pillepalle127/ESP32S3_Mesh_Snapserver/main/app_main.c

/**
 * @file app_main.c
 * @brief Initializes NVS, networking, Mesh-Lite, audio, streaming and control services.
 */
#include "esp_err.h"
#include "esp_event.h"
#include "esp_log.h"
#include "esp_netif.h"
#include "nvs_flash.h"
#include "snapcontrol.h"

#include "audio_i2s.h"
#include "audio_opus.h"
#include "audio_sink.h"
#include "device_config.h"
#include "mesh_client.h"
#include "mesh_root.h"
#include "snapserver.h"
#include "status_led.h"
#include "pots.h"
#include "power_button.h"
#include "voice_announce.h"
#include "webconfig.h"

static const char *TAG = "APP";

static esp_err_t initialize_nvs(void)
{
    esp_err_t result = nvs_flash_init();

    if (result == ESP_ERR_NVS_NO_FREE_PAGES ||
        result == ESP_ERR_NVS_NEW_VERSION_FOUND) {
        ESP_LOGW(
            TAG,
            "NVS partition must be erased: %s",
            esp_err_to_name(result));

        result = nvs_flash_erase();
        if (result != ESP_OK) {
            ESP_LOGE(
                TAG,
                "NVS erase failed: %s",
                esp_err_to_name(result));
            return result;
        }

        result = nvs_flash_init();
    }

    if (result != ESP_OK) {
        ESP_LOGE(
            TAG,
            "NVS initialization failed: %s",
            esp_err_to_name(result));
        return result;
    }

    ESP_LOGI(TAG, "NVS initialized");
    return ESP_OK;
}

static esp_err_t initialize_network_stack(void)
{
    esp_err_t result = esp_netif_init();
    if (result != ESP_OK) {
        ESP_LOGE(
            TAG,
            "TCP/IP stack initialization failed: %s",
            esp_err_to_name(result));
        return result;
    }

    result = esp_event_loop_create_default();
    if (result != ESP_OK && result != ESP_ERR_INVALID_STATE) {
        ESP_LOGE(
            TAG,
            "Default event loop initialization failed: %s",
            esp_err_to_name(result));
        return result;
    }

    ESP_LOGI(TAG, "TCP/IP stack initialized");
    return ESP_OK;
}

void app_main(void)
{
    ESP_LOGI(TAG, "Starting ESP32-S3 Mini Snapserver");

    /* Before anything claims a pin the last switch-off may still hold, and
     * before NVS: a wake-up that goes back to sleep must not count as a
     * boot of a pin set on trial (device_config_load()). */
    power_button_boot();

    ESP_ERROR_CHECK(initialize_nvs());
    ESP_ERROR_CHECK(initialize_network_stack());
    ESP_ERROR_CHECK(device_config_load());

    device_config_t cfg;
    device_config_get(&cfg);
    /* Up before the radio, so the very first thing the LED shows is that
     * the board is alive and the GPIO is right. */
    (void)status_led_start();

    /* Early, so the device can be switched off even if the mesh hangs.
     * Not fatal: without the button it simply stays on. */
    {
        device_pins_t pins;
        device_config_get_pins(&pins);
        const esp_err_t button_result = power_button_start(&pins);
        if (button_result != ESP_OK && button_result != ESP_ERR_NOT_SUPPORTED) {
            ESP_LOGW(TAG, "Power button unavailable: %s", esp_err_to_name(button_result));
        }
    }

    const bool client_role = (cfg.role == DEVICE_ROLE_CLIENT);

    esp_err_t result = client_role ? mesh_client_start() : mesh_root_start();
    if (result != ESP_OK) {
        ESP_LOGE(
            TAG,
            "Mesh %s initialization failed: %s",
            client_role ? "client" : "root",
            esp_err_to_name(result));
        ESP_ERROR_CHECK(result);
    }

    /*
     * Bring the config page up before audio: if I2S/Opus init fails below,
     * ESP_ERROR_CHECK() still panics and reboots the device (that failure
     * stays fatal, unchanged), but the panic-and-reboot loop at least
     * leaves a window where the provisioning/mesh AP and config page were
     * already reachable, instead of never existing at all.
     */
    ESP_ERROR_CHECK(webconfig_start());

    /*
     * Both roles need the physical I2S bus (the client plays out over the
     * same DSP/output stage the server uses, and also captures its own
     * local-input substitute source from it). audio_i2s_start() is
     * idempotent, so the server's subsequent audio_opus_start() -- which
     * also calls it -- is a harmless no-op the second time.
     */
    ESP_ERROR_CHECK(audio_i2s_start());

    /* The volume set for this speaker on the page or in the app. */
    {
        device_local_volume_t local_volume;
        device_config_get_local_volume(&local_volume);
        audio_i2s_set_user_volume(local_volume.percent, local_volume.muted != 0U);
    }

    const audio_dsp_params_t dsp_params = {
        .bypass = cfg.dsp_bypass,
        .crossover_hz = (float)cfg.crossover_hz,
        .sub_gain_db = cfg.sub_gain_db,
        .wideband_gain_db = cfg.wideband_gain_db,
        .sub_hpf_hz = (float)cfg.sub_hpf_hz,
        .sub_invert = cfg.sub_invert != 0U,
        .comp_enable = cfg.comp_enable != 0U,
        .comp_threshold_db = (float)cfg.comp_threshold_db,
        .comp_ratio = (float)cfg.comp_ratio_x10 / 10.0f,
        .comp_makeup_db = (float)cfg.comp_makeup_db,
        .sub_channel = cfg.sub_channel,
        .wideband_channel = cfg.wideband_channel,
    };
    ESP_ERROR_CHECK(audio_i2s_set_dsp_params(&dsp_params));

    /*
     * Not fatal: without a volume knob the output stage stays at the full
     * volume it defaults to, and without a delay knob the trim from the
     * config applies -- exactly what a board with nothing fitted should do.
     */
    device_pots_t pots;
    device_config_get_pots(&pots);
    result = pots_start(&pots);
    if (result != ESP_OK && result != ESP_ERR_NOT_SUPPORTED) {
        ESP_LOGW(TAG,
                 "Knob inputs unavailable: %s -- full volume, delay trim from config",
                 esp_err_to_name(result));
    }

    if (client_role) {
        ESP_ERROR_CHECK(audio_sink_start());

        /* The server's last volume for this client, until it sends a new one. */
        {
            device_local_volume_t stream_volume;
            device_config_get_stream_volume(&stream_volume);
            audio_sink_set_volume(stream_volume.percent, stream_volume.muted != 0U);
        }
        audio_sink_set_source_mode(cfg.source_mode);
        audio_sink_set_local_input_threshold_db(cfg.local_input_threshold_db);
        audio_sink_set_delay_trim_ms(cfg.delay_trim_ms);
        /* After the configured trim, so the knob's first reading wins. */
        pots_enable_delay(cfg.role, cfg.buffer_ms);

        result = voice_receive_start();
        if (result != ESP_OK) {
            ESP_LOGW(
                TAG,
                "Voice announcement receiver failed to start: %s -- "
                "music playback is unaffected, announcements just won't "
                "be heard on this device",
                esp_err_to_name(result));
        }

        /* Everything that touches a configured pin is up. */
        device_config_confirm_pins();

        ESP_LOGI(
            TAG,
            "ESP32-S3 Snapclient started: mesh relay, local I2S input as "
            "alternate source, Snapcast mono Opus playback");
        return;
    }

    /*
     * Hold this device's own speaker back by the same amount every client
     * delays the stream, otherwise the server -- which hears a frame right
     * after capturing it -- runs a full bufferMs ahead of them in the same
     * room. The clients' scheduler uses chunk_ts + bufferMs - latency +
     * delay_trim_ms; latency is per-client and always 0 today, so the same
     * rule here is buffer_ms + delay_trim_ms. The buffer is sized for the
     * full delay_trim_ms range so the trim stays adjustable while playing.
     */
    const int32_t local_delay_ms = (int32_t)cfg.buffer_ms + cfg.delay_trim_ms;
    ESP_ERROR_CHECK(audio_i2s_set_output_delay(
        (uint32_t)(local_delay_ms > 0 ? local_delay_ms : 0),
        (uint32_t)cfg.buffer_ms + DEVICE_CONFIG_DELAY_TRIM_MAX_MS));
    /* After the delay line exists and holds the configured trim, so the
     * knob's first reading replaces it rather than racing it. */
    pots_enable_delay(cfg.role, cfg.buffer_ms);

    result = audio_opus_start();
    if (result != ESP_OK) {
        ESP_LOGE(
            TAG,
            "Opus audio initialization failed: %s",
            esp_err_to_name(result));
        ESP_ERROR_CHECK(result);
    }
    audio_opus_set_bitrate((int32_t)cfg.opus_bitrate);
    audio_opus_set_complexity((int32_t)cfg.opus_complexity);

    result = snapserver_start();
    if (result == ESP_OK) {
        /* The server always plays its own local output, so green from here
         * on and the brightness follows what leaves its crossover. */
        status_led_set_state(STATUS_LED_PLAYING);
    }

    if (result != ESP_OK) {
        ESP_LOGE(
            TAG,
            "Snapserver initialization failed: %s",
            esp_err_to_name(result));
        ESP_ERROR_CHECK(result);
    }
	ESP_ERROR_CHECK(snapcontrol_start());

    result = voice_announce_start();
    if (result != ESP_OK) {
        ESP_LOGW(
            TAG,
            "Voice announcement server failed to start: %s -- "
            "music streaming is unaffected, announcements just won't be "
            "available",
            esp_err_to_name(result));
    }

    device_config_confirm_pins();

    ESP_LOGI(
        TAG,
        "ESP32-S3 Snapserver started: TinySine stereo input, PCM5102A stereo output, Snapcast mono Opus");
}
