pillepalle127/ESP32S3_Mesh_Snapserver/main/snapclient.c

/**
 * @file snapclient.c
 * @brief Snapcast protocol client -- TCP connection, Hello, CodecHeader,
 *        WireChunk/Opus decode, feeding audio_sink.c.
 *
 * See snapclient.h for provenance.
 *
 * Periodic SNAP_MSG_TIME requests serve two purposes at once. They carry
 * the clock synchronisation (four-timestamp exchange, least-delayed
 * measurement of a sliding window wins -- see handle_time_reply()), whose
 * result feeds audio_sink.c's playback scheduler. They are also the
 * keepalive the server requires: its client_task() drops a connection
 * after CLIENT_RECV_TIMEOUT_US (30 s, see snapserver.c) of silence *from*
 * the client, which a real Snapcast client never hits precisely because
 * its own time requests count as inbound traffic. Without them our client
 * was disconnected every ~30 s despite a perfectly healthy stream
 * (confirmed on-device, 2026-09-17).
 */
#include "snapclient.h"

#include <errno.h>
#include <fcntl.h>
#include <stdio.h>
#include <stdlib.h>
#include <string.h>
#include <sys/socket.h>
#include <sys/time.h>
#include <sys/select.h>
#include <netdb.h>
#include <unistd.h>

#include "freertos/FreeRTOS.h"
#include "freertos/event_groups.h"
#include "freertos/task.h"

#include "audio_sink.h"
#include "device_config.h"
#include "cJSON.h"
#include "esp_heap_caps.h"
#include "esp_log.h"
#include "esp_mac.h"
#include "esp_timer.h"
#include "status_led.h"
#include "opus.h"
#include "sdkconfig.h"
#if CONFIG_SNAPSERVER_ENABLE_MESH_LITE
#include "esp_mesh_lite.h"
#endif

static const char *TAG = "SNAPCLIENT";

typedef enum {
    SNAP_MSG_BASE            = 0,
    SNAP_MSG_CODEC_HEADER    = 1,
    SNAP_MSG_WIRE_CHUNK      = 2,
    SNAP_MSG_SERVER_SETTINGS = 3,
    SNAP_MSG_TIME            = 4,
    SNAP_MSG_HELLO           = 5,
    /* Ours: a config request from our own server, answered with the same
     * type -- see snapserver_remote_request() on the server side. */
    SNAP_MSG_SNAPMESH_CONFIG = 100,
} snap_msg_type_t;

typedef struct __attribute__((packed)) {
    uint16_t type;
    uint16_t id;
    uint16_t refers_to;
    int32_t sent_sec;
    int32_t sent_usec;
    int32_t received_sec;
    int32_t received_usec;
    uint32_t size;
} snap_base_t;

#define EVT_NETWORK_AVAILABLE BIT0
#define EVT_STATE_CHANGED     BIT1

#define SNAP_SAMPLE_RATE_DEFAULT 48000
#define SNAP_CHANNELS_DEFAULT    1

/* Opus allows up to 120 ms per packet at 48 kHz. */
#define OPUS_MAX_FRAME_SAMPLES 5760
#define OPUS_PCM_MAX_CHANNELS  2
#define OPUS_PCM_BUFFER_SAMPLES (OPUS_MAX_FRAME_SAMPLES * OPUS_PCM_MAX_CHANNELS)
#define OPUS_PCM_BUFFER_BYTES (OPUS_PCM_BUFFER_SAMPLES * sizeof(opus_int16))

#define SNAP_MESSAGE_BUFFER_SIZE 8192
#define SNAP_DISCARD_BUFFER_SIZE 2048
/* Largest config answer our server accepts (its RX_MAX). */
#define SNAP_CONFIG_ANSWER_MAX 4096

#define SNAP_TASK_STACK_SIZE 12288
#define SNAP_TASK_PRIORITY   6
#define SNAP_TASK_CORE       0

#define SNAP_CONNECT_TIMEOUT_MS  1500
#define SNAP_CONNECT_RETRY_MS     500
#define SNAP_RECONNECT_DELAY_MS  1000

/*
 * Per-recv() timeout, and how long the stream may stay completely silent
 * before the connection counts as dead.
 *
 * Without these the socket is blocking with no timeout at all, so a link
 * that dies without a TCP FIN or RST -- the parent going away, the AP
 * dropping us, a half-open connection after a roam -- leaves read_full()
 * parked in recv() forever. The task never reaches its reconnect path, the
 * ring never refills and the speaker stays silent until someone reboots it.
 *
 * The server sends a WireChunk every 20 ms, so several seconds of nothing
 * cannot happen on a healthy connection.
 */
/*
 * Consecutive failed connects before the path itself is declared the
 * problem. Measured on device, an attempt takes about 2 s, so this is some
 * 20 s of getting nowhere.
 *
 * It can be this short because a server restart does not reach the counter
 * at all: the AP goes down with it, the client is disassociated, and
 * snap_task blocks on EVT_NETWORK_AVAILABLE instead of counting. Failures
 * only accumulate while the client is associated and holds a lease but
 * still cannot reach the server -- a duplicate address after the server's
 * DHCP table was lost, a dead path, a mesh island. None of those recover on
 * their own, so waiting longer only costs silence.
 */
#define SNAP_UNREACHABLE_ATTEMPTS    10

#define SNAP_RECV_TIMEOUT_US   2000000
#define SNAP_STALL_TIMEOUT_US  6000000

/* read_full(): distinguishes "nothing arrived yet" from a real failure. */
#define SNAP_READ_TIMEOUT 1

/*
 * Time-request cadence. Fast while the measurement window is still filling
 * so the offset converges within a couple of seconds after connecting,
 * then slow. Both are well under CLIENT_RECV_TIMEOUT_US (30 s,
 * snapserver.c), so these double as the keepalive that stops the server
 * from dropping an otherwise silent client.
 */
#define SNAP_TIME_FAST_INTERVAL_US  (200LL * 1000LL)
#define SNAP_TIME_SLOW_INTERVAL_US  (1000LL * 1000LL)

/*
 * Offset estimates are kept in a sliding window. Only the least-delayed
 * third of it is used: in a multi-hop mesh the RTT distribution has a long
 * tail (retries, parent scans), and a delayed packet biases its own offset
 * estimate by roughly half the excess delay. Through those a straight line
 * is fitted -- offset now plus the crystals' drift -- and its value at the
 * present moment is published.
 *
 * Was: the single fastest of the last 12 measurements. When it left the
 * window the clock jumped by that sample's own error, a few ms, and it was
 * up to 12 s old while the crystals drift ~60 us/s apart. Every client
 * wandered a few ms back and forth on its own, the stereo image with it
 * (2026-10-02).
 */
#define SNAP_TIME_WINDOW 64
#define SNAP_TIME_MIN_FIT 3

/* A measurement this far off the fitted line means the server's clock
 * moved (it adopted a PC client's wall clock); start over. */
#define SNAP_TIME_JUMP_US (100LL * 1000LL)

/* Discard obviously broken measurements instead of letting them into the
 * window at all. */
#define SNAP_TIME_MAX_RTT_US (2LL * 1000000LL)

/* Also read by snapclient_get_server() from the HTTP task. */
static volatile int s_sock = -1;
static volatile bool s_run = true;
static volatile bool s_network_available;
static bool s_task_started;
static EventGroupHandle_t s_evt;

static char s_host[64];
/* s_host is written from the event handler and read by the client task. */
static portMUX_TYPE s_host_lock = portMUX_INITIALIZER_UNLOCKED;
static void (*s_host_resolver)(char *out, size_t out_len);
static void (*s_unreachable_cb)(void);
static char *(*s_config_handler)(const char *json, size_t len);
static uint16_t s_port = 1704;

static char s_codec[16];
static uint32_t s_codec_sample_rate = SNAP_SAMPLE_RATE_DEFAULT;
static uint16_t s_codec_channels = SNAP_CHANNELS_DEFAULT;

static OpusDecoder *s_opus_decoder;
static opus_int16 *s_opus_pcm;
static int16_t *s_mono_pcm; /* opus_decode() output down-mixed to mono */

typedef struct {
    int64_t rtt_us;
    int64_t offset_us; /* server clock minus local esp_timer clock */
    int64_t local_us;  /* esp_timer midway through the exchange */
} time_measurement_t;

static time_measurement_t s_time_window[SNAP_TIME_WINDOW];
static size_t s_time_window_count;
static size_t s_time_window_next;
/* Last published offset, for the jump check and the log. */
static int64_t s_time_published_us;
static uint32_t s_time_publish_count;

static uint16_t s_time_request_id;
static int64_t s_time_request_sent_us;
static bool s_time_request_pending;

static int send_full(int socket_fd, const void *buffer, size_t length)
{
    const uint8_t *data = (const uint8_t *)buffer;
    size_t sent_total = 0;

    while (sent_total < length) {
        const int sent = send(socket_fd, data + sent_total, length - sent_total, 0);
        if (sent < 0) {
            if (errno == EINTR) {
                continue;
            }
            return -1;
        }
        if (sent == 0) {
            return -1;
        }
        sent_total += (size_t)sent;
    }
    return 0;
}

static int read_full(int socket_fd, void *buffer, size_t length)
{
    uint8_t *data = (uint8_t *)buffer;
    size_t received_total = 0;

    while (received_total < length) {
        const int received = recv(socket_fd, data + received_total, length - received_total, 0);
        if (received < 0) {
            if (errno == EINTR) {
                continue;
            }
            if (errno == EAGAIN || errno == EWOULDBLOCK) {
                /*
                 * Only reportable while nothing of this message has arrived;
                 * mid-message the caller has no way to resume, so keep
                 * waiting and let the stall watchdog end the connection.
                 */
                if (received_total == 0U) {
                    return SNAP_READ_TIMEOUT;
                }
                continue;
            }
            return -1;
        }
        if (received == 0) {
            return -1;
        }
        received_total += (size_t)received;
    }
    return 0;
}

/*
 * read_full() for the part of a message that follows its header. There is no
 * resync point once the header is gone, so a single quiet recv() must not end
 * the connection -- only the overall stall budget may.
 */
static int read_full_wait(int socket_fd, void *buffer, size_t length)
{
    const int64_t deadline_us = esp_timer_get_time() + SNAP_STALL_TIMEOUT_US;

    for (;;) {
        const int rc = read_full(socket_fd, buffer, length);
        if (rc != SNAP_READ_TIMEOUT) {
            return rc;
        }
        if (esp_timer_get_time() >= deadline_us) {
            ESP_LOGW(TAG, "Payload stalled mid-message, dropping connection");
            return -1;
        }
    }
}

static int tcp_connect(void)
{
    if (!s_network_available || !s_run) {
        errno = ENETDOWN;
        return -1;
    }

    struct addrinfo hints = {
        .ai_family = AF_INET,
        .ai_socktype = SOCK_STREAM,
    };
    struct addrinfo *result = NULL;
    char port_text[8];

    if (snprintf(port_text, sizeof(port_text), "%u", (unsigned)s_port) >= (int)sizeof(port_text)) {
        return -1;
    }

    /*
     * Re-resolved per attempt, not cached: after a parent change the root is
     * often reachable under a different address, and nothing else would tell
     * us. Cheap -- a config read and one mesh-lite call.
     */
    if (s_host_resolver != NULL) {
        char resolved[sizeof(s_host)];
        resolved[0] = '\0';
        s_host_resolver(resolved, sizeof(resolved));
        snapclient_set_server_host(resolved);
    }

    char host[sizeof(s_host)];
    portENTER_CRITICAL(&s_host_lock);
    strlcpy(host, s_host, sizeof(host));
    portEXIT_CRITICAL(&s_host_lock);

    if (getaddrinfo(host, port_text, &hints, &result) != 0 || result == NULL) {
        ESP_LOGW(TAG, "getaddrinfo failed for %s", host);
        return -1;
    }

    const int socket_fd = socket(result->ai_family, result->ai_socktype, result->ai_protocol);
    if (socket_fd < 0) {
        ESP_LOGW(TAG, "socket() failed, errno=%d", errno);
        freeaddrinfo(result);
        return -1;
    }

    const int original_flags = fcntl(socket_fd, F_GETFL, 0);
    if (original_flags < 0 || fcntl(socket_fd, F_SETFL, original_flags | O_NONBLOCK) < 0) {
        ESP_LOGW(TAG, "Setting socket nonblocking failed, errno=%d", errno);
        close(socket_fd);
        freeaddrinfo(result);
        return -1;
    }

    const int connect_result = connect(socket_fd, result->ai_addr, result->ai_addrlen);
    if (connect_result != 0 && errno != EINPROGRESS) {
        ESP_LOGW(TAG, "connect() to %s:%u failed immediately (errno=%d)",
                 s_host, (unsigned)s_port, errno);
        close(socket_fd);
        freeaddrinfo(result);
        return -1;
    }

    if (connect_result != 0) {
        fd_set write_set;
        fd_set error_set;
        FD_ZERO(&write_set);
        FD_ZERO(&error_set);
        FD_SET(socket_fd, &write_set);
        FD_SET(socket_fd, &error_set);

        struct timeval timeout = {
            .tv_sec = SNAP_CONNECT_TIMEOUT_MS / 1000,
            .tv_usec = (SNAP_CONNECT_TIMEOUT_MS % 1000) * 1000,
        };

        const int select_result = select(socket_fd + 1, NULL, &write_set, &error_set, &timeout);
        if (select_result <= 0) {
            ESP_LOGW(TAG, "TCP connect to %s:%u aborted (%s)",
                     s_host, (unsigned)s_port, select_result == 0 ? "timeout" : "select error");
            close(socket_fd);
            freeaddrinfo(result);
            return -1;
        }

        int socket_error = 0;
        socklen_t error_length = sizeof(socket_error);
        if (getsockopt(socket_fd, SOL_SOCKET, SO_ERROR, &socket_error, &error_length) != 0 ||
            socket_error != 0) {
            ESP_LOGW(TAG, "TCP connect to %s:%u failed (errno=%d)",
                     s_host, (unsigned)s_port, socket_error);
            close(socket_fd);
            freeaddrinfo(result);
            return -1;
        }
    }

    freeaddrinfo(result);

    if (!s_network_available || !s_run) {
        shutdown(socket_fd, SHUT_RDWR);
        close(socket_fd);
        errno = ENETDOWN;
        return -1;
    }

    if (fcntl(socket_fd, F_SETFL, original_flags) < 0) {
        ESP_LOGW(TAG, "Resetting socket to blocking failed, errno=%d", errno);
        close(socket_fd);
        return -1;
    }

    const struct timeval recv_timeout = {
        .tv_sec = (time_t)(SNAP_RECV_TIMEOUT_US / 1000000),
        .tv_usec = (suseconds_t)(SNAP_RECV_TIMEOUT_US % 1000000),
    };
    if (setsockopt(socket_fd, SOL_SOCKET, SO_RCVTIMEO,
                   &recv_timeout, sizeof(recv_timeout)) < 0) {
        ESP_LOGW(TAG, "Could not set receive timeout, errno=%d", errno);
    }

    ESP_LOGI(TAG, "Connected to Snapserver %s:%u", s_host, (unsigned)s_port);
    status_led_set_state(STATUS_LED_PLAYING);
    return socket_fd;
}

/* 0 when unknown: not attached yet, or a build without Mesh-Lite. */
static uint8_t own_mesh_level(void)
{
#if CONFIG_SNAPSERVER_ENABLE_MESH_LITE
    return esp_mesh_lite_get_level();
#else
    return 0U;
#endif
}

static int send_hello(int socket_fd)
{
    uint8_t mac[6] = {0};
    if (esp_read_mac(mac, ESP_MAC_WIFI_STA) != ESP_OK) {
        ESP_LOGE(TAG, "Could not read STA MAC");
        return -1;
    }

    char mac_text[18];
    snprintf(mac_text, sizeof(mac_text), "%02X:%02X:%02X:%02X:%02X:%02X",
             mac[0], mac[1], mac[2], mac[3], mac[4], mac[5]);

    char client_name[32];
    snprintf(client_name, sizeof(client_name), "ESP32S3-SnapMesh-%02X%02X", mac[4], mac[5]);

    char hello_json[384];
    const int hello_length = snprintf(hello_json, sizeof(hello_json),
        "{"
        "\"MAC\":\"%s\","
        "\"HostName\":\"%s\","
        "\"Version\":\"0.27.0\","
        "\"ClientName\":\"%s\","
        "\"OS\":\"esp-idf\","
        "\"Arch\":\"xtensa\","
        "\"Instance\":1,"
        "\"SnapStreamProtocolVersion\":2,"
        /* Tells our own server that this client understands the
         * "announcement" flag in ServerSettings and silences its music by
         * itself, so it must not be muted outright for an announcement it
         * may well receive. A stock Snapserver ignores the field. */
        "\"SnapMesh\":1,"
        /* Our mesh level (root = 1), for the server's device list.
         * Also ignored by a stock Snapserver. */
        "\"MeshLevel\":%u"
        "}",
        mac_text, client_name, client_name, (unsigned)own_mesh_level());

    if (hello_length <= 0 || hello_length >= (int)sizeof(hello_json)) {
        ESP_LOGE(TAG, "Hello JSON invalid or too long");
        return -1;
    }

    const uint32_t payload_length = (uint32_t)hello_length;
    snap_base_t header = {0};
    header.type = SNAP_MSG_HELLO;
    header.size = (uint32_t)sizeof(payload_length) + payload_length;

    if (send_full(socket_fd, &header, sizeof(header)) != 0 ||
        send_full(socket_fd, &payload_length, sizeof(payload_length)) != 0 ||
        send_full(socket_fd, hello_json, payload_length) != 0) {
        ESP_LOGE(TAG, "Sending Hello failed");
        return -1;
    }

    ESP_LOGI(TAG, "Sent Hello: Client=%s, ID=%s", client_name, mac_text);
    return 0;
}

static void time_sync_reset(void)
{
    s_time_window_count = 0;
    s_time_window_next = 0;
    s_time_request_pending = false;
    audio_sink_set_server_time_offset(0, false);
}

/*
 * Publishes the clock offset at this moment, see SNAP_TIME_WINDOW.
 */
static void publish_offset(void)
{
    const size_t n = s_time_window_count;
    if (n == 0U) {
        return;
    }

    /* The fastest third, at least SNAP_TIME_MIN_FIT, by selection. */
    size_t order[SNAP_TIME_WINDOW];
    for (size_t i = 0; i < n; ++i) {
        order[i] = i;
    }
    size_t used = n / 3U;
    if (used < SNAP_TIME_MIN_FIT) {
        used = (n < SNAP_TIME_MIN_FIT) ? n : SNAP_TIME_MIN_FIT;
    }
    for (size_t i = 0; i < used; ++i) {
        size_t best = i;
        for (size_t j = i + 1U; j < n; ++j) {
            if (s_time_window[order[j]].rtt_us < s_time_window[order[best]].rtt_us) {
                best = j;
            }
        }
        const size_t tmp = order[i];
        order[i] = order[best];
        order[best] = tmp;
    }

    /* Least squares, x in s before now, y in us relative to the fastest
     * sample; the intercept is the offset now. */
    const int64_t now_us = esp_timer_get_time();
    const int64_t base_us = s_time_window[order[0]].offset_us;
    double sx = 0.0, sy = 0.0, sxx = 0.0, sxy = 0.0;
    for (size_t i = 0; i < used; ++i) {
        const time_measurement_t *m = &s_time_window[order[i]];
        const double x = (double)(m->local_us - now_us) / 1e6;
        const double y = (double)(m->offset_us - base_us);
        sx += x;
        sy += y;
        sxx += x * x;
        sxy += x * y;
    }
    const double count = (double)used;
    const double denom = count * sxx - sx * sx;
    double drift_ppm = 0.0;
    double offset_now = sy / count;
    /* A slope needs samples spread over time; a wild one (several crystals'
     * worth) means too few or bad ones, and the mean is safer. */
    if (used >= SNAP_TIME_MIN_FIT && denom > 1e-9) {
        const double slope = (count * sxy - sx * sy) / denom;
        if (slope > -500.0 && slope < 500.0) {
            drift_ppm = slope;
            offset_now = (sy - slope * sx) / count;
        }
    }

    const int64_t offset_us = base_us + (int64_t)offset_now;
    const int64_t step_us = offset_us - s_time_published_us;
    s_time_published_us = offset_us;
    audio_sink_set_server_time_offset(offset_us, true);

    if ((++s_time_publish_count % 30U) == 0U) {
        ESP_LOGI(TAG, "Time sync: %u of %u samples, rtt %lld..%lld us, drift %+.1f ppm, last step %+lld us",
                 (unsigned)used, (unsigned)n,
                 (long long)s_time_window[order[0]].rtt_us,
                 (long long)s_time_window[order[used - 1U]].rtt_us,
                 drift_ppm, (long long)step_us);
    }
}

/*
 * sent_sec/sent_usec carry esp_timer uptime, not a real wall clock -- the
 * server's handle_time() only adopts a client timestamp past
 * SNAP_CLOCK_PLAUSIBLE_MIN_SEC, so ours can never move its wall-clock base.
 * Payload is the 8-byte {latency_sec, latency_usec} the protocol expects,
 * sent as zero because the server ignores it and only reflects timestamps.
 */
static int send_time_request(int socket_fd)
{
    const int64_t now_us = esp_timer_get_time();

    if (++s_time_request_id == 0U) {
        s_time_request_id = 1U; /* 0 is what unsolicited messages carry */
    }

    snap_base_t header = {0};
    header.type = SNAP_MSG_TIME;
    header.id = s_time_request_id;
    header.sent_sec = (int32_t)(now_us / 1000000LL);
    header.sent_usec = (int32_t)(now_us % 1000000LL);
    header.size = 8U;

    const int32_t latency[2] = {0, 0};

    if (send_full(socket_fd, &header, sizeof(header)) != 0 ||
        send_full(socket_fd, latency, sizeof(latency)) != 0) {
        return -1;
    }

    s_time_request_sent_us = now_us;
    s_time_request_pending = true;
    return 0;
}

/*
 * Standard four-timestamp exchange:
 *   t1 local send, t2 server receive, t3 server send, t4 local receive.
 * The server fills t2 into received_* and t3 into sent_* (see
 * snapserver.c's handle_time()/send_msg_unlocked()), so both directions
 * can be separated instead of assuming a symmetric path.
 */
static void handle_time_reply(const snap_base_t *header)
{
    if (!s_time_request_pending || header->refers_to != s_time_request_id) {
        return;
    }
    s_time_request_pending = false;

    const int64_t t1 = s_time_request_sent_us;
    const int64_t t4 = esp_timer_get_time();
    const int64_t t2 = (int64_t)header->received_sec * 1000000LL + header->received_usec;
    const int64_t t3 = (int64_t)header->sent_sec * 1000000LL + header->sent_usec;

    const int64_t rtt_us = (t4 - t1) - (t3 - t2);
    if (rtt_us < 0 || rtt_us > SNAP_TIME_MAX_RTT_US) {
        return;
    }

    const int64_t offset_us = ((t2 - t1) + (t3 - t4)) / 2;

    if (s_time_window_count >= SNAP_TIME_MIN_FIT) {
        const int64_t off_line_us = offset_us - s_time_published_us;
        if (off_line_us > SNAP_TIME_JUMP_US + rtt_us || off_line_us < -SNAP_TIME_JUMP_US - rtt_us) {
            ESP_LOGW(TAG, "Server clock moved by %lld ms, time sync starts over",
                     (long long)(off_line_us / 1000LL));
            s_time_window_count = 0;
            s_time_window_next = 0;
        }
    }

    s_time_window[s_time_window_next].rtt_us = rtt_us;
    s_time_window[s_time_window_next].offset_us = offset_us;
    s_time_window[s_time_window_next].local_us = t1 + (t4 - t1) / 2;
    s_time_window_next = (s_time_window_next + 1U) % SNAP_TIME_WINDOW;
    if (s_time_window_count < SNAP_TIME_WINDOW) {
        s_time_window_count++;
    }

    publish_offset();
}

static esp_err_t opus_decoder_prepare(void)
{
    if (s_opus_decoder != NULL && s_opus_pcm != NULL) {
        return ESP_OK;
    }

    if (s_opus_pcm == NULL) {
        s_opus_pcm = heap_caps_malloc(OPUS_PCM_BUFFER_BYTES, MALLOC_CAP_SPIRAM | MALLOC_CAP_8BIT);
        if (s_opus_pcm == NULL) {
            s_opus_pcm = heap_caps_malloc(OPUS_PCM_BUFFER_BYTES, MALLOC_CAP_8BIT);
        }
        if (s_opus_pcm == NULL) {
            ESP_LOGE(TAG, "No memory for %u B Opus PCM buffer", (unsigned)OPUS_PCM_BUFFER_BYTES);
            return ESP_ERR_NO_MEM;
        }
    }
    if (s_mono_pcm == NULL) {
        s_mono_pcm = heap_caps_malloc(OPUS_MAX_FRAME_SAMPLES * sizeof(int16_t),
                                      MALLOC_CAP_SPIRAM | MALLOC_CAP_8BIT);
        if (s_mono_pcm == NULL) {
            s_mono_pcm = heap_caps_malloc(OPUS_MAX_FRAME_SAMPLES * sizeof(int16_t), MALLOC_CAP_8BIT);
        }
        if (s_mono_pcm == NULL) {
            ESP_LOGE(TAG, "No memory for mono downmix buffer");
            return ESP_ERR_NO_MEM;
        }
    }

    int opus_error = OPUS_OK;
    s_opus_decoder = opus_decoder_create((opus_int32)s_codec_sample_rate,
                                         (int)s_codec_channels, &opus_error);
    if (s_opus_decoder == NULL || opus_error != OPUS_OK) {
        ESP_LOGE(TAG, "opus_decoder_create failed: %s (%d)",
                 opus_strerror(opus_error), opus_error);
        s_opus_decoder = NULL;
        return ESP_FAIL;
    }

    ESP_LOGI(TAG, "Opus decoder ready: %u Hz, %u channel(s)",
             (unsigned)s_codec_sample_rate, (unsigned)s_codec_channels);
    return ESP_OK;
}

static void opus_decoder_reset(void)
{
    if (s_opus_decoder != NULL) {
        opus_decoder_destroy(s_opus_decoder);
        s_opus_decoder = NULL;
    }
}

/*
 * Snapcast CodecHeader:
 *   uint32_t codec_name_length
 *   char     codec_name[codec_name_length]
 *   uint32_t codec_specific_length
 *   uint8_t  codec_specific[codec_specific_length]
 *
 * Our own server's codec_specific payload for "opus" (see snapserver.c's
 * send_codec_header()) is 12 bytes: uint32 opus_id, uint32 rate, uint16
 * bits, uint16 channels. Only "opus" is handled -- our server never sends
 * "pcm".
 */
static void handle_codec_header(const uint8_t *payload, uint32_t size)
{
    if (payload == NULL || size < sizeof(uint32_t)) {
        ESP_LOGW(TAG, "CodecHeader too small: %lu B", (unsigned long)size);
        return;
    }

    uint32_t name_length = 0;
    memcpy(&name_length, payload, sizeof(name_length));

    if (name_length == 0 || name_length >= sizeof(s_codec) ||
        sizeof(uint32_t) + name_length + sizeof(uint32_t) > size) {
        ESP_LOGE(TAG, "CodecHeader invalid: size=%lu name_len=%lu",
                 (unsigned long)size, (unsigned long)name_length);
        return;
    }

    memset(s_codec, 0, sizeof(s_codec));
    memcpy(s_codec, payload + sizeof(uint32_t), name_length);

    const uint8_t *specific = payload + sizeof(uint32_t) + name_length;
    uint32_t specific_length = 0;
    memcpy(&specific_length, specific, sizeof(specific_length));
    specific += sizeof(specific_length);

    const uint32_t specific_available =
        size - (uint32_t)(sizeof(uint32_t) + name_length + sizeof(uint32_t));
    if (specific_length > specific_available) {
        ESP_LOGE(TAG, "CodecHeader specific data truncated");
        return;
    }

    opus_decoder_reset();

    if (strcmp(s_codec, "opus") != 0) {
        ESP_LOGW(TAG, "Unsupported codec: %s", s_codec);
        return;
    }

    if (specific_length != 12U) {
        ESP_LOGW(TAG,
                 "Unexpected opus codec-specific length %lu, falling back to "
                 "%u Hz / %u channel(s)",
                 (unsigned long)specific_length, SNAP_SAMPLE_RATE_DEFAULT, SNAP_CHANNELS_DEFAULT);
        s_codec_sample_rate = SNAP_SAMPLE_RATE_DEFAULT;
        s_codec_channels = SNAP_CHANNELS_DEFAULT;
    } else {
        uint32_t rate = SNAP_SAMPLE_RATE_DEFAULT;
        uint16_t bits = 16;
        uint16_t channels = SNAP_CHANNELS_DEFAULT;
        memcpy(&rate, specific + 4, sizeof(rate));
        memcpy(&bits, specific + 8, sizeof(bits));
        memcpy(&channels, specific + 10, sizeof(channels));
        (void)bits; /* S16LE is the only format micro-opus decodes to here */

        s_codec_sample_rate = rate;
        s_codec_channels = (channels == 0U || channels > OPUS_PCM_MAX_CHANNELS) ? 1U : channels;
    }

    ESP_LOGI(TAG, "CodecHeader: codec=%s, rate=%u, channels=%u",
             s_codec, (unsigned)s_codec_sample_rate, (unsigned)s_codec_channels);

    if (opus_decoder_prepare() != ESP_OK) {
        ESP_LOGE(TAG, "Opus decoder init failed after CodecHeader");
    }
}

/*
 * ServerSettings payload: uint32 json_length followed by the JSON itself,
 * e.g. {"bufferMs":3000,"latency":0,"muted":false,"volume":100}. bufferMs
 * and latency define where a chunk belongs on the playback timeline, so
 * both go straight to audio_sink.c's scheduler.
 */
static void handle_server_settings(const uint8_t *payload, uint32_t size)
{
    if (payload == NULL || size < sizeof(uint32_t)) {
        return;
    }

    uint32_t json_length = 0;
    memcpy(&json_length, payload, sizeof(json_length));
    if (json_length == 0U || json_length > size - sizeof(uint32_t)) {
        return;
    }

    char *json = malloc((size_t)json_length + 1U);
    if (json == NULL) {
        return;
    }
    memcpy(json, payload + sizeof(uint32_t), json_length);
    json[json_length] = '\0';

    cJSON *root = cJSON_Parse(json);
    free(json);
    if (root == NULL) {
        ESP_LOGW(TAG, "ServerSettings JSON unparsable");
        return;
    }

    const cJSON *buffer_ms = cJSON_GetObjectItemCaseSensitive(root, "bufferMs");
    const cJSON *latency = cJSON_GetObjectItemCaseSensitive(root, "latency");
    const cJSON *volume = cJSON_GetObjectItemCaseSensitive(root, "volume");
    const cJSON *muted = cJSON_GetObjectItemCaseSensitive(root, "muted");

    if (cJSON_IsNumber(buffer_ms)) {
        const int32_t latency_ms = cJSON_IsNumber(latency) ? (int32_t)latency->valuedouble : 0;
        ESP_LOGI(TAG, "ServerSettings: bufferMs=%d latency=%d",
                 (int)buffer_ms->valuedouble, (int)latency_ms);
        audio_sink_set_stream_timing((uint32_t)buffer_ms->valuedouble, latency_ms);
    }

    /*
     * Per-client volume. The server re-sends ServerSettings whenever it is
     * changed (see snapserver_set_client_volume()/_mute()), so this arrives
     * mid-session too, not just during the handshake -- which is what makes
     * a Snapcast control app able to set each speaker separately.
     */
    if (cJSON_IsNumber(volume) || cJSON_IsBool(muted)) {
        const int32_t percent = cJSON_IsNumber(volume) ? (int32_t)volume->valuedouble : 100;
        audio_sink_set_volume(percent, cJSON_IsTrue(muted));

        /*
         * Remembered, so the next start plays at this level right away
         * instead of at 100 % until the server's settings arrive. Only a
         * change is written; this task's stack is in internal RAM.
         */
        device_local_volume_t stored;
        device_config_get_stream_volume(&stored);
        const uint8_t clamped = (uint8_t)((percent < 0) ? 0 : (percent > 100) ? 100 : percent);
        const uint8_t now_muted = cJSON_IsTrue(muted) ? 1U : 0U;
        if (stored.percent != clamped || stored.muted != now_muted) {
            const device_local_volume_t next = { .percent = clamped, .muted = now_muted };
            (void)device_config_save_stream_volume(&next);
        }
    }

    /*
     * Our own extension: an announcement is running somewhere in the mesh.
     * Music stays silent for its duration wherever this client sits in the
     * tree; the announcement itself plays if it reaches this node (it is
     * relayed one hop past the root, see voice_announce.c). Missing field,
     * e.g. from a stock Snapserver, means no announcement.
     */
    const cJSON *announcement = cJSON_GetObjectItemCaseSensitive(root, "announcement");
    audio_sink_set_announcement(cJSON_IsTrue(announcement));

    cJSON_Delete(root);
}

/*
 * Snapcast WireChunk: int32 sec, int32 usec, uint32 audio_length, uint8_t
 * audio[audio_length]. sec/usec are the server-clock timestamp of the
 * chunk's first sample and drive the playback scheduler in audio_sink.c.
 */
static void handle_wire_chunk(const uint8_t *payload, uint32_t size)
{
    if (payload == NULL || size < 12U) {
        return;
    }

    int32_t chunk_sec = 0;
    int32_t chunk_usec = 0;
    memcpy(&chunk_sec, payload + 0, sizeof(chunk_sec));
    memcpy(&chunk_usec, payload + 4, sizeof(chunk_usec));
    const int64_t chunk_ts_us = (int64_t)chunk_sec * 1000000LL + chunk_usec;

    uint32_t audio_length = 0;
    memcpy(&audio_length, payload + 8, sizeof(audio_length));
    if (audio_length == 0U || audio_length > size - 12U) {
        return;
    }

    if (s_codec[0] == '\0' || s_opus_decoder == NULL || s_opus_pcm == NULL) {
        return;
    }

    const uint8_t *audio = payload + 12;
    const int samples_per_channel = opus_decode(s_opus_decoder, audio, (opus_int32)audio_length,
                                                s_opus_pcm, OPUS_MAX_FRAME_SAMPLES, 0);
    if (samples_per_channel < 0) {
        ESP_LOGW(TAG, "opus_decode failed: %s (%d)",
                 opus_strerror(samples_per_channel), samples_per_channel);
        return;
    }

    if (s_codec_channels == 1U) {
        audio_sink_feed_network(s_opus_pcm, (size_t)samples_per_channel, chunk_ts_us);
        return;
    }

    /* Down-mix stereo to mono to match the DSP/output stage, which always
     * runs on a single channel (see audio_i2s.c). */
    for (int i = 0; i < samples_per_channel; ++i) {
        const int32_t left = s_opus_pcm[2 * i];
        const int32_t right = s_opus_pcm[2 * i + 1];
        s_mono_pcm[i] = (int16_t)((left + right) / 2);
    }
    audio_sink_feed_network(s_mono_pcm, (size_t)samples_per_channel, chunk_ts_us);
}

/*
 * Runs the request through the config handler and sends its answer back,
 * refersTo = the request's id. On this task, which also sends the Time
 * requests, so nothing else writes to the socket meanwhile. A save stalls
 * the receive side for its flash write, which bufferMs easily covers.
 * Only a failed send is an error; a request that cannot be answered is
 * left for the server to time out.
 */
static int handle_config_request(int socket_fd, const snap_base_t *header,
                                 const uint8_t *payload)
{
    uint32_t json_len = 0;
    if (s_config_handler == NULL || header->size < sizeof(json_len)) {
        return 0;
    }
    memcpy(&json_len, payload, sizeof(json_len));
    if (json_len > header->size - sizeof(json_len)) {
        return 0;
    }

    char *answer = s_config_handler((const char *)payload + sizeof(json_len), json_len);
    if (answer == NULL) {
        return 0;
    }
    /* The server drops the whole connection over a message larger than its
     * RX_MAX (4096), so an oversized answer is replaced by an error. */
    if (strlen(answer) + sizeof(json_len) > SNAP_CONFIG_ANSWER_MAX) {
        free(answer);
        answer = strdup("{\"error\":\"answer too large\"}");
        if (answer == NULL) {
            return 0;
        }
    }
    const uint32_t answer_len = (uint32_t)strlen(answer);

    const int64_t now_us = esp_timer_get_time();
    snap_base_t reply = {0};
    reply.type = SNAP_MSG_SNAPMESH_CONFIG;
    reply.refers_to = header->id;
    reply.sent_sec = (int32_t)(now_us / 1000000LL);
    reply.sent_usec = (int32_t)(now_us % 1000000LL);
    reply.size = (uint32_t)sizeof(answer_len) + answer_len;

    const int rc = (send_full(socket_fd, &reply, sizeof(reply)) != 0 ||
                    send_full(socket_fd, &answer_len, sizeof(answer_len)) != 0 ||
                    send_full(socket_fd, answer, answer_len) != 0) ? -1 : 0;
    free(answer);
    return rc;
}

static int process_message(int socket_fd, const snap_base_t *header, const uint8_t *payload)
{
    switch (header->type) {
        case SNAP_MSG_CODEC_HEADER:
            handle_codec_header(payload, header->size);
            break;
        case SNAP_MSG_WIRE_CHUNK:
            handle_wire_chunk(payload, header->size);
            break;
        case SNAP_MSG_SERVER_SETTINGS:
            handle_server_settings(payload, header->size);
            break;
        case SNAP_MSG_TIME:
            handle_time_reply(header);
            break;
        case SNAP_MSG_SNAPMESH_CONFIG:
            return handle_config_request(socket_fd, header, payload);
        case SNAP_MSG_BASE:
        case SNAP_MSG_HELLO:
        default:
            break;
    }
    return 0;
}

static void connection_loop(int socket_fd)
{
    static uint8_t discard_buffer[SNAP_DISCARD_BUFFER_SIZE];
    static uint8_t message_buffer[SNAP_MESSAGE_BUFFER_SIZE];

    audio_sink_set_network_active(true);
    time_sync_reset();
    int64_t last_time_request_us = 0;
    int64_t last_data_us = esp_timer_get_time();

    while (s_run) {
        /*
         * Checked once per loop iteration rather than on its own timer:
         * WireChunks arrive roughly every 20 ms under normal operation, so
         * read_full() below returns often enough that this fires close to
         * on schedule without needing select()/non-blocking I/O. A truly
         * stalled connection (no data at all) never gets to send a
         * request either, but that case is already fatal on its own.
         */
        const int64_t now_us = esp_timer_get_time();
        const int64_t interval_us = (s_time_window_count < SNAP_TIME_WINDOW)
                                        ? SNAP_TIME_FAST_INTERVAL_US
                                        : SNAP_TIME_SLOW_INTERVAL_US;
        if (now_us - last_time_request_us >= interval_us) {
            if (send_time_request(socket_fd) != 0) {
                break;
            }
            last_time_request_us = now_us;
        }

        snap_base_t header;
        const int header_rc = read_full(socket_fd, &header, sizeof(header));
        if (header_rc < 0) {
            break;
        }
        if (header_rc == SNAP_READ_TIMEOUT) {
            if (esp_timer_get_time() - last_data_us >= SNAP_STALL_TIMEOUT_US) {
                ESP_LOGW(TAG, "No data for %lld s, treating connection as dead",
                         (long long)(SNAP_STALL_TIMEOUT_US / 1000000));
                break;
            }
            continue;
        }
        last_data_us = esp_timer_get_time();

        if (header.size == 0U) {
            vTaskDelay(1);
            continue;
        }

        if (header.size > sizeof(message_buffer)) {
            ESP_LOGW(TAG, "Payload too large: %lu B, discarding", (unsigned long)header.size);
            uint32_t remaining = header.size;
            while (remaining > 0U && s_run) {
                const uint32_t part =
                    (remaining > sizeof(discard_buffer)) ? (uint32_t)sizeof(discard_buffer) : remaining;
                if (read_full_wait(socket_fd, discard_buffer, part) != 0) {
                    audio_sink_set_network_active(false);
                    return;
                }
                remaining -= part;
                vTaskDelay(1);
            }
            continue;
        }

        if (read_full_wait(socket_fd, message_buffer, header.size) != 0) {
            break;
        }

        if (process_message(socket_fd, &header, message_buffer) != 0) {
            break;
        }

        /* One tick of slack per message so a burst of 20 ms Opus packets
         * (~50/s) can't starve the idle task under TCP backpressure. */
        vTaskDelay(1);
    }

    audio_sink_set_network_active(false);
}

static void wait_for_reconnect_condition(TickType_t timeout_ticks)
{
    xEventGroupWaitBits(s_evt, EVT_NETWORK_AVAILABLE | EVT_STATE_CHANGED,
                        pdTRUE, pdFALSE, timeout_ticks);
}

static void snap_task(void *arg)
{
    (void)arg;
    int failed_connects = 0;

    while (s_run) {
        if (!s_network_available) {
            xEventGroupWaitBits(s_evt, EVT_NETWORK_AVAILABLE, pdFALSE, pdTRUE, portMAX_DELAY);
            continue;
        }

        const int socket_fd = tcp_connect();
        if (socket_fd < 0) {
            if (++failed_connects >= SNAP_UNREACHABLE_ATTEMPTS) {
                failed_connects = 0;
                ESP_LOGW(TAG,
                         "No Snapserver after %d attempts; asking for a fresh "
                         "network join", SNAP_UNREACHABLE_ATTEMPTS);
                if (s_unreachable_cb != NULL) {
                    s_unreachable_cb();
                }
            }
            status_led_set_state(STATUS_LED_NO_SERVER);
            if (s_run && s_network_available) {
                wait_for_reconnect_condition(pdMS_TO_TICKS(SNAP_CONNECT_RETRY_MS));
            }
            continue;
        }

        failed_connects = 0;

        if (!s_network_available) {
            shutdown(socket_fd, SHUT_RDWR);
            close(socket_fd);
            continue;
        }

        s_sock = socket_fd;
        memset(s_codec, 0, sizeof(s_codec));
        opus_decoder_reset();

        if (send_hello(socket_fd) == 0) {
            connection_loop(socket_fd);
        }

        shutdown(socket_fd, SHUT_RDWR);
        close(socket_fd);
        if (s_sock == socket_fd) {
            s_sock = -1;
        }
        opus_decoder_reset();

        if (s_run && s_network_available) {
            status_led_set_state(STATUS_LED_NO_SERVER);
            ESP_LOGI(TAG, "Connection lost, reconnecting in %d ms", SNAP_RECONNECT_DELAY_MS);
            wait_for_reconnect_condition(pdMS_TO_TICKS(SNAP_RECONNECT_DELAY_MS));
        }
    }

    audio_sink_set_network_active(false);
    opus_decoder_reset();
    s_sock = -1;
    s_task_started = false;
    vTaskDelete(NULL);
}

void snapclient_set_host_resolver(void (*resolver)(char *out, size_t out_len))
{
    s_host_resolver = resolver;
}

void snapclient_set_unreachable_cb(void (*cb)(void))
{
    s_unreachable_cb = cb;
}

void snapclient_set_config_handler(char *(*handler)(const char *json, size_t len))
{
    s_config_handler = handler;
}

void snapclient_set_server_host(const char *host)
{
    if (host == NULL || host[0] == '\0') {
        return;
    }

    bool changed = false;
    portENTER_CRITICAL(&s_host_lock);
    if (strcmp(s_host, host) != 0) {
        strlcpy(s_host, host, sizeof(s_host));
        changed = true;
    }
    portEXIT_CRITICAL(&s_host_lock);

    if (changed) {
        ESP_LOGI(TAG, "Snapserver address is now %s", host);
    }
}

bool snapclient_get_server(char *host, size_t host_len)
{
    portENTER_CRITICAL(&s_host_lock);
    strlcpy(host, s_host, host_len);
    portEXIT_CRITICAL(&s_host_lock);
    return s_sock >= 0;
}

void snapclient_set_network_available(bool available)
{
    if (s_network_available == available) {
        return;
    }

    s_network_available = available;

    if (available) {
        ESP_LOGI(TAG, "Network up: reconnect released");
        if (s_evt != NULL) {
            xEventGroupSetBits(s_evt, EVT_NETWORK_AVAILABLE | EVT_STATE_CHANGED);
        }
        return;
    }

    ESP_LOGW(TAG, "Network down: aborting any open connection");
    status_led_set_state(STATUS_LED_NO_NETWORK);
    if (s_evt != NULL) {
        xEventGroupClearBits(s_evt, EVT_NETWORK_AVAILABLE);
        xEventGroupSetBits(s_evt, EVT_STATE_CHANGED);
    }

    const int socket_fd = s_sock;
    if (socket_fd >= 0) {
        shutdown(socket_fd, SHUT_RDWR);
    }
}

esp_err_t snapclient_start(const char *host, uint16_t port)
{
    if (s_task_started) {
        return ESP_OK;
    }
    if (host == NULL || host[0] == '\0' || port == 0U) {
        return ESP_ERR_INVALID_ARG;
    }

    portENTER_CRITICAL(&s_host_lock);
    strlcpy(s_host, host, sizeof(s_host));
    portEXIT_CRITICAL(&s_host_lock);
    s_port = port;

    if (s_evt == NULL) {
        s_evt = xEventGroupCreate();
        if (s_evt == NULL) {
            return ESP_ERR_NO_MEM;
        }
    }

    s_run = true;
    s_task_started = true;
    s_sock = -1;
    memset(s_codec, 0, sizeof(s_codec));

    if (s_network_available) {
        xEventGroupSetBits(s_evt, EVT_NETWORK_AVAILABLE);
    } else {
        xEventGroupClearBits(s_evt, EVT_NETWORK_AVAILABLE);
    }

    if (xTaskCreatePinnedToCore(snap_task, "snapclient", SNAP_TASK_STACK_SIZE, NULL,
                                SNAP_TASK_PRIORITY, NULL, SNAP_TASK_CORE) != pdPASS) {
        s_task_started = false;
        return ESP_ERR_NO_MEM;
    }

    ESP_LOGI(TAG, "Snapclient started (server %s:%u)", s_host, (unsigned)s_port);
    return ESP_OK;
}
