pillepalle127/ESP32S3_Mesh_Snapserver/main/status_led.c

/**
 * @file status_led.c
 * @brief WS2812 status/level indicator driven straight from the RMT driver.
 */
#include "status_led.h"

#include <math.h>
#include <string.h>

#include "audio_i2s.h"
#include "device_config.h"
#include "driver/rmt_encoder.h"
#include "driver/rmt_tx.h"
#include "esp_log.h"
#include "freertos/FreeRTOS.h"
#include "freertos/task.h"
#include "sdkconfig.h"

static const char *TAG = "STATUS_LED";

#if CONFIG_SNAPSERVER_STATUS_LED_ENABLE

/*
 * 10 MHz gives 100 ns per tick, which divides the WS2812 bit timings evenly
 * and keeps every duration below the 15-bit field the RMT symbol allows.
 */
#define LED_RESOLUTION_HZ   10000000
#define LED_T0H_TICKS               3   /* 0.3 us */
#define LED_T0L_TICKS               9   /* 0.9 us */
#define LED_T1H_TICKS               9   /* 0.9 us */
#define LED_T1L_TICKS               3   /* 0.3 us */
#define LED_RESET_TICKS           500   /* 50 us, comfortably over the
                                         *
                                         * datasheet's minimum */

/*
 * 30 Hz. Fast enough that the level reads as movement rather than as steps,
 * slow enough to be irrelevant next to everything else on the device -- the
 * task spends its life asleep and sends 24 bits when it wakes.
 */
#define LED_UPDATE_MS              33
#define LED_TASK_STACK           3072
#define LED_TASK_PRIORITY           1

/*
 * Level window, in dBFS of the frame RMS (20 ms), measured before the
 * volume. The peak was tried first and sat at the top: loudly mastered
 * music reaches -1 to 0 dBFS in almost every update. The RMS of the same
 * music moves between about -30 and -8 dBFS, which this window spreads
 * across the colour scale. Before that, a linear peak window after the
 * volume went dark at half volume, where the cubic curve takes 18 dB off.
 */
#define LED_LEVEL_FLOOR_DB      -35.0f
#define LED_LEVEL_CEIL_DB        -6.0f

/*
 * Floor for the meter. Not as dark as it could be, because hue is what
 * carries the level now and an almost-black LED has no readable hue.
 */
#define LED_METER_FLOOR          0.30f

/*
 * Blink periods for the states that have no audio, in updates of
 * LED_UPDATE_MS. Severity reads as rate: the worse it is, the faster it
 * blinks. Anything steady means nothing is wrong.
 */
#define LED_BLINK_FAST_PERIOD       8   /* ~260 ms, no network      */
#define LED_BLINK_SLOW_PERIOD      30   /* ~1 s, no Snapserver      */
#define LED_BLINK_CALM_PERIOD      60   /* ~2 s, provisioning AP    */

/*
 * The local input keeps the meter even without a server, since it plays
 * fine on its own. The missing server connection only shows as a short
 * blank every few seconds -- visible if watched, invisible if not. With
 * the server connected there is no blank.
 */
#define LED_LOCAL_MARK_PERIOD      91   /* ~3 s  */
#define LED_LOCAL_MARK_BLANK        3   /* ~100 ms */

/*
 * A voice announcement also keeps the meter, but pulses much faster than the
 * local-input mark -- it is meant to catch the eye as "something unusual is
 * happening right now", not just to be distinguishable on close inspection.
 */
#define LED_VOICE_MARK_PERIOD      15   /* ~500 ms */
#define LED_VOICE_MARK_BLANK        3   /* ~100 ms */

/*
 * Decay per update when the level falls: full scale to dark in three
 * updates, about 100 ms. Instant attack with a release is still what keeps
 * the meter legible, but 0.12 (over 250 ms) left it sitting near the top
 * through anything continuous.
 */
#define LED_DECAY_PER_UPDATE     0.35f

typedef struct {
    uint8_t r;
    uint8_t g;
    uint8_t b;
} led_rgb_t;

static rmt_channel_handle_t s_channel;
static rmt_encoder_handle_t s_encoder;
static volatile status_led_state_t s_state = STATUS_LED_BOOTING;
static volatile status_led_activity_t s_activity = STATUS_LED_ACTIVITY_NONE;
static volatile float s_level_db = -120.0f;
static volatile bool s_off;

/*
 * Level as hue, the way a meter with more than one LED would use position:
 * green through yellow to red. Interpolated rather than stepped, because
 * three discrete colours on a single LED read as three states, not as a
 * scale.
 */
static led_rgb_t level_colour(float level)
{
    if (level < 0.5f) {
        const float t = level * 2.0f;            /* green -> yellow */
        return (led_rgb_t){ (uint8_t)(255.0f * t), 255, 0 };
    }
    const float t = (level - 0.5f) * 2.0f;       /* yellow -> red   */
    return (led_rgb_t){ 255, (uint8_t)(255.0f * (1.0f - t)), 0 };
}

/* Blink period for a state, in updates. 0 means steady. */
static uint32_t state_blink_period(status_led_state_t state)
{
    switch (state) {
    case STATUS_LED_NO_NETWORK:   return LED_BLINK_FAST_PERIOD;
    case STATUS_LED_NO_SERVER:    return LED_BLINK_SLOW_PERIOD;
    case STATUS_LED_PROVISIONING: return LED_BLINK_CALM_PERIOD;
    default:                      return 0;
    }
}

static led_rgb_t state_colour(status_led_state_t state)
{
    switch (state) {
    case STATUS_LED_PROVISIONING: return (led_rgb_t){   0,   0, 255 };
    case STATUS_LED_NO_NETWORK:   return (led_rgb_t){ 255,   0,   0 };
    case STATUS_LED_NO_SERVER:    return (led_rgb_t){ 255,  90,   0 };
    case STATUS_LED_PLAYING:      return (led_rgb_t){   0, 255,   0 };
    case STATUS_LED_LOCAL_INPUT:  return (led_rgb_t){   0, 200, 200 };
    case STATUS_LED_BOOTING:
    default:                      return (led_rgb_t){  60,  60,  60 };
    }
}

static esp_err_t led_write(led_rgb_t colour, float brightness)
{
    if (s_channel == NULL || s_encoder == NULL) {
        return ESP_ERR_INVALID_STATE;
    }

    if (brightness < 0.0f) {
        brightness = 0.0f;
    } else if (brightness > 1.0f) {
        brightness = 1.0f;
    }

    /*
     * Squared, because perceived brightness is far from linear in duty
     * cycle: without it everything above a third of scale looks the same.
     */
    const float scale = brightness * brightness;

    /* WS2812 takes green first. */
    const uint8_t grb[3] = {
        (uint8_t)((float)colour.g * scale),
        (uint8_t)((float)colour.r * scale),
        (uint8_t)((float)colour.b * scale),
    };

    const rmt_transmit_config_t tx_config = { .loop_count = 0 };
    const esp_err_t err = rmt_transmit(s_channel, s_encoder, grb, sizeof(grb), &tx_config);
    if (err != ESP_OK) {
        return err;
    }
    return rmt_tx_wait_all_done(s_channel, pdMS_TO_TICKS(50));
}

/*
 * Both roles measure the frame RMS before their volume: the server in its
 * DSP stage, the client in its player before applying the stream volume.
 * The larger of the two is shown -- on a client the DSP stage sees the same
 * signal after the volume, so never more; on the server nothing is pushed.
 */
static float current_level(void)
{
    const float rms = audio_i2s_take_led_rms();

    float db = s_level_db;
    if (rms > 0.0f) {
        const float rms_db = 20.0f * log10f(rms);
        if (rms_db > db) {
            db = rms_db;
        }
    }

    const float level = (db - LED_LEVEL_FLOOR_DB) / (LED_LEVEL_CEIL_DB - LED_LEVEL_FLOOR_DB);
    if (level <= 0.0f) {
        return 0.0f;
    }
    return (level > 1.0f) ? 1.0f : level;
}

static void led_task(void *arg)
{
    (void)arg;
    float shown = 0.0f;
    uint32_t tick = 0;

    for (;;) {
        if (s_off) {
            /* Switching off: dark from here on, see status_led_off(). */
            (void)led_write((led_rgb_t){ 0, 0, 0 }, 0.0f);
            vTaskSuspend(NULL);
        }

        /* Priority as documented in status_led.h. */
        const status_led_state_t connection = s_state;
        status_led_state_t state = connection;
        const status_led_activity_t activity = s_activity;
        if (state != STATUS_LED_PROVISIONING) {
            if (activity == STATUS_LED_ACTIVITY_VOICE) {
                state = STATUS_LED_VOICE_ANNOUNCEMENT;
            } else if (activity == STATUS_LED_ACTIVITY_LOCAL_INPUT) {
                state = STATUS_LED_LOCAL_INPUT;
            }
        }
        const float level = current_level();

        /* Instant attack, gradual release -- see LED_DECAY_PER_UPDATE. */
        if (level > shown) {
            shown = level;
        } else {
            shown -= LED_DECAY_PER_UPDATE;
            if (shown < level) {
                shown = level;
            }
            if (shown < 0.0f) {
                shown = 0.0f;
            }
        }

        led_rgb_t colour;
        float brightness;

        const bool metering = (state == STATUS_LED_PLAYING ||
                               state == STATUS_LED_LOCAL_INPUT ||
                               state == STATUS_LED_VOICE_ANNOUNCEMENT);
        if (metering) {
            colour = level_colour(shown);
            brightness = LED_METER_FLOOR + shown * (1.0f - LED_METER_FLOOR);

            if (state == STATUS_LED_LOCAL_INPUT &&
                connection != STATUS_LED_PLAYING &&
                (tick % LED_LOCAL_MARK_PERIOD) < LED_LOCAL_MARK_BLANK) {
                brightness = 0.0f;
            } else if (state == STATUS_LED_VOICE_ANNOUNCEMENT &&
                       (tick % LED_VOICE_MARK_PERIOD) < LED_VOICE_MARK_BLANK) {
                brightness = 0.0f;
            }
        } else {
            /* No audio path, so no level to show: the colour is free to
             * carry the state and the rate carries its severity. */
            colour = state_colour(state);
            const uint32_t period = state_blink_period(state);
            brightness = (period == 0U || (tick % period) < (period / 2U))
                             ? 1.0f : 0.0f;
        }

        (void)led_write(colour, brightness);

        ++tick;
        vTaskDelay(pdMS_TO_TICKS(LED_UPDATE_MS));
    }
}

esp_err_t status_led_start(void)
{
    device_pins_t pins;
    device_config_get_pins(&pins);
    if (pins.status_led == 0U) {
        ESP_LOGI(TAG, "No status LED pin assigned");
        return ESP_OK;
    }

    const rmt_tx_channel_config_t channel_config = {
        .gpio_num = pins.status_led,
        .clk_src = RMT_CLK_SRC_DEFAULT,
        .resolution_hz = LED_RESOLUTION_HZ,
        .mem_block_symbols = 64,
        .trans_queue_depth = 4,
    };

    esp_err_t err = rmt_new_tx_channel(&channel_config, &s_channel);
    if (err != ESP_OK) {
        ESP_LOGE(TAG, "RMT channel on GPIO %u failed: %s",
                 (unsigned)pins.status_led, esp_err_to_name(err));
        return err;
    }

    const rmt_bytes_encoder_config_t encoder_config = {
        .bit0 = { .level0 = 1, .duration0 = LED_T0H_TICKS,
                  .level1 = 0, .duration1 = LED_T0L_TICKS },
        .bit1 = { .level0 = 1, .duration0 = LED_T1H_TICKS,
                  .level1 = 0, .duration1 = LED_T1L_TICKS },
        .flags.msb_first = 1,
    };

    err = rmt_new_bytes_encoder(&encoder_config, &s_encoder);
    if (err != ESP_OK) {
        ESP_LOGE(TAG, "RMT encoder failed: %s", esp_err_to_name(err));
        return err;
    }

    err = rmt_enable(s_channel);
    if (err != ESP_OK) {
        ESP_LOGE(TAG, "Enabling the RMT channel failed: %s", esp_err_to_name(err));
        return err;
    }

    /*
     * Self-test. This is the only way to tell from the outside whether the
     * configured GPIO is the one this board wired its LED to -- three
     * flashes, or the pin is wrong.
     */
    static const led_rgb_t probe[] = {
        { 255, 0, 0 }, { 0, 255, 0 }, { 0, 0, 255 },
    };
    for (size_t i = 0; i < sizeof(probe) / sizeof(probe[0]); ++i) {
        (void)led_write(probe[i], 1.0f);
        vTaskDelay(pdMS_TO_TICKS(120));
    }
    (void)led_write(state_colour(STATUS_LED_BOOTING), LED_METER_FLOOR);

    if (xTaskCreate(led_task, "status_led", LED_TASK_STACK, NULL,
                    LED_TASK_PRIORITY, NULL) != pdPASS) {
        ESP_LOGE(TAG, "Could not create the LED task");
        return ESP_ERR_NO_MEM;
    }

    ESP_LOGI(TAG, "Status LED ready on GPIO %u (colour = state, brightness = level)",
             (unsigned)pins.status_led);
    return ESP_OK;
}

void status_led_set_state(status_led_state_t state)
{
    s_state = state;
}

void status_led_set_activity(status_led_activity_t activity)
{
    s_activity = activity;
}

void status_led_set_level_db(float dbfs)
{
    s_level_db = dbfs;
}

void status_led_off(void)
{
    s_off = true;
    /* The task notices within one update and writes black. */
    vTaskDelay(pdMS_TO_TICKS(3 * LED_UPDATE_MS));
}

#else /* !CONFIG_SNAPSERVER_STATUS_LED_ENABLE */

esp_err_t status_led_start(void) { return ESP_OK; }
void status_led_set_state(status_led_state_t state) { (void)state; }
void status_led_set_activity(status_led_activity_t activity) { (void)activity; }
void status_led_set_level_db(float dbfs) { (void)dbfs; }
void status_led_off(void) {}

#endif
