pillepalle127/ESP32S3_Mesh_Snapserver/main/audio_sink.c

/**
 * @file audio_sink.c
 * @brief Client-role source arbitration, ring buffer, playback scheduler
 *        and player task.
 */
#include "audio_sink.h"

#include <math.h>
#include <string.h>

#include "audio_i2s.h"
#include "status_led.h"
#include "audio_resample.h"
#include "cpu_stats.h"
#include "device_config.h"
#include "esp_heap_caps.h"
#include "esp_log.h"
#include "esp_timer.h"
#include "esp_wifi.h"
#include "freertos/FreeRTOS.h"
#include "freertos/semphr.h"
#include "freertos/task.h"

static const char *TAG = "AUDIO_SINK";

#define PLAYER_TASK_STACK   8192
#define PLAYER_TASK_PRIORITY   5
#define PLAYER_TASK_CORE       1
#define SINK_STATS_TASK_STACK  4096
#define SINK_STATS_TASK_PRIORITY 2

/*
 * How long the local input must stay below the threshold before AUTO mode
 * releases it back to the network -- avoids flapping on a brief dropout or
 * on program material with quiet passages. Attack (a signal counts as
 * "present") is intentionally fast: two consecutive frames, ~40 ms.
 */
#define LOCAL_SIGNAL_RELEASE_HOLD_US (800LL * 1000LL)
#define LOCAL_SIGNAL_ATTACK_FRAMES 2

#define STATS_INTERVAL_US (5LL * 1000000LL)

/*
 * Percentage of the target fill (== buffer_ms worth of audio) that must be
 * buffered before playback switches onto the network source. Without this
 * gate the ring only ever holds a few tens of ms in practice -- playback
 * starts the instant any data arrives and drains it about as fast as it
 * fills, so the cushion meant to absorb mesh rearrangements/jitter never
 * accumulates and every minor timing hiccup is an audible underrun. Once
 * already playing from the network, transient dips below this level do not
 * re-trigger prebuffering -- only a real drop out of the network source
 * (disconnect, or local input pre-empting it) does.
 */
#define NETWORK_PREBUFFER_PERCENT 80U

/*
 * How long since the last received voice-announcement packet before the
 * arbiter releases VOICE back to whatever SOURCE_MODE would otherwise pick.
 * Comfortably above ordinary packet loss/jitter (announcement packets arrive
 * every ~10 ms) while still short enough that a dead phone/network
 * mid-announcement recovers to music about a second later -- this timeout
 * doubles as the client's entire "announcement over" signal, no explicit
 * message from the server needed. 400 ms was too short two mesh levels
 * down: gaps of that length split one announcement into pieces of 1-3 s
 * with music in between (2026-09-29). The server ends an announcement
 * after the same second of silence (VOICE_SILENCE_LIMIT_US).
 */
#define VOICE_INACTIVITY_TIMEOUT_US (1000LL * 1000LL)

/* 100 ms of room, so a burst of packets has somewhere to land; what is
 * actually kept is bounded by VOICE_MAX_FILL_SAMPLES below, which must stay
 * smaller than this or it would never take effect. */
#define VOICE_MAILBOX_CAPACITY_SAMPLES (AUDIO_SINK_FRAME_SAMPLES * 5U)
/*
 * 20 ms, one announcement packet, see render_voice_frame(). The prefill is
 * pure added latency on a path built for speed, so it stays at the minimum
 * that covers packet-to-packet jitter; the voice_underrun counter in the
 * stats line says when that is no longer enough.
 */
#define VOICE_PREFILL_SAMPLES (AUDIO_SINK_FRAME_SAMPLES)
/* Target the queue is trimmed back to once it stays above it, see
 * audio_sink_feed_voice() and audio_i2s.c for the reasoning. */
#define VOICE_TARGET_FILL_SAMPLES (AUDIO_SINK_FRAME_SAMPLES)
#define VOICE_TRIM_AFTER_FEEDS  25U

/*
 * The ring is sized well above bufferMs rather than at it: bufferMs is
 * the *steady-state* occupancy (the server timestamps a chunk at capture
 * time and the client plays it bufferMs later, so that much audio is
 * in flight permanently), not a maximum. A ring of exactly bufferMs would
 * sit at its limit continuously and drop whatever arrives while the
 * scheduler is holding playback back. Sized for the largest bufferMs a
 * server may announce, so the server's setting alone decides: 20 s of
 * mono audio, about 1.9 MB of PSRAM.
 */
#define RING_CAPACITY_FACTOR 2U
#define RING_BYTES_PER_MS    ((AUDIO_I2S_SAMPLE_RATE / 1000U) * sizeof(int16_t))

/*
 * Every chunk is checked against where the previous one ended. The usual
 * cause of a difference is the *server* correcting its own capture
 * timeline (audio_i2s.c): a slew of a few us per frame, or a re-anchor
 * (TIMESTAMP_RESYNC_THRESHOLD_US) that relabels its timestamps without
 * interrupting the audio itself. The buffered audio is kept and only its
 * labelling moves -- dropping it meant re-prebuffering 2.4 s every few
 * seconds, i.e. near-permanent silence.
 *
 * Small differences are summed up and followed in one step once the sum
 * passes this, with the rest taken out at once (SHIFT_SNAP_THRESHOLD_US).
 * Against the previous chunk's end the sum is exact, so every client steps
 * at the same chunk. Two ways that failed (2026-10-02):
 * - Measured against the ring's fill, which looks up to ~20 ms short while
 *   the player has a frame staged, only 50 ms could be told apart: each
 *   client jumped 50 ms at its own moment, up to minutes apart -- an echo.
 * - Following every slew right away left the ramp to the PI control, which
 *   lags it by an amount that depends on each client's history: 14E4 sat
 *   25 ms early next to 7788 for minutes -- an echo too.
 */
#define STREAM_DISCONTINUITY_US (5LL * 1000LL)

/*
 * Beyond this the stream is treated as a genuinely new one and the buffer
 * is dropped: no plausible capture re-anchor is this large, whereas the
 * server adopting a PC/Android client's wall clock mid-session moves its
 * timestamps by months (see handle_time() in snapserver.c). Reconnects
 * don't rely on this -- they already flush when the source leaves
 * AUDIO_SINK_SOURCE_NETWORK.
 */
#define STREAM_RESTART_US (1000LL * 1000LL)

/*
 * Above this scheduling error, correcting by resampling would take far too
 * long (200 ppm moves 200 us per second), so the timeline is realigned in
 * one step instead: skip ahead when late, hold silence when early.
 */
#define HARD_RESYNC_THRESHOLD_US (100LL * 1000LL)

/*
 * Right after the timeline followed a shift (STREAM_DISCONTINUITY_US),
 * whatever scheduling error is left beyond this is removed in one step
 * too, not by resampling. A shift used to be seen only above 100 ms, and
 * what was left of it could land just under HARD_RESYNC_THRESHOLD_US: 96 ms
 * measured on 2026-10-01, which the 200 ppm control took minutes to work off -- an
 * echo against the other speakers all that time. One short hold or skip
 * is the lesser evil.
 */
#define SHIFT_SNAP_THRESHOLD_US (1LL * 1000LL)

/*
 * An error beyond this that lasts SOFT_RESYNC_FRAMES in a row is stepped
 * out the same way, whatever caused it. Below HARD_RESYNC_THRESHOLD_US it
 * used to be left to the PI control, which pulls in ~1.5 ms per 30 s: after
 * a reconnect 7788 sat 18 ms behind the others for many minutes, an echo
 * (2026-10-02). Single frames scatter by a few ms (the TX DMA works in 5 ms
 * blocks); half a second in a row is no outlier.
 */
#define SOFT_RESYNC_THRESHOLD_US (5LL * 1000LL)
#define SOFT_RESYNC_FRAMES       25

/*
 * PI gains for the fine correction, in ppm per us of error and ppm per
 * (us * s) of accumulated error. Deliberately slow: a 10 ms error asks for
 * ~15 ppm, which is inaudible and still closes that gap in well under a
 * minute. The integral term only exists to cancel the constant crystal
 * offset between the two boards (+-20 ppm each).
 */
#define CONTROL_KP 0.0015f
#define CONTROL_KI 0.00002f
/*
 * The integral term carries whatever standing rate difference exists, so
 * it must not be the narrower of the two limits -- held at 100 ppm it
 * would cap the correction no matter how wide AUDIO_RESAMPLE_MAX_PPM was.
 * Same value as that limit.
 */
#define CONTROL_INTEGRAL_CLAMP_PPM 500.0f
/* Maximum ppm change per 20 ms frame, so corrections ramp instead of step. */
#define CONTROL_SLEW_PPM_PER_FRAME 5.0f

/* Worst-case input samples for one output frame at +AUDIO_RESAMPLE_MAX_PPM,
 * plus the interpolation lookahead and a little slack. */
#define STAGE_CAPACITY (AUDIO_SINK_FRAME_SAMPLES + 16U)

typedef struct {
    uint8_t *data;
    size_t capacity;
    size_t write_pos;
    size_t read_pos;
    size_t fill;
    SemaphoreHandle_t lock;
} byte_ring_t;

static byte_ring_t s_ring;
static bool s_started;


static volatile bool s_network_active;
static volatile uint8_t s_source_mode = SOURCE_MODE_AUTO;
static volatile int8_t s_local_threshold_db = -40;
static volatile int16_t s_delay_trim_ms;

static volatile audio_sink_source_t s_active_source = AUDIO_SINK_SOURCE_NONE;
/*
 * True once the ring has reached NETWORK_PREBUFFER_PERCENT during the
 * current network-active session, i.e. playback is allowed to (keep)
 * running from the network source without re-buffering first. Reset
 * whenever the network is no longer active, so a fresh connection
 * re-buffers from scratch instead of starting on whatever few bytes have
 * trickled in so far.
 */
static bool s_network_ready;

static bool s_local_signal_present;
static uint32_t s_local_attack_count;
static int64_t s_local_last_active_us;

/*
 * Voice-announcement mailbox: pushed by voice_announce.c's UDP receive task
 * (a separate task from this one), drained here. Deliberately not the main
 * s_ring -- this holds at most ~40 ms and is never waited on, only ever
 * drained of whatever has actually arrived, per the announcement path's
 * "drop stale audio, don't smooth it" design. s_voice_last_packet_us is also
 * what decide_source() checks, so a feed doubles as the arm signal.
 */
static portMUX_TYPE s_voice_lock = portMUX_INITIALIZER_UNLOCKED;
static int16_t s_voice_mailbox[VOICE_MAILBOX_CAPACITY_SAMPLES];
static size_t s_voice_mailbox_fill;
static volatile int64_t s_voice_last_packet_us;
/* An announcement currently overlays the output (player task's view). */
static volatile bool s_voice_on;
/* Playback from the mailbox has its prefill, see render_voice_frame(). */
static bool s_voice_primed;
/* Diagnostics for the stats line: samples zero-filled because the mailbox
 * ran dry, and samples thrown away because it overflowed. */
static uint64_t s_voice_underrun_samples;
static uint64_t s_voice_dropped_samples;
/* Consecutive feeds that found the mailbox above its target, see there. */
static uint32_t s_voice_above_target;

/* Queueing delay of the announcement in this mailbox, see feed_voice(). */
static uint32_t s_voice_wait_total_ms;
static uint32_t s_voice_wait_count;
static uint32_t s_voice_wait_max_ms;

static uint64_t s_network_bytes_fed;
static uint64_t s_network_bytes_dropped;
static uint64_t s_network_underrun_samples;
static int64_t s_last_stats_us;

/*
 * Playback timeline. s_head_ts_us is the server-clock timestamp of the
 * sample currently at the ring's read position; it is anchored from a
 * WireChunk timestamp and then advanced by exactly the number of samples
 * consumed (s_head_ts_remainder carries the sub-microsecond rest of the
 * 1e6/48000 division so this cannot drift). Guarded by the ring lock.
 */
static int64_t s_head_ts_us;
static int64_t s_head_ts_remainder;
static bool s_head_ts_valid;
/* Server timestamp where the last chunk written to the ring ended, and the
 * small differences not yet followed, see STREAM_DISCONTINUITY_US. Guarded
 * by the ring lock. */
static int64_t s_next_chunk_ts_us;
static int64_t s_pending_gap_us;

/* server_clock - local esp_timer clock, from snapclient.c's time sync. */
static volatile int64_t s_server_offset_us;
static volatile bool s_server_offset_valid;

/* From ServerSettings; defaults match the server's own seed values until
 * the real message arrives. */
static volatile int64_t s_stream_buffer_us = 3000000;
static volatile int64_t s_stream_latency_us;

/*
 * Output gain from the server's per-client volume, as a ready multiplier so
 * the hot path does no arithmetic beyond the multiply. Deliberately a
 * single value rather than a gain plus a "bypass" flag: it is written from
 * the snapclient task and read from the player task, and one variable
 * cannot be read half-updated.
 */
static volatile float s_volume_gain = 1.0f;
/* Set from ServerSettings, see audio_sink_set_announcement(). */
static volatile bool s_announcement_active;

static audio_resample_t s_resample;
static float s_control_integral;
static float s_control_ppm;
static int16_t s_stage[STAGE_CAPACITY];
static size_t s_stage_count;

/*
 * Set by the feeding task when it re-anchors the timeline; the player task
 * owns s_stage/s_resample/the PI state and clears them when it sees this,
 * so neither buffer is ever touched from two tasks at once.
 */
static volatile bool s_timeline_reset_pending;

/* Diagnostics for the periodic stats line. */
static int64_t s_last_error_us;
static uint32_t s_resync_count;
static uint64_t s_discontinuity_count;
static uint64_t s_timeline_shift_count;
/* Set by the network feed when the timeline followed a shift; the next
 * scheduled frame takes the rest at SHIFT_SNAP_THRESHOLD_US. */
static volatile bool s_shift_snap_pending;

/*
 * Loudest captured local-input frame within the current stats window,
 * recorded on every frame regardless of which source is playing. Without
 * this the local input's level is only visible once it has already won the
 * arbitration, which makes "the source delivers nothing" and "the detector
 * never triggers" impossible to tell apart.
 */
static float s_local_peak_db = -120.0f;

/*
 * Level trace for the stats line: the loudest frame of the local input and
 * of the output in each 100 ms of the current stats window, in whole dB.
 * The 5 s peak alone could not tell whether noise heard right after the
 * local input stops is still in the data or already comes out of silence.
 */
#define TRACE_BUCKET_FRAMES 5U  /* 5 x 20 ms */
#define TRACE_BUCKETS (STATS_INTERVAL_US / (TRACE_BUCKET_FRAMES * 20000LL))
static int8_t s_trace_in[TRACE_BUCKETS];
static int8_t s_trace_out[TRACE_BUCKETS];
static uint32_t s_trace_frame;

/*
 * Signs of damaged samples, per stats window: steps of more than half the
 * range from one sample to the next (music at 48 kHz practically never
 * does that; bit errors and a misaligned serial stream do all the time),
 * and samples at full scale. Counted for the local input and the output,
 * so noise that is in the data can be told from noise made after the ESP.
 */
#define JUMP_THRESHOLD 16384
static uint32_t s_jumps_in;
static uint32_t s_jumps_out;
static uint32_t s_clips_in;
static uint32_t s_clips_out;
static int16_t s_last_in;
static int16_t s_last_out;

static void count_damage(const int16_t *samples, size_t count, int16_t *last,
                         uint32_t *jumps, uint32_t *clips)
{
    int32_t prev = *last;
    for (size_t i = 0; i < count; ++i) {
        const int32_t v = samples[i];
        const int32_t step = v - prev;
        if (step > JUMP_THRESHOLD || step < -JUMP_THRESHOLD) {
            (*jumps)++;
        }
        if (v >= 32767 || v <= -32767) {
            (*clips)++;
        }
        prev = v;
    }
    *last = (int16_t)prev;
}

static int8_t trace_db(float db)
{
    return (int8_t)((db < -120.0f) ? -120 : (db > 0.0f) ? 0 : (int)lrintf(db));
}

static void trace_reset(void)
{
    memset(s_trace_in, -120, sizeof(s_trace_in));
    memset(s_trace_out, -120, sizeof(s_trace_out));
    s_trace_frame = 0;
}

/* Player task, once per frame. */
static void trace_frame(float in_db, float out_db)
{
    const uint32_t bucket = s_trace_frame / TRACE_BUCKET_FRAMES;
    if (bucket < TRACE_BUCKETS) {
        const int8_t in = trace_db(in_db);
        const int8_t out = trace_db(out_db);
        if (in > s_trace_in[bucket]) s_trace_in[bucket] = in;
        if (out > s_trace_out[bucket]) s_trace_out[bucket] = out;
    }
    s_trace_frame++;
}

static esp_err_t ring_init(byte_ring_t *ring, size_t capacity)
{
    ring->data = heap_caps_malloc(capacity, MALLOC_CAP_SPIRAM | MALLOC_CAP_8BIT);
    if (ring->data == NULL) {
        ring->data = heap_caps_malloc(capacity, MALLOC_CAP_8BIT);
    }
    if (ring->data == NULL) {
        ESP_LOGE(TAG, "No memory for %u B playback ring buffer", (unsigned)capacity);
        return ESP_ERR_NO_MEM;
    }

    ring->capacity = capacity;
    ring->write_pos = 0;
    ring->read_pos = 0;
    ring->fill = 0;
    ring->lock = xSemaphoreCreateMutex();
    if (ring->lock == NULL) {
        heap_caps_free(ring->data);
        ring->data = NULL;
        return ESP_ERR_NO_MEM;
    }

    return ESP_OK;
}

/* Returns bytes actually written; short on overflow rather than wrapping
 * over unread data. */
static size_t ring_write(byte_ring_t *ring, const uint8_t *data, size_t len)
{
    xSemaphoreTake(ring->lock, portMAX_DELAY);

    const size_t space = ring->capacity - ring->fill;
    const size_t to_write = (len < space) ? len : space;

    for (size_t i = 0; i < to_write; ++i) {
        ring->data[ring->write_pos] = data[i];
        ring->write_pos = (ring->write_pos + 1U) % ring->capacity;
    }
    ring->fill += to_write;

    xSemaphoreGive(ring->lock);
    return to_write;
}

/* Returns bytes actually read; short if the ring holds less than len. */
static size_t ring_read(byte_ring_t *ring, uint8_t *out, size_t len)
{
    xSemaphoreTake(ring->lock, portMAX_DELAY);

    const size_t to_read = (len < ring->fill) ? len : ring->fill;
    for (size_t i = 0; i < to_read; ++i) {
        out[i] = ring->data[ring->read_pos];
        ring->read_pos = (ring->read_pos + 1U) % ring->capacity;
    }
    ring->fill -= to_read;

    xSemaphoreGive(ring->lock);
    return to_read;
}

static void ring_flush(byte_ring_t *ring)
{
    xSemaphoreTake(ring->lock, portMAX_DELAY);
    ring->write_pos = 0;
    ring->read_pos = 0;
    ring->fill = 0;
    s_head_ts_valid = false;
    xSemaphoreGive(ring->lock);
}

static int64_t samples_to_us(int64_t samples)
{
    return (samples * 1000000LL) / AUDIO_I2S_SAMPLE_RATE;
}

static int64_t us_to_samples(int64_t microseconds)
{
    return (microseconds * AUDIO_I2S_SAMPLE_RATE) / 1000000LL;
}

/* Caller must hold the ring lock. */
static void timeline_advance_locked(size_t samples)
{
    const int64_t numerator =
        (int64_t)samples * 1000000LL + s_head_ts_remainder;
    s_head_ts_us += numerator / AUDIO_I2S_SAMPLE_RATE;
    s_head_ts_remainder = numerator % AUDIO_I2S_SAMPLE_RATE;
}

/* Caller must hold the ring lock. */
static void timeline_anchor_locked(int64_t chunk_ts_us)
{
    s_head_ts_us = chunk_ts_us;
    s_head_ts_remainder = 0;
    s_head_ts_valid = true;
    s_pending_gap_us = 0;
}

static float rms_dbfs(const int16_t *samples, size_t count)
{
    if (count == 0U) {
        return -120.0f;
    }

    double sum_sq = 0.0;
    for (size_t i = 0; i < count; ++i) {
        const double s = samples[i] / 32768.0;
        sum_sq += s * s;
    }

    const double rms = sqrt(sum_sq / (double)count);
    if (rms < 1e-6) {
        return -120.0f;
    }
    return (float)(20.0 * log10(rms));
}

static void update_local_signal_state(float rms_db)
{
    const int64_t now = esp_timer_get_time();

    if (rms_db >= (float)s_local_threshold_db) {
        s_local_last_active_us = now;
        if (!s_local_signal_present) {
            if (++s_local_attack_count >= LOCAL_SIGNAL_ATTACK_FRAMES) {
                s_local_signal_present = true;
                s_local_attack_count = 0;
            }
        }
        return;
    }

    s_local_attack_count = 0;
    if (s_local_signal_present &&
        (now - s_local_last_active_us) > LOCAL_SIGNAL_RELEASE_HOLD_US) {
        s_local_signal_present = false;
    }
}

/*
 * Network source, gated by NETWORK_PREBUFFER_PERCENT: once s_active_source
 * is already NETWORK this just keeps it there (no re-buffering on a
 * transient dip), otherwise it only switches in once the ring has actually
 * accumulated a real cushion. Falls back to NONE (silence) while waiting or
 * while the network isn't active at all.
 */
static audio_sink_source_t network_source_or_none(void)
{
    if (!s_network_active) {
        s_network_ready = false;
        return AUDIO_SINK_SOURCE_NONE;
    }
    if (s_active_source == AUDIO_SINK_SOURCE_NETWORK) {
        return AUDIO_SINK_SOURCE_NETWORK;
    }
    if (!s_network_ready) {
        xSemaphoreTake(s_ring.lock, portMAX_DELAY);
        const size_t fill = s_ring.fill;
        xSemaphoreGive(s_ring.lock);
        /* bufferMs worth of bytes, from the server: roughly where the
         * scheduler keeps the fill in steady state. */
        const size_t target_fill = (size_t)(s_stream_buffer_us / 1000LL) * RING_BYTES_PER_MS;
        if (fill * 100U < target_fill * NETWORK_PREBUFFER_PERCENT) {
            return AUDIO_SINK_SOURCE_NONE;
        }
        s_network_ready = true;
    }
    return AUDIO_SINK_SOURCE_NETWORK;
}

/*
 * An announcement is playing. Not a source in decide_source(): it overlays
 * whatever source is active, which keeps running underneath -- see
 * player_task. Recency of the last packet is both the arm and the disarm
 * signal, see VOICE_INACTIVITY_TIMEOUT_US.
 */
static bool voice_recent(void)
{
    return (esp_timer_get_time() - s_voice_last_packet_us) < VOICE_INACTIVITY_TIMEOUT_US;
}

static audio_sink_source_t decide_source(void)
{
    const uint8_t mode = s_source_mode;

    if (mode == SOURCE_MODE_NETWORK_ONLY) {
        return network_source_or_none();
    }
    if (mode == SOURCE_MODE_LOCAL_ONLY) {
        return AUDIO_SINK_SOURCE_LOCAL_INPUT;
    }

    /* SOURCE_MODE_AUTO: local input pre-empts the network stream whenever a
     * signal is present, same rule the ESP32_Mesh_Snapclient reference used
     * for A2DP vs. Snapcast. */
    if (s_local_signal_present) {
        return AUDIO_SINK_SOURCE_LOCAL_INPUT;
    }
    return network_source_or_none();
}

/*
 * Temporary diagnostic (2026-09-17): reports the RMS level of the samples
 * actually handed to audio_i2s_write_mono() every frame, so we can tell from
 * the log alone whether real signal is reaching the DSP/output stage on the
 * client -- as opposed to fed/dropped/underrun, which only ever prove bytes
 * moved through the ring, not that they carried audio.
 */
/*
 * What the stats line reports, snapshotted by the player task and printed by
 * sink_stats_task. The player task must not print: every line blocks it for
 * several ms on the console, and the heap, station-list and CPU queries add
 * more. Together that stalled it past the 40 ms of I2S RX buffering every
 * 5 s -- captured frames were lost, the TX side ran dry (a click) and the
 * schedule fell ~1.5 ms/s behind until a hard resync, on every client
 * (measured 2026-09-24 at -1500 ppm "I2S clock", which counts samples
 * written, not the crystal).
 */
typedef struct {
    int source;
    bool voice;
    size_t fill;
    size_t capacity;
    uint64_t fed;
    uint64_t dropped;
    uint64_t underrun;
    float output_rms_db;
    float local_peak_db;
    int threshold_db;
    bool synced;
    int64_t error_us;
    int ppm;
    uint32_t resyncs;
    uint64_t discontinuities;
    uint64_t shifts;
    uint64_t voice_underrun;
    uint64_t voice_dropped;
    uint32_t voice_wait_avg_ms;
    uint32_t voice_wait_max_ms;
    int8_t trace_in[TRACE_BUCKETS];
    int8_t trace_out[TRACE_BUCKETS];
    uint32_t jumps_in;
    uint32_t jumps_out;
    uint32_t clips_in;
    uint32_t clips_out;
} sink_stats_t;

static sink_stats_t s_stats_snapshot;
static portMUX_TYPE s_stats_lock = portMUX_INITIALIZER_UNLOCKED;
static TaskHandle_t s_stats_task;

/* Player task: cheap snapshot every STATS_INTERVAL_US, printing is elsewhere. */
static void maybe_log_stats(float output_rms_db)
{
    const int64_t now = esp_timer_get_time();
    if (s_last_stats_us == 0) {
        s_last_stats_us = now;
        return;
    }
    if ((now - s_last_stats_us) < STATS_INTERVAL_US) {
        return;
    }

    xSemaphoreTake(s_ring.lock, portMAX_DELAY);
    const size_t fill = s_ring.fill;
    const size_t capacity = s_ring.capacity;
    xSemaphoreGive(s_ring.lock);

    sink_stats_t snapshot = {
        .source = (int)s_active_source,
        .voice = s_voice_on,
        .fill = fill,
        .capacity = capacity,
        .fed = s_network_bytes_fed,
        .dropped = s_network_bytes_dropped,
        .underrun = s_network_underrun_samples,
        .output_rms_db = output_rms_db,
        .local_peak_db = s_local_peak_db,
        .threshold_db = (int)s_local_threshold_db,
        .synced = s_server_offset_valid,
        .error_us = s_last_error_us,
        .ppm = (int)audio_resample_get_ppm(&s_resample),
        .resyncs = s_resync_count,
        .discontinuities = s_discontinuity_count,
        .shifts = s_timeline_shift_count,
        .voice_underrun = s_voice_underrun_samples,
        .voice_dropped = s_voice_dropped_samples,
        .voice_wait_avg_ms = (s_voice_wait_count != 0U)
                                 ? (s_voice_wait_total_ms / s_voice_wait_count) : 0U,
        .voice_wait_max_ms = s_voice_wait_max_ms,
    };
    snapshot.jumps_in = s_jumps_in;
    snapshot.jumps_out = s_jumps_out;
    snapshot.clips_in = s_clips_in;
    snapshot.clips_out = s_clips_out;
    s_jumps_in = 0;
    s_jumps_out = 0;
    s_clips_in = 0;
    s_clips_out = 0;
    memcpy(snapshot.trace_in, s_trace_in, sizeof(s_trace_in));
    memcpy(snapshot.trace_out, s_trace_out, sizeof(s_trace_out));
    trace_reset();
    portENTER_CRITICAL(&s_stats_lock);
    s_stats_snapshot = snapshot;
    portEXIT_CRITICAL(&s_stats_lock);
    if (s_stats_task != NULL) {
        xTaskNotifyGive(s_stats_task);
    }

    s_voice_underrun_samples = 0;
    s_voice_dropped_samples = 0;
    s_voice_wait_total_ms = 0;
    s_voice_wait_count = 0;
    s_voice_wait_max_ms = 0;
    s_network_bytes_fed = 0;
    s_network_bytes_dropped = 0;
    s_network_underrun_samples = 0;
    s_local_peak_db = -120.0f;
    s_last_stats_us = now;
}

/* Low priority, core 0: prints what the player task snapshotted. */
static void sink_stats_task(void *arg)
{
    (void)arg;
    for (;;) {
        ulTaskNotifyTake(pdTRUE, portMAX_DELAY);

        sink_stats_t st;
        portENTER_CRITICAL(&s_stats_lock);
        st = s_stats_snapshot;
        portEXIT_CRITICAL(&s_stats_lock);

        ESP_LOGI(TAG,
                 "src=%d%s ring=%u/%u B fed=%llu B dropped=%llu B underrun=%llu samples "
                 "output_rms=%.1f dBFS local_peak=%.1f dBFS(thr %d) sync=%s err=%lld us "
                 "ppm=%d resync=%lu disc=%llu shift=%llu voice_underrun=%llu voice_dropped=%llu "
                 "voice_wait=%lu/%lu ms",
                 st.source, st.voice ? "+voice" : "",
                 (unsigned)st.fill, (unsigned)st.capacity,
                 (unsigned long long)st.fed, (unsigned long long)st.dropped,
                 (unsigned long long)st.underrun,
                 (double)st.output_rms_db, (double)st.local_peak_db, st.threshold_db,
                 st.synced ? "yes" : "no", (long long)st.error_us, st.ppm,
                 (unsigned long)st.resyncs, (unsigned long long)st.discontinuities,
                 (unsigned long long)st.shifts, (unsigned long long)st.voice_underrun,
                 (unsigned long long)st.voice_dropped,
                 (unsigned long)st.voice_wait_avg_ms, (unsigned long)st.voice_wait_max_ms);

        /* Only when something was not digital silence, to keep quiet logs quiet. */
        bool any = false;
        for (size_t i = 0; i < TRACE_BUCKETS; ++i) {
            any = any || st.trace_in[i] > -120 || st.trace_out[i] > -120;
        }
        if (any) {
            char in_line[TRACE_BUCKETS * 5 + 1];
            char out_line[TRACE_BUCKETS * 5 + 1];
            size_t in_len = 0;
            size_t out_len = 0;
            for (size_t i = 0; i < TRACE_BUCKETS; ++i) {
                in_len += snprintf(in_line + in_len, sizeof(in_line) - in_len, " %d", st.trace_in[i]);
                out_len += snprintf(out_line + out_len, sizeof(out_line) - out_len, " %d", st.trace_out[i]);
            }
            ESP_LOGI(TAG, "damage: jumps in=%lu out=%lu, full scale in=%lu out=%lu",
                     (unsigned long)st.jumps_in, (unsigned long)st.jumps_out,
                     (unsigned long)st.clips_in, (unsigned long)st.clips_out);
            ESP_LOGI(TAG, "trace in  (max frame RMS dBFS per 100 ms):%s", in_line);
            ESP_LOGI(TAG, "trace out (max frame RMS dBFS per 100 ms):%s", out_line);
        }

        /*
         * Peak after the crossover, i.e. what actually reaches the two DAC
         * channels. output_rms above is measured before it, so a signal
         * that disappears in the DSP stage -- a channel gain turned down, a
         * misconfigured split -- looks identical there. Same measurement
         * the server prints.
         */
        int16_t dsp_left = 0;
        int16_t dsp_right = 0;
        audio_i2s_take_output_peak(&dsp_left, &dsp_right);
        ESP_LOGI(TAG, "DSP output peak: left=%d right=%d (of 32767), I2S clock %+ld ppm",
                 (int)dsp_left, (int)dsp_right, (long)audio_i2s_clock_ppm());
        uint32_t tx_dry = 0;
        uint32_t rx_lost = 0;
        audio_i2s_take_dma_stats(&tx_dry, &rx_lost);
        if (tx_dry != 0U || rx_lost != 0U) {
            ESP_LOGW(TAG, "I2S DMA: TX ran dry %lu x, RX overflowed %lu x (%u ms each)",
                     (unsigned long)tx_dry, (unsigned long)rx_lost,
                     (unsigned)(AUDIO_I2S_DMA_FRAME_NUM * 1000U / AUDIO_I2S_SAMPLE_RATE));
        }
        uint32_t limited = 0;
        float limit_db = 0.0f;
        audio_i2s_take_limiter_stats(&limited, &limit_db);
        if (limited != 0U) {
            ESP_LOGW(TAG, "Output limiter: %lu samples, max -%.1f dB", (unsigned long)limited, (double)limit_db);
        }
        const float comp_db = audio_i2s_take_comp_stats();
        if (comp_db >= 0.1f) {
            ESP_LOGI(TAG, "Compressor: max -%.1f dB", (double)comp_db);
        }

        /*
         * Same format as the server's heap line. A client is also a mesh
         * relay, and a relay carrying several children has twice hung
         * completely (2026-09-19, WLAN stack unresponsive, no log) --
         * internal RAM is the suspect, so every client reports it together
         * with how many stations it currently carries.
         */
        wifi_sta_list_t stations = {0};
        const int children = (esp_wifi_ap_get_sta_list(&stations) == ESP_OK) ? stations.num : -1;
        ESP_LOGI(TAG, "heap: internal free=%u B largest=%u B min_ever=%u B children=%d",
                 (unsigned)heap_caps_get_free_size(MALLOC_CAP_INTERNAL),
                 (unsigned)heap_caps_get_largest_free_block(MALLOC_CAP_INTERNAL),
                 (unsigned)heap_caps_get_minimum_free_size(MALLOC_CAP_INTERNAL),
                 children);
        cpu_stats_log(TAG, 2);
    }
}

/*
 * Scheduling error of the sample at the head of the playback timeline:
 * positive means it is due later than it would actually be heard (too
 * early, hold), negative means it is overdue (too late, catch up).
 * Returns false while there is nothing to schedule against -- no clock
 * sync yet, or no anchored stream -- in which case the caller just plays
 * the ring buffer out at nominal rate without scheduling.
 */
static bool scheduling_error_us(int64_t *error_us)
{
    if (!s_server_offset_valid) {
        return false;
    }

    xSemaphoreTake(s_ring.lock, portMAX_DELAY);
    const bool anchored = s_head_ts_valid;
    const int64_t due_local_us = (s_head_ts_us - s_server_offset_us) +
                                 s_stream_buffer_us - s_stream_latency_us +
                                 (int64_t)s_delay_trim_ms * 1000LL;
    xSemaphoreGive(s_ring.lock);

    if (!anchored) {
        return false;
    }

    *error_us = due_local_us - (esp_timer_get_time() + AUDIO_I2S_TX_LATENCY_US);
    return true;
}

/*
 * Full restart of the playback pipeline: drops the staged samples and the
 * resampler phase along with the controller. Only for real discontinuities
 * (new stream, hard resync, source change) -- doing this per frame would
 * throw away the staging remainder every time and swallow a sample.
 */
static void control_reset(void)
{
    audio_resample_init(&s_resample);
    s_control_integral = 0.0f;
    s_control_ppm = 0.0f;
    s_stage_count = 0;
}

/*
 * Stops correcting without disturbing the stream: used while there is
 * nothing to schedule against, where playback should simply pass through
 * at nominal rate.
 */
static void control_neutral(void)
{
    s_control_integral = 0.0f;
    s_control_ppm = 0.0f;
    audio_resample_set_ppm(&s_resample, 0);
}

/*
 * Late by -error_us: discard that much audio in one step instead of
 * waiting for a 200 ppm correction to eat it. The samples already staged
 * in front of the ring go with it, so they have to move the timeline too.
 */
static void timeline_resync_late(int64_t error_us)
{
    const size_t staged = s_stage_count;
    const size_t wanted = (size_t)us_to_samples(-error_us);

    xSemaphoreTake(s_ring.lock, portMAX_DELAY);
    const size_t available = s_ring.fill / sizeof(int16_t);
    const size_t skipped = (wanted < available) ? wanted : available;
    s_ring.read_pos = (s_ring.read_pos + skipped * sizeof(int16_t)) % s_ring.capacity;
    s_ring.fill -= skipped * sizeof(int16_t);
    timeline_advance_locked(staged + skipped);
    xSemaphoreGive(s_ring.lock);

    /*
     * The staging and resampler phase go, the controller's state stays: its
     * integral is this crystal's rate against the server's, which a skip
     * does not change. Clearing it let the client drift at that rate until
     * the integral was rebuilt minutes later -- 30-40 ms off after every
     * small skip (2026-10-02).
     */
    const float integral = s_control_integral;
    const float ppm = s_control_ppm;
    control_reset();
    s_control_integral = integral;
    s_control_ppm = ppm;
    audio_resample_set_ppm(&s_resample, (int32_t)ppm);
}

/*
 * PI correction inside the fine-control band. The output drives the
 * resampler ratio: playing slightly fast (positive ppm) eats the backlog
 * when late, slightly slow stretches it when early.
 */
static void control_update(int64_t error_us)
{
    const float error = (float)error_us;
    const float frame_seconds =
        (float)AUDIO_SINK_FRAME_SAMPLES / (float)AUDIO_I2S_SAMPLE_RATE;

    s_control_integral += error * frame_seconds;

    const float integral_limit = CONTROL_INTEGRAL_CLAMP_PPM / CONTROL_KI;
    if (s_control_integral > integral_limit) {
        s_control_integral = integral_limit;
    } else if (s_control_integral < -integral_limit) {
        s_control_integral = -integral_limit;
    }

    float target_ppm = -(CONTROL_KP * error + CONTROL_KI * s_control_integral);
    if (target_ppm > (float)AUDIO_RESAMPLE_MAX_PPM) {
        target_ppm = (float)AUDIO_RESAMPLE_MAX_PPM;
    } else if (target_ppm < -(float)AUDIO_RESAMPLE_MAX_PPM) {
        target_ppm = -(float)AUDIO_RESAMPLE_MAX_PPM;
    }

    const float delta = target_ppm - s_control_ppm;
    if (delta > CONTROL_SLEW_PPM_PER_FRAME) {
        s_control_ppm += CONTROL_SLEW_PPM_PER_FRAME;
    } else if (delta < -CONTROL_SLEW_PPM_PER_FRAME) {
        s_control_ppm -= CONTROL_SLEW_PPM_PER_FRAME;
    } else {
        s_control_ppm = target_ppm;
    }

    audio_resample_set_ppm(&s_resample, (int32_t)s_control_ppm);
}

/*
 * Produces one output frame from the network stream: applies the
 * scheduler, then pulls the (resampling-dependent) number of input samples
 * through the staging buffer. Returns false when the frame should be
 * silence instead -- either because the head sample is not due yet or
 * because nothing is buffered.
 */
static bool render_network_frame(int16_t *playout_mono)
{
    if (s_timeline_reset_pending) {
        s_timeline_reset_pending = false;
        control_reset();
    }

    int64_t error_us = 0;
    static bool holding;
    size_t silent = 0; /* samples of silence in front of the stream */

    if (scheduling_error_us(&error_us)) {
        s_last_error_us = error_us;

        /*
         * Too early: emit silence and keep everything buffered. Each held
         * frame costs 20 ms of real time, so the schedule catches up on its
         * own without discarding audio.
         *
         * Entering and leaving this state use different thresholds on
         * purpose. Releasing at HARD_RESYNC_THRESHOLD_US would hand the
         * fine controller a residual error of a full threshold width, and
         * at 200 ppm it needs ~400 s to work off 80 ms -- measured on
         * device: err sat at 72-100 ms while ppm pinned at its -200 limit.
         * Holding until the error is actually gone starts playback on time
         * and leaves the controller nothing but real crystal drift to do.
         */
        /* Just after a shift, or after SOFT_RESYNC_FRAMES off by more than
         * SOFT_RESYNC_THRESHOLD_US, the step threshold is
         * SHIFT_SNAP_THRESHOLD_US. */
        static int off_frames;
        bool snap = s_shift_snap_pending;
        s_shift_snap_pending = false;
        if (error_us > SOFT_RESYNC_THRESHOLD_US || error_us < -SOFT_RESYNC_THRESHOLD_US) {
            if (++off_frames >= SOFT_RESYNC_FRAMES) {
                snap = true;
            }
        } else {
            off_frames = 0;
        }
        if (snap) {
            off_frames = 0;
        }
        const int64_t step_us = snap ? SHIFT_SNAP_THRESHOLD_US : HARD_RESYNC_THRESHOLD_US;

        if (error_us > step_us || (holding && error_us > 0)) {
            if (!holding) {
                s_resync_count++;
            }
            /*
             * Whole frames of silence while more than one is left, then
             * exactly the rest in front of the stream. Holding in whole
             * frames overshot by up to 20 ms, a different amount on every
             * client, which the PI control then took minutes to work off:
             * the speakers 10-15 ms apart after every shift (2026-10-02).
             */
            const int64_t frame_us = samples_to_us(AUDIO_SINK_FRAME_SAMPLES);
            if (error_us >= frame_us) {
                holding = true;
                return false;
            }
            silent = (size_t)us_to_samples(error_us);
        } else if (error_us < -step_us) {
            timeline_resync_late(error_us);
            s_resync_count++;
        } else {
            control_update(error_us);
        }
        holding = false;
    } else {
        holding = false;
        control_neutral();
    }

    const size_t out_samples = AUDIO_SINK_FRAME_SAMPLES - silent;
    memset(playout_mono, 0, silent * sizeof(int16_t));

    const size_t needed =
        audio_resample_input_needed(&s_resample, out_samples);
    if (needed > STAGE_CAPACITY) {
        return false;
    }

    if (s_stage_count < needed) {
        const size_t want = needed - s_stage_count;
        const size_t got_bytes = ring_read(&s_ring,
                                           (uint8_t *)(s_stage + s_stage_count),
                                           want * sizeof(int16_t));
        const size_t got = got_bytes / sizeof(int16_t);
        s_stage_count += got;

        if (s_stage_count < needed) {
            const size_t missing = needed - s_stage_count;
            memset(s_stage + s_stage_count, 0, missing * sizeof(int16_t));
            s_network_underrun_samples += missing;
            s_stage_count = needed;
        }
    }

    const size_t consumed =
        audio_resample_process(&s_resample, s_stage, playout_mono + silent, out_samples);

    /*
     * The timeline follows what actually leaves the resampler, not what is
     * pulled out of the ring: the staging buffer sits in front of the ring,
     * so anchoring on ring reads would make the head jump a whole frame
     * ahead every time staging is refilled.
     */
    xSemaphoreTake(s_ring.lock, portMAX_DELAY);
    timeline_advance_locked(consumed);
    xSemaphoreGive(s_ring.lock);

    if (consumed < s_stage_count) {
        memmove(s_stage, s_stage + consumed, (s_stage_count - consumed) * sizeof(int16_t));
        s_stage_count -= consumed;
    } else {
        s_stage_count = 0;
    }

    return true;
}

/*
 * Drains up to AUDIO_SINK_FRAME_SAMPLES from the voice mailbox into out,
 * zero-filling anything not yet received. Mirrors
 * audio_i2s.c's assemble_voice_frame() for the server's own local speaker --
 * kept as a separate, small implementation here rather than shared, since
 * the two run in different roles and the whole function is a few lines.
 */
static void render_voice_frame(int16_t *out)
{
    size_t take = 0;

    portENTER_CRITICAL(&s_voice_lock);
    /*
     * Prefill: announcement packets are 20 ms, the same as this task's
     * tick, so without any cushion every bit of Wi-Fi jitter lands a packet
     * just after the tick and leaves a hole. Playback therefore only starts
     * (and restarts after running dry) once VOICE_PREFILL_SAMPLES are in --
     * a fixed, small delay instead of a stream of small dropouts.
     */
    if (!s_voice_primed && s_voice_mailbox_fill >= VOICE_PREFILL_SAMPLES) {
        s_voice_primed = true;
    }
    if (s_voice_primed) {
        take = (s_voice_mailbox_fill < AUDIO_SINK_FRAME_SAMPLES)
                   ? s_voice_mailbox_fill : AUDIO_SINK_FRAME_SAMPLES;
        memcpy(out, s_voice_mailbox, take * sizeof(int16_t));
        if (take < s_voice_mailbox_fill) {
            memmove(s_voice_mailbox, s_voice_mailbox + take,
                   (s_voice_mailbox_fill - take) * sizeof(int16_t));
        }
        s_voice_mailbox_fill -= take;
        if (take < AUDIO_SINK_FRAME_SAMPLES) {
            s_voice_primed = false;
            s_voice_underrun_samples += AUDIO_SINK_FRAME_SAMPLES - take;
        }
    }
    portEXIT_CRITICAL(&s_voice_lock);

    if (take < AUDIO_SINK_FRAME_SAMPLES) {
        memset(out + take, 0, (AUDIO_SINK_FRAME_SAMPLES - take) * sizeof(int16_t));
    }
}

static void player_task(void *arg)
{
    (void)arg;

    int16_t local_mono[AUDIO_SINK_FRAME_SAMPLES];
    int16_t playout_mono[AUDIO_SINK_FRAME_SAMPLES];

    for (;;) {
        const esp_err_t capture_result =
            audio_i2s_capture_mono(local_mono, AUDIO_SINK_FRAME_SAMPLES);
        const bool have_local = (capture_result == ESP_OK);

        const float local_db = have_local
                                   ? rms_dbfs(local_mono, AUDIO_SINK_FRAME_SAMPLES)
                                   : -120.0f;
        if (local_db > s_local_peak_db) {
            s_local_peak_db = local_db;
        }
        update_local_signal_state(local_db);
        if (have_local) {
            count_damage(local_mono, AUDIO_SINK_FRAME_SAMPLES, &s_last_in,
                         &s_jumps_in, &s_clips_in);
        }

        const bool voice = voice_recent();

        const audio_sink_source_t desired = decide_source();
        if (desired != s_active_source) {
            ESP_LOGI(TAG, "Switching source %d -> %d", (int)s_active_source, (int)desired);
            /*
             * Flush only when the network source is lost (NETWORK -> NONE):
             * the connection is gone and what is queued is stale. Handing
             * over to the local input does not flush -- the stream keeps
             * playing silently underneath (see below), so switching back
             * finds exactly the audio that is due and carries on without a
             * gap. Flushing there, as this first did, cost a full bufferMs
             * of silence (~3 s, measured) plus a hard resync on every return
             * from the local input. Never flush when *entering* the network
             * source either: that ring content is the prebuffer
             * network_source_or_none() just required.
             */
            if (s_active_source == AUDIO_SINK_SOURCE_NETWORK &&
                desired == AUDIO_SINK_SOURCE_NONE) {
                ring_flush(&s_ring);
                control_reset();
            }
            s_active_source = desired;
        }

        if (voice != s_voice_on) {
            ESP_LOGI(TAG, "Announcement %s", voice ? "started" : "ended");
            s_voice_on = voice;
            audio_i2s_set_announcement_output(voice);
            /* Every announcement starts with an empty mailbox and a fresh
             * prefill, never with a leftover tail of the previous one. */
            portENTER_CRITICAL(&s_voice_lock);
            s_voice_mailbox_fill = 0;
            s_voice_primed = false;
            portEXIT_CRITICAL(&s_voice_lock);
        }
        /* The connection state is snapclient.c's; this only says what
         * plays on top of it, and wins over it (see status_led.h). */
        status_led_set_activity(voice ? STATUS_LED_ACTIVITY_VOICE
                                : (s_active_source == AUDIO_SINK_SOURCE_LOCAL_INPUT)
                                      ? STATUS_LED_ACTIVITY_LOCAL_INPUT
                                      : STATUS_LED_ACTIVITY_NONE);

        const int16_t *chosen;
        if (s_active_source == AUDIO_SINK_SOURCE_LOCAL_INPUT && have_local) {
            chosen = local_mono;
            /*
             * The network stream keeps running underneath, exactly as for
             * an announcement: rendered on schedule and thrown away, so the
             * ring drains at its normal rate and the timeline and drift
             * control stay locked. playout_mono is free here; the volume
             * step below overwrites it from local_mono.
             */
            if (network_source_or_none() == AUDIO_SINK_SOURCE_NETWORK) {
                (void)render_network_frame(playout_mono);
            }
        } else if (s_active_source == AUDIO_SINK_SOURCE_NETWORK) {
            if (!render_network_frame(playout_mono)) {
                memset(playout_mono, 0, sizeof(playout_mono));
            }
            chosen = playout_mono;
        } else {
            memset(playout_mono, 0, sizeof(playout_mono));
            chosen = playout_mono;
        }

        /*
         * An announcement replaces the output but not the source: the music
         * frame above was rendered as usual and is simply not played -- the
         * same thing a muted client does. The ring keeps draining at its
         * normal rate, the timeline and the drift control keep running, and
         * when the announcement ends playback carries on exactly where a
         * muted level-2 client is, with nothing to rebuffer. Stopping the
         * music instead, as this first did, let the ring overflow after
         * ~buffer_ms and forced a flush and a fresh prebuffer.
         *
         * local_mono is free to hold the announcement: the local-input level
         * was measured above, and the local input isn't played while an
         * announcement covers it.
         */
        if (voice) {
            render_voice_frame(local_mono);
            chosen = local_mono;
        } else if (s_announcement_active) {
            /*
             * An announcement runs somewhere in the mesh but not here --
             * either it is not relayed this far, or its packets have not
             * arrived yet. Music in the same room would clash with it, so
             * this speaker stays silent. The frame above was still
             * rendered, exactly as for a muted client: the ring keeps
             * draining, the timeline and the drift control keep running,
             * and playback resumes seamlessly afterwards.
             */
            memset(local_mono, 0, AUDIO_SINK_FRAME_SAMPLES * sizeof(local_mono[0]));
            chosen = local_mono;
        }

        /*
         * Volume last, after the source has been chosen: applying it
         * earlier would bake the level into the ring buffer, and a change
         * would only become audible buffer_ms later. Writing into
         * playout_mono is safe for either source -- it is this task's own
         * buffer, and in the local-input case it is otherwise unused.
         */
        /* The LED shows the signal, not the speaker: measured before the
         * volume, so it keeps moving at any volume setting. */
        status_led_set_level_db(rms_dbfs(chosen, AUDIO_SINK_FRAME_SAMPLES));

        const float gain = s_volume_gain;
        if (gain < 1.0f) {
            /* Attenuation only -- the mapping below never exceeds 1.0, so
             * the result cannot leave int16 range and needs no clipping. */
            for (size_t i = 0; i < AUDIO_SINK_FRAME_SAMPLES; ++i) {
                playout_mono[i] = (int16_t)lrintf((float)chosen[i] * gain);
            }
            chosen = playout_mono;
        }

        audio_i2s_write_mono(chosen, AUDIO_SINK_FRAME_SAMPLES);
        const float frame_rms_db = rms_dbfs(chosen, AUDIO_SINK_FRAME_SAMPLES);
        trace_frame(local_db, frame_rms_db);
        count_damage(chosen, AUDIO_SINK_FRAME_SAMPLES, &s_last_out,
                     &s_jumps_out, &s_clips_out);
        maybe_log_stats(frame_rms_db);
    }
}

esp_err_t audio_sink_start(void)
{
    if (s_started) {
        return ESP_OK;
    }

    const size_t capacity = (size_t)DEVICE_CONFIG_BUFFER_MAX_MS * RING_BYTES_PER_MS * RING_CAPACITY_FACTOR;

    esp_err_t result = ring_init(&s_ring, capacity);
    if (result != ESP_OK) {
        return result;
    }

    s_active_source = AUDIO_SINK_SOURCE_NONE;
    s_local_signal_present = false;
    s_local_attack_count = 0;
    s_local_last_active_us = 0;
    control_reset();

    trace_reset();

    /* Not fatal: without it there are just no stats lines. */
    if (xTaskCreatePinnedToCore(sink_stats_task, "sink_stats", SINK_STATS_TASK_STACK, NULL,
                                SINK_STATS_TASK_PRIORITY, &s_stats_task, 0) != pdPASS) {
        s_stats_task = NULL;
        ESP_LOGW(TAG, "No stats task, running without stats lines");
    }

    if (xTaskCreatePinnedToCore(player_task,
                                "audio_sink",
                                PLAYER_TASK_STACK,
                                NULL,
                                PLAYER_TASK_PRIORITY,
                                NULL,
                                PLAYER_TASK_CORE) != pdPASS) {
        ESP_LOGE(TAG, "Creating player task failed");
        heap_caps_free(s_ring.data);
        s_ring.data = NULL;
        return ESP_ERR_NO_MEM;
    }

    s_started = true;
    ESP_LOGI(TAG, "Playback ring buffer ready: %u B, bufferMs from the server",
             (unsigned)capacity);
    return ESP_OK;
}

void audio_sink_set_network_active(bool active)
{
    s_network_active = active;
}

void audio_sink_feed_voice(const int16_t *mono, size_t mono_samples)
{
    if (!s_started || mono == NULL || mono_samples == 0U) {
        return;
    }

    if (mono_samples > VOICE_MAILBOX_CAPACITY_SAMPLES) {
        mono += mono_samples - VOICE_MAILBOX_CAPACITY_SAMPLES;
        mono_samples = VOICE_MAILBOX_CAPACITY_SAMPLES;
    }

    portENTER_CRITICAL(&s_voice_lock);
    /* Queueing delay of this audio: what is already in the mailbox plays
     * first. See audio_i2s_feed_voice(), same measurement on the server. */
    const uint32_t wait_ms =
        (uint32_t)(s_voice_mailbox_fill * 1000U / AUDIO_I2S_SAMPLE_RATE);
    s_voice_wait_total_ms += wait_ms;
    ++s_voice_wait_count;
    if (wait_ms > s_voice_wait_max_ms) {
        s_voice_wait_max_ms = wait_ms;
    }

    /* Full: drop the oldest samples, see audio_i2s_feed_voice(). */
    if (s_voice_mailbox_fill + mono_samples > VOICE_MAILBOX_CAPACITY_SAMPLES) {
        const size_t drop =
            s_voice_mailbox_fill + mono_samples - VOICE_MAILBOX_CAPACITY_SAMPLES;
        memmove(s_voice_mailbox, s_voice_mailbox + drop,
                (s_voice_mailbox_fill - drop) * sizeof(int16_t));
        s_voice_mailbox_fill -= drop;
        s_voice_dropped_samples += drop;
    }
    memcpy(s_voice_mailbox + s_voice_mailbox_fill, mono, mono_samples * sizeof(int16_t));
    s_voice_mailbox_fill += mono_samples;

    /* Cut back a backlog that survives, not a single burst -- same rule and
     * the same reasoning as audio_i2s_feed_voice(). */
    if (s_voice_mailbox_fill > VOICE_TARGET_FILL_SAMPLES) {
        ++s_voice_above_target;
    } else {
        s_voice_above_target = 0;
    }
    if (s_voice_above_target >= VOICE_TRIM_AFTER_FEEDS) {
        const size_t drop = s_voice_mailbox_fill - VOICE_TARGET_FILL_SAMPLES;
        memmove(s_voice_mailbox, s_voice_mailbox + drop,
                (s_voice_mailbox_fill - drop) * sizeof(int16_t));
        s_voice_mailbox_fill -= drop;
        s_voice_dropped_samples += drop;
        s_voice_above_target = 0;
    }
    portEXIT_CRITICAL(&s_voice_lock);

    /* Outside the critical section: only decide_source() reads this, and a
     * stale read by a few microseconds is harmless against a 400 ms window. */
    s_voice_last_packet_us = esp_timer_get_time();
}

size_t audio_sink_feed_network(const int16_t *mono_pcm,
                               size_t sample_count,
                               int64_t chunk_ts_us)
{
    /*
     * Accepted whatever source is playing: while prebuffering (the ring must
     * fill), while playing, and while the local input covers it -- the
     * stream then runs silently underneath (see player_task), so switching
     * back to it is seamless instead of starting over from an empty ring.
     */
    if (!s_started) {
        s_network_bytes_dropped += sample_count * sizeof(int16_t);
        return 0;
    }

    /*
     * Anchor or re-anchor the playback timeline before the data lands.
     * Only this task ever writes to the ring, so releasing the lock between
     * the check and the ring_write() below cannot let another writer slip
     * in and invalidate the decision.
     */
    xSemaphoreTake(s_ring.lock, portMAX_DELAY);
    if (!s_head_ts_valid || s_ring.fill == 0U) {
        timeline_anchor_locked(chunk_ts_us);
    } else {
        const int64_t gap_us = chunk_ts_us - s_next_chunk_ts_us;
        if (gap_us > STREAM_RESTART_US || gap_us < -STREAM_RESTART_US) {
            s_ring.write_pos = 0;
            s_ring.read_pos = 0;
            s_ring.fill = 0;
            timeline_anchor_locked(chunk_ts_us);
            s_network_ready = false; /* rebuild the prebuffer from scratch */
            s_timeline_reset_pending = true;
            s_shift_snap_pending = false;
            s_discontinuity_count++;
        } else {
            s_pending_gap_us += gap_us;
            if (s_pending_gap_us > STREAM_DISCONTINUITY_US ||
                s_pending_gap_us < -STREAM_DISCONTINUITY_US) {
                /*
                 * Follow the shift and keep everything buffered: the audio
                 * is still continuous, only its labelling moved.
                 */
                s_head_ts_us += s_pending_gap_us;
                s_pending_gap_us = 0;
                s_timeline_shift_count++;
                s_shift_snap_pending = true;
            }
        }
    }
    xSemaphoreGive(s_ring.lock);

    const size_t written =
        ring_write(&s_ring, (const uint8_t *)mono_pcm, sample_count * sizeof(int16_t));

    /* Whatever did not fit shows up as a gap in front of the next chunk. */
    xSemaphoreTake(s_ring.lock, portMAX_DELAY);
    s_next_chunk_ts_us = chunk_ts_us + samples_to_us((int64_t)(written / sizeof(int16_t)));
    xSemaphoreGive(s_ring.lock);

    s_network_bytes_fed += written;
    if (written < sample_count * sizeof(int16_t)) {
        s_network_bytes_dropped += (sample_count * sizeof(int16_t)) - written;
    }
    return written / sizeof(int16_t);
}

void audio_sink_set_server_time_offset(int64_t offset_us, bool valid)
{
    s_server_offset_us = offset_us;
    s_server_offset_valid = valid;
}

void audio_sink_set_stream_timing(uint32_t buffer_ms, int32_t latency_ms)
{
    const int64_t buffer_us = (int64_t)buffer_ms * 1000LL;
    const int64_t latency_us = (int64_t)latency_ms * 1000LL;
    /*
     * A new latency or buffer moves the schedule; take it in one step like
     * a shift (SHIFT_SNAP_THRESHOLD_US). Below HARD_RESYNC_THRESHOLD_US it
     * was left to the PI control, which needed minutes for 55 ms -- no way
     * to set a speaker's delay by ear (2026-10-02). ServerSettings also
     * arrive for every volume change, so only an actual change counts.
     */
    if (buffer_us != s_stream_buffer_us || latency_us != s_stream_latency_us) {
        s_stream_buffer_us = buffer_us;
        s_stream_latency_us = latency_us;
        s_shift_snap_pending = true;
    }
}

void audio_sink_set_volume(int32_t percent, bool muted)
{
    if (percent < 0) {
        percent = 0;
    } else if (percent > 100) {
        percent = 100;
    }

    /*
     * Cubic mapping rather than a straight percentage: a linear amplitude
     * scale crowds almost the whole audible range into the top of the
     * control, so half volume would barely sound quieter. The exponent is
     * the usual cheap approximation of perceived loudness and is easy to
     * swap if it turns out too steep in practice.
     */
    const float fraction = (float)percent / 100.0f;
    const float gain = muted ? 0.0f : (fraction * fraction * fraction);

    s_volume_gain = gain;

    ESP_LOGI(TAG, "Volume now %ld%%%s (gain %.3f)",
             (long)percent, muted ? " (muted)" : "", (double)gain);
}

void audio_sink_set_announcement(bool active)
{
    if (s_announcement_active == active) {
        return;
    }
    s_announcement_active = active;
    ESP_LOGI(TAG, "Announcement %s: music stays silent%s",
             active ? "started" : "ended",
             active ? " until it ends" : ", playback resumes");
}

void audio_sink_set_source_mode(uint8_t mode)
{
    s_source_mode = mode;
}

void audio_sink_set_local_input_threshold_db(int8_t threshold_db)
{
    s_local_threshold_db = threshold_db;
}

void audio_sink_set_delay_trim_ms(int16_t delay_trim_ms)
{
    if (delay_trim_ms != s_delay_trim_ms) {
        s_delay_trim_ms = delay_trim_ms;
        s_shift_snap_pending = true; /* see audio_sink_set_stream_timing() */
    }
}

void audio_sink_apply_delay_trim(uint8_t role, uint16_t buffer_ms, int16_t trim_ms)
{
    if (role != DEVICE_ROLE_SERVER) {
        audio_sink_set_delay_trim_ms(trim_ms);
        return;
    }

    /*
     * Server: its own speaker sits behind a delay line of buffer_ms, the
     * same bufferMs every client schedules against, and the trim nudges
     * that. The line was allocated at start for the full trim range, so
     * this only moves the read position.
     */
    const int32_t local_delay_ms = (int32_t)buffer_ms + trim_ms;
    audio_i2s_set_output_delay(
        (uint32_t)(local_delay_ms > 0 ? local_delay_ms : 0),
        (uint32_t)buffer_ms + DEVICE_CONFIG_DELAY_TRIM_MAX_MS);
}

audio_sink_source_t audio_sink_current_source(void)
{
    return s_voice_on ? AUDIO_SINK_SOURCE_VOICE : s_active_source;
}
