pillepalle127/ESP32S3_Mesh_Snapserver/main/snapserver.c

/*
 * ESP32-S3 Mini Snapserver
 *
 * Snapcast binary protocol implementation for one mono Opus stream.
 * Socket writes and client teardown are synchronized to prevent message
 * interleaving and descriptor reuse races.
 *
 * The Hello message of every client is parsed and kept, so the JSON-RPC
 * control server on port 1705 can report the connected clients in
 * Server.GetStatus. Without this the controller UI shows an empty group.
 */
#include "snapserver.h"

#include <errno.h>
#include <stdbool.h>
#include <stdint.h>
#include <stdlib.h>
#include <string.h>
#include <unistd.h>
#include <sys/select.h>
#include <sys/socket.h>
#include <sys/time.h>
#include <time.h>
#include <netinet/in.h>
#include <netinet/tcp.h>
#include <arpa/inet.h>

#include "cJSON.h"
#include "client_store.h"
#include "cpu_stats.h"
#include "device_config.h"
#include "esp_heap_caps.h"
#include "esp_log.h"
#include "esp_timer.h"
#include "esp_wifi.h"
#include "freertos/FreeRTOS.h"
#include "freertos/queue.h"
#include "freertos/semphr.h"
#include "freertos/task.h"
#include "freertos/idf_additions.h"
#include "audio_i2s.h"
#include "audio_opus.h"

static const char *TAG = "SNAPSERVER";

#define MAX_CLIENTS             SNAPSERVER_MAX_CLIENTS
#define RX_MAX                  4096
#define SNAP_PROTOCOL_VER       2
/*
 * Task stacks live in PSRAM, which is 8 MB here and barely used, while the
 * Wi-Fi driver competes for internal DRAM. Only the TCB stays internal, at
 * about a hundred bytes, so a client slot costs internal memory only for its
 * lwIP socket. The TCBs of tasks created this way must be released with
 * vTaskDeleteWithCaps(), and the API warns against self-deletion -- which is
 * why the connection tasks below are permanent and park between sessions
 * instead of being created per connection.
 */
#define TASK_STACK_CAPS (MALLOC_CAP_SPIRAM | MALLOC_CAP_8BIT)

/*
 * Generous on purpose. These were once trimmed to just above their measured
 * high-water marks, and snapsend3 then overflowed the moment a send actually
 * failed: a high-water mark only covers paths that have run, and the error
 * path with its two formatted ESP_LOGW calls had never run during the
 * measurement. vsnprintf alone wants several hundred bytes.
 *
 * The reason for trimming is gone anyway. Both stacks are allocated from
 * PSRAM now, so what they cost is 8 MB of otherwise idle memory rather than
 * the internal DRAM the Wi-Fi driver needs.
 */
#define CLIENT_TASK_STACK       6144
#define SERVER_TASK_STACK       8192
#define AUDIO_TASK_STACK        8192

/*
 * Chunk fan-out.
 *
 * The encode/capture loop used to send to every client itself, so its 20 ms
 * budget grew with the client count. Measured with four clients: average
 * frame interval 20449 us instead of 20000, single iterations up to 61 ms,
 * because a socket reported writable still blocks inside send() until the
 * whole chunk is out (~10 ms per client on a busy channel). The resulting
 * drift made the server re-anchor its capture timeline every few seconds,
 * which every client then saw as a timestamp jump.
 *
 * Now audio_task only drops each chunk into a pool slot and posts a
 * reference to each client's queue; one sender task per client does the
 * blocking send. Sends of different clients overlap instead of adding up,
 * which is the whole point -- in a shared task ten clients would serialise
 * into ~100 ms per round against a 20 ms chunk interval.
 *
 * Slots are recycled after CHUNK_POOL_SIZE chunks. A sender that has fallen
 * further behind than that finds its slot's sequence changed and drops the
 * chunk, which is the right outcome: the audio is long overdue anyway.
 *
 * Backlog: each client may fall up to ~2.4 s behind before anything is
 * dropped. It used to be ~0.4 s (8 queued chunks plus the TCP send buffer),
 * and anything beyond that was thrown away -- so a stall of a second or two,
 * which the client's own bufferMs (3 s) could have ridden out, turned into a
 * permanent hole in the stream instead. Measured on device: switching one
 * client off cut the throughput of *all* others to roughly a third for ~3 s,
 * the server discarded 54-113 chunks per remaining client, and every one of
 * them glitched. With the backlog the same stall only delays those chunks;
 * TCP then drains the queue much faster than real time (96 kbit/s against a
 * link of several Mbit/s) and the client files them in by timestamp.
 *
 * What gets dropped now is decided by age (see max_chunk_age_us()), not by
 * queue depth: a chunk the client could no longer play in time is useless,
 * everything younger is worth waiting for. The pool has to span more than
 * the longest backlog, or a queued slot would be overwritten before its
 * sender gets to it. Pool and queue storage both live in PSRAM -- ~190 kB
 * and ~1 kB per client of otherwise idle memory, nothing from internal DRAM.
 */
#define CHUNK_POOL_SIZE        128   /* 2.56 s at 20 ms per chunk          */
#define CLIENT_TX_QUEUE_DEPTH  120   /* 2.4 s                              */
#define CHUNK_BACKLOG_MAX_US   2400000LL
/* Kept free below bufferMs so a late chunk still lands before it is due. */
#define CHUNK_AGE_MARGIN_US     600000LL
/*
 * Pause between retries of a chunk the socket refused. Each refused attempt
 * has already blocked for up to CLIENT_SEND_TIMEOUT_US inside send(); the
 * pause is taken without the send mutex so client_task's Time replies get a
 * turn in between.
 */
#define SEND_RETRY_DELAY_MS       20
#define SENDER_TASK_STACK     3584
/* Below audio_task (6) so encoding never waits behind a blocked send. */
#define SENDER_TASK_PRIORITY     5

/*
 * Statistics are printed from their own low-priority task, never from
 * audio_task. Four log lines per second at 115200 baud are ~42 ms of
 * blocking UART time; against a budget of 1000 ms per second for 50 frames
 * that is far more than the ~0.5 % by which the capture loop was running
 * late, and the DMA ring (40 ms) cannot absorb it indefinitely -- the
 * result was audible dropouts.
 */
#define STATS_TASK_STACK      3072
#define STATS_TASK_PRIORITY      2

/* Single socket write timeout. */
#define CLIENT_SEND_TIMEOUT_US   300000

/*
 * How long a half-written message may keep retrying before the connection is
 * declared dead. Only reached once send() has already accepted part of it.
 */
#define PARTIAL_SEND_LIMIT_US   1000000

/*
 * How long anything may wait for a client's send mutex. The mutex is held
 * across a whole message, so without a bound a stuck wire chunk also blocks
 * that client's Time replies -- which is exactly what the logs showed: the
 * client's chunks/s went to 0 AND its time_msgs froze, both directions dead
 * for seconds while every other client kept streaming.
 */
#define SEND_MUTEX_WAIT_MS          1000

/*
 * Wake-up interval for the blocking recv() in client_task(), not a
 * disconnect criterion: hitting it merely lets the loop re-check whether
 * the client is still active before waiting again. A client that never
 * sends anything is perfectly legal -- our own ported ESP32 client does
 * exactly that, since it ignores SNAP_MSG_TIME -- and used to be dropped
 * every ~31 s here, reconnecting endlessly. Detecting a peer that vanished
 * without a FIN/RST is the TCP keepalive's job below (~25 s), which
 * surfaces as a real recv() error rather than a timeout.
 */
#define CLIENT_RECV_TIMEOUT_US  30000000

/*
 * How long a client may send nothing at all before it counts as gone.
 *
 * The keepalive referred to above cannot do this job: it only probes an idle
 * connection, and a stalled client never is idle -- audio_task keeps queueing
 * chunks, so TCP always has unacked data outstanding and falls back on
 * retransmission with exponential backoff, which takes minutes. Seen on
 * device: a client at -43 dBm went to 0 chunks/s with time_msgs frozen at 43
 * and skipped climbing past 640, still held by the server.
 *
 * Nothing used to notice because a stalled send eventually failed hard and
 * closed the client. Since a wire chunk became droppable, sends no longer
 * fail at all (send_errors=0 throughout), so the peer has to be judged by
 * what it sends instead.
 *
 * Safe at this length because every Snapcast client sends a Time request at
 * least once a second; twenty seconds of complete silence is not a quiet
 * peer, it is an absent one.
 */
#define CLIENT_SILENCE_LIMIT_US 20000000

/*
 * Seconds in a row in which more chunks for a client were dropped than
 * delivered before it is closed, so that it reconnects. The silence limit
 * above misses this case: on 2026-10-01 a freshly connected client kept
 * sending Time requests (time_msgs rising) while the way to it carried
 * 0-17 of 50 chunks/s, and it stuttered for ~100 s until a send finally
 * stalled hard. A new connection was fine at once.
 */
#define CLIENT_STALL_SECONDS 3

/* TCP keepalive: idle 10s, then 3 probes 5s apart -> dead peer detected
 * after ~25s even while client_task is blocked waiting for the next
 * message. */
#define CLIENT_KEEPALIVE_IDLE_SEC   10
#define CLIENT_KEEPALIVE_INTVL_SEC  5
#define CLIENT_KEEPALIVE_COUNT      3

/* The Opus stream on the wire is mono, independent of the local I2S link. */
#define SNAPSTREAM_CHANNELS     1

/*
 * Snapcast writes this constant as a little-endian uint32_t into the
 * codec header.
 */
#define SNAP_OPUS_ID            0x4F505553U

enum {
    SNAP_TYPE_BASE = 0,
    SNAP_TYPE_CODEC_HEADER = 1,
    SNAP_TYPE_WIRE_CHUNK = 2,
    SNAP_TYPE_SERVER = 3,
    SNAP_TYPE_TIME = 4,
    SNAP_TYPE_HELLO = 5,
    SNAP_TYPE_CLIENT_INFO = 7,
    SNAP_TYPE_ERROR = 8,
    /* Ours, not Snapcast's: config requests to our own clients and their
     * answers, see snapserver_remote_request(). Only ever sent to a client
     * that said "SnapMesh" in its Hello. */
    SNAP_TYPE_SNAPMESH_CONFIG = 100
};

typedef struct __attribute__((packed)) {
    uint16_t type;
    uint16_t id;
    uint16_t refers_to;
    int32_t sent_sec;
    int32_t sent_usec;
    int32_t received_sec;
    int32_t received_usec;
    uint32_t size;
} snap_base_t;

typedef struct {
    uint32_t sequence; /* 0 marks a slot that was never filled */
    uint32_t size;
    int64_t timestamp_us;
    uint8_t data[AUDIO_MAX_OPUS_PACKET];
} chunk_slot_t;

/* What a client's queue carries: which slot, and which generation of it. */
typedef struct {
    uint16_t slot;
    uint32_t sequence;
} tx_item_t;

typedef struct {
    int fd;
    bool active;
    bool ready;
    uint16_t next_id;
    TaskHandle_t task;
    SemaphoreHandle_t send_mutex;
    char peer[16];

    /* Identity from the Hello message, guarded by s_clients_lock. */
    char id[64];
    char name[64];
    char hostname[64];
    char mac[24];
    char arch[24];
    char os[32];
    char version[24];
    int32_t instance;
    int32_t protocol_ver;

    /* Mutable state controlled via the JSON-RPC interface. */
    int32_t volume_percent;
    bool muted;
    int32_t latency_ms;

    /* Announcement mute last pushed in ServerSettings, see
     * snapserver_refresh_announcement(). Kept apart from `muted`, which is
     * the control app's setting and must survive an announcement. */
    bool voice_muted_sent;

    /* Announcement flag last pushed, so snapserver_refresh_announcement()
     * knows which clients still need to hear about a change. */
    bool announcement_sent;

    /*
     * One of our own clients, i.e. it said so in its Hello ("SnapMesh").
     * Those get the announcement as a flag of its own and silence their
     * music themselves, so the server does not have to know who is deep
     * enough in the tree to miss it. A foreign Snapcast client knows no
     * such flag and is muted outright instead.
     */
    bool is_snapmesh;

    /* Mesh-Lite level our own clients report in their Hello (root = 1),
     * 0 when unknown -- a foreign client, or a build without Mesh-Lite. */
    uint8_t mesh_level;

    int32_t last_seen_sec;
    int32_t last_seen_usec;

    /* Accounting, only touched under s_clients_lock. */
    uint32_t chunks_sent;
    uint32_t chunk_bytes;
    uint32_t chunk_errors;
    uint32_t chunks_skipped;
    uint32_t time_msgs;

    /* Fan-out, see the CHUNK_POOL_SIZE comment above. */
    QueueHandle_t tx_queue;
    StaticQueue_t *tx_queue_ctrl;   /* internal: holds the queue's spinlock */
    uint8_t *tx_queue_storage;      /* PSRAM: the queued items themselves   */
    TaskHandle_t tx_task;

    /*
     * Unused stack words, each task measuring its own. Read from outside via
     * the handle instead and a task that has just deleted itself takes the
     * caller down with it. This is here to answer one question with numbers:
     * whether 8 kB per connection and 3 kB per sender can come down far
     * enough for SNAPSERVER_MAX_CLIENTS speakers to fit in internal DRAM.
     */
    uint16_t conn_stack_free;
    uint16_t tx_stack_free;
    uint8_t *tx_payload; /* 12 B header + chunk, PSRAM */
} client_t;

static client_t s_clients[MAX_CLIENTS];

static struct {
    int64_t avg_us;
    int64_t min_us;
    int64_t max_us;
    uint32_t samples;
    bool fresh;
} s_frame_stats;

static chunk_slot_t *s_chunk_pool;
static uint32_t s_chunk_write;     /* next slot to fill, wraps at CHUNK_POOL_SIZE */
static uint32_t s_chunk_sequence;  /* never 0 once running, see chunk_slot_t */

/*
 * How old a queued chunk may get before its sender gives up on it; see
 * max_chunk_age_us(). 32 bits on purpose: read by every sender without a
 * lock, and at most 2.4e6 it cannot be read half-written.
 */
static volatile int32_t s_max_chunk_age_us = (int32_t)CHUNK_BACKLOG_MAX_US;

/*
 * The age limit follows the bufferMs the clients are told: the client plays
 * a chunk bufferMs after its capture, so one that is older than that minus
 * a margin would arrive too late to matter. Capped by what the pool holds.
 */
static int32_t max_chunk_age_us(uint16_t buffer_ms)
{
    const int64_t buffer_us = (int64_t)buffer_ms * 1000LL;
    int64_t age = buffer_us - CHUNK_AGE_MARGIN_US;
    if (age < buffer_us / 2) {
        age = buffer_us / 2;
    }
    if (age > CHUNK_BACKLOG_MAX_US) {
        age = CHUNK_BACKLOG_MAX_US;
    }
    return (int32_t)age;
}
/*
 * True while a voice announcement runs (voice_announce.c). Every client that
 * is not a direct child of this AP is then sent muted=true in its
 * ServerSettings, on top of whatever the control app set -- see
 * send_server_settings() and snapserver_refresh_announcement().
 */
static volatile bool s_announcement_active;

static int level1_match_rssi(const char *mac, const wifi_sta_list_t *sta_list);
static void mark_client_failed(client_t *client);

static portMUX_TYPE s_clients_lock = portMUX_INITIALIZER_UNLOCKED;

/*
 * The one config request in flight, see snapserver_remote_request(). The
 * fields are guarded by s_clients_lock; s_remote_mutex keeps a second
 * request out until the first has its answer or gave up.
 */
static struct {
    int slot;          /* client slot asked, -1 when nothing is pending */
    uint16_t id;       /* the request's message id, echoed in refers_to */
    uint8_t *payload;  /* the answer, handed over by client_session()   */
    uint32_t size;
    bool failed;       /* the connection closed before an answer came   */
} s_remote = { .slot = -1 };
static uint16_t s_remote_next_id;
static SemaphoreHandle_t s_remote_mutex;
static SemaphoreHandle_t s_remote_done;
static TaskHandle_t s_server_task;
static TaskHandle_t s_audio_task;
static bool s_started;

/*
 * The ESP has no RTC or SNTP, so its wall clock starts at an arbitrary
 * anchor. Snapcast clients report their real wall clock in every Time
 * message and compute "diff to server" in 32-bit milliseconds. An offset of
 * months overflows that arithmetic, the chunk age becomes nonsense and the
 * client discards all audio ("No chunks available"). Adopt the clock of the
 * first client that talks to us; afterwards the offset is near zero.
 */
static bool s_clock_synced;

/*
 * Lower bound for a timestamp to be considered a real wall clock
 * (2024-01-01). Uptime based clients report far smaller values and are
 * ignored for clock adoption.
 */
#define SNAP_CLOCK_PLAUSIBLE_MIN_SEC 1704067200L

/*
 * Snapcast clients interpret all timestamps as wall clock time. Using the
 * raw esp_timer uptime makes every wire chunk appear decades old to a client
 * whose clock runs on epoch time, so the client drops all of them and reports
 * "No chunks available". Without an RTC or SNTP we cannot know the real time,
 * but placing the clock in a plausible epoch range is sufficient: the client
 * only needs a consistent, monotonic base to compute its own offset from.
 */
#define SNAP_EPOCH_BASE_SEC 1767225600LL /* 2026-01-01T00:00:00Z */

/*
 * Offset from the monotonic esp_timer to wall clock, in microseconds.
 *
 * Do NOT use gettimeofday()/settimeofday() as the Snapcast timebase on this
 * target: the POSIX clock is driven by the RTC slow clock (150 kHz RC
 * oscillator) which can be off by several percent, while esp_timer runs off
 * the crystal. Mixing both makes the server clock drift against the client
 * by tens of milliseconds per second, so the client's time offset is stale
 * the moment it is computed and every chunk falls outside the buffer window.
 * Keep one monotonic source and shift it by a settable offset instead.
 */
static int64_t s_wall_offset_us = SNAP_EPOCH_BASE_SEC * 1000000LL;

static int64_t now_us(void)
{
    /*
     * s_wall_offset_us is a 64-bit value re-anchored from handle_time() on
     * another task; on this 32-bit target that write/read is not atomic, so
     * both sides must go through the same critical section to avoid a torn
     * value.
     */
    portENTER_CRITICAL(&s_clients_lock);
    const int64_t offset = s_wall_offset_us;
    portEXIT_CRITICAL(&s_clients_lock);

    return esp_timer_get_time() + offset;
}

static void now_ts(int32_t *sec, int32_t *usec)
{
    const int64_t t = now_us();
    *sec = (int32_t)(t / 1000000LL);
    *usec = (int32_t)(t % 1000000LL);
}

/*
 * 0 = sent, -1 = the connection is gone, 1 = the send buffer stayed full and
 * nothing at all was written (only ever returned when droppable is set).
 *
 * A full socket buffer means the peer is behind, not that it died: SO_SNDTIMEO
 * makes send() report that as EWOULDBLOCK. Treating it as fatal used to tear
 * the client down, and since a reconnect costs a fresh handshake plus a refill
 * of the whole bufferMs, a stall that the client could have ridden out turned
 * into a guaranteed audible gap.
 *
 * Once part of a message has gone out we are committed -- abandoning it would
 * leave the peer's framing desynchronised -- so from that point on we keep
 * retrying until PARTIAL_SEND_LIMIT_US, and only then give up for real.
 */
static int send_all(int fd, const void *data, size_t len, bool droppable)
{
    const uint8_t *p = (const uint8_t *)data;
    bool wrote_any = false;
    int64_t deadline_us = 0;

    while (len > 0U) {
        const int n = send(fd, p, len, 0);
        if (n < 0 && errno == EINTR) {
            continue;
        }
        if (n < 0 && (errno == EAGAIN || errno == EWOULDBLOCK)) {
            if (!wrote_any && droppable) {
                return 1;
            }
            const int64_t now = esp_timer_get_time();
            if (deadline_us == 0) {
                deadline_us = now + PARTIAL_SEND_LIMIT_US;
                continue;
            }
            if (now < deadline_us) {
                continue;
            }
            ESP_LOGW(TAG,
                     "send stalled: fd=%d, giving up with %u B left",
                     fd,
                     (unsigned)len);
            return -1;
        }
        if (n <= 0) {
            ESP_LOGW(TAG,
                     "send failed: fd=%d rc=%d errno=%d (%s), remaining=%u",
                     fd,
                     n,
                     errno,
                     strerror(errno),
                     (unsigned)len);
            return -1;
        }
        p += n;
        len -= (size_t)n;
        wrote_any = true;
    }
    return 0;
}

/*
 * 0 = complete, -1 = error/EOF, RECV_IDLE = the receive timeout expired
 * before the first byte arrived. Only the latter is harmless: once part of
 * a message has been read there is no way to resync, so a timeout mid-way
 * is treated as an error like any other.
 */
#define RECV_IDLE 1

static int recv_all(int fd, void *data, size_t len)
{
    uint8_t *p = (uint8_t *)data;
    bool got_any = false;

    while (len > 0U) {
        const int n = recv(fd, p, len, 0);
        if (n < 0 && errno == EINTR) {
            continue;
        }
        if (n < 0 && !got_any && (errno == EAGAIN || errno == EWOULDBLOCK)) {
            return RECV_IDLE;
        }
        if (n <= 0) {
            return -1;
        }
        got_any = true;
        p += n;
        len -= (size_t)n;
    }
    return 0;
}

static int send_msg_unlocked(int fd,
                             uint16_t type,
                             uint16_t id,
                             uint16_t refers_to,
                             const void *payload,
                             uint32_t payload_size,
                             int32_t received_sec,
                             int32_t received_usec)
{
    snap_base_t base;
    memset(&base, 0, sizeof(base));
    now_ts(&base.sent_sec, &base.sent_usec);
    base.type = type;
    base.id = id;
    base.refers_to = refers_to;
    base.received_sec = received_sec;
    base.received_usec = received_usec;
    base.size = payload_size;

    /*
     * A dropped wire chunk is a click at worst; a dropped ServerSettings,
     * CodecHeader or Time reply breaks the session outright, so those wait.
     */
    const bool droppable = (type == SNAP_TYPE_WIRE_CHUNK);

    const int header_rc = send_all(fd, &base, sizeof(base), droppable);
    if (header_rc != 0) {
        return header_rc;
    }
    if (payload_size > 0U && send_all(fd, payload, payload_size, false) < 0) {
        return -1;
    }
    return 0;
}

static int client_send_msg(client_t *client,
                           uint16_t type,
                           uint16_t id,
                           uint16_t refers_to,
                           const void *payload,
                           uint32_t payload_size,
                           int32_t received_sec,
                           int32_t received_usec,
                           bool require_ready)
{
    if (client == NULL || client->send_mutex == NULL) {
        return -1;
    }

    if (xSemaphoreTake(client->send_mutex,
                       pdMS_TO_TICKS(SEND_MUTEX_WAIT_MS)) != pdTRUE) {
        /* Someone else is mid-message. Dropping this one beats queueing up
         * behind it; a Time reply the client misses it simply asks for
         * again. */
        return 1;
    }

    int fd = -1;
    bool allowed = false;
    portENTER_CRITICAL(&s_clients_lock);
    allowed = client->active && client->fd >= 0 &&
              (!require_ready || client->ready);
    if (allowed) {
        fd = client->fd;
    }
    portEXIT_CRITICAL(&s_clients_lock);

    int result = -1;
    if (allowed) {
        result = send_msg_unlocked(fd,
                                   type,
                                   id,
                                   refers_to,
                                   payload,
                                   payload_size,
                                   received_sec,
                                   received_usec);
    }

    xSemaphoreGive(client->send_mutex);
    return result;
}

static int send_server_settings(client_t *client, uint16_t refers_to)
{
    char json[128];
    int32_t volume = 100;
    bool muted = false;
    int32_t latency = 0;
    char mac[24];

    portENTER_CRITICAL(&s_clients_lock);
    volume = client->volume_percent;
    muted = client->muted;
    latency = client->latency_ms;
    strlcpy(mac, client->mac, sizeof(mac));
    portEXIT_CRITICAL(&s_clients_lock);

    /*
     * Music must not clash with an announcement in the same room, but who
     * actually hears the announcement depends on the mesh tree, which the
     * server cannot see past the first level (everything deeper hides
     * behind its parent's NAPT).
     *
     * So our own clients get the plain fact that an announcement is running
     * and silence their music themselves; they play the announcement if it
     * reaches them, at the user's volume. `muted` keeps its original
     * meaning for them: the control app's setting, which must survive an
     * announcement.
     *
     * A foreign Snapcast client (Android, iOS, desktop) knows no such flag
     * and cannot receive an announcement either -- that runs over our own
     * UDP channel, not over Snapcast. For it the announcement is therefore
     * folded into `muted`, whatever its level: a phone sitting right next
     * to the root is as unable to play the announcement as one three hops
     * away, so it has to fall silent for it. Sent on top of the user's mute
     * rather than written into it, so nothing has to be restored
     * afterwards, and a client that (re)connects mid-announcement gets it
     * right in its handshake.
     */
    bool is_snapmesh = false;
    portENTER_CRITICAL(&s_clients_lock);
    is_snapmesh = client->is_snapmesh;
    portEXIT_CRITICAL(&s_clients_lock);

    const bool announcement = s_announcement_active;
    const bool voice_muted = announcement && !is_snapmesh;
    portENTER_CRITICAL(&s_clients_lock);
    client->voice_muted_sent = voice_muted;
    client->announcement_sent = announcement;
    portEXIT_CRITICAL(&s_clients_lock);
    const bool effective_muted = muted || voice_muted;

    device_config_t cfg;
    device_config_get(&cfg);
    const uint16_t buffer_ms = cfg.buffer_ms;
    /* Follows whatever bufferMs the clients are told, including a change
     * made in the web config since startup. */
    s_max_chunk_age_us = max_chunk_age_us(buffer_ms);

    const int json_len = snprintf(
        json,
        sizeof(json),
        "{\"bufferMs\":%u,\"latency\":%ld,\"muted\":%s,\"volume\":%ld,"
        "\"announcement\":%s}",
        (unsigned)buffer_ms,
        (long)latency,
        effective_muted ? "true" : "false",
        (long)volume,
        announcement ? "true" : "false");

    if (json_len <= 0 || (size_t)json_len >= sizeof(json)) {
        return -1;
    }

    const uint32_t len = (uint32_t)json_len;
    uint8_t payload[sizeof(uint32_t) + sizeof(json)];

    memcpy(payload, &len, sizeof(len));
    memcpy(payload + sizeof(len), json, len);

    ESP_LOGI(TAG,
             "Sending ServerSettings: bufferMs=%u latency=%ld muted=%s%s volume=%ld"
             " announcement=%s",
             (unsigned)buffer_ms,
             (long)latency,
             effective_muted ? "true" : "false",
             voice_muted ? " (announcement)" : "",
             (long)volume,
             announcement ? "true" : "false");

    return client_send_msg(client,
                           SNAP_TYPE_SERVER,
                           1,
                           refers_to,
                           payload,
                           (uint32_t)(sizeof(len) + len),
                           0,
                           0,
                           false);
}

static int send_codec_header(client_t *client, uint16_t refers_to)
{
    static const char codec[] = "opus";
    const uint32_t codec_size = 4;
    const uint32_t header_size = 12;
    uint8_t payload[4 + 4 + 4 + 12];
    size_t off = 0;

    memcpy(payload + off, &codec_size, 4); off += 4;
    memcpy(payload + off, codec, codec_size); off += codec_size;
    memcpy(payload + off, &header_size, 4); off += 4;

    const uint32_t opus_id = SNAP_OPUS_ID;
    const uint32_t rate = AUDIO_SAMPLE_RATE;
    const uint16_t bits = AUDIO_BITS;
    const uint16_t channels = SNAPSTREAM_CHANNELS;

    memcpy(payload + off, &opus_id, 4); off += 4;
    memcpy(payload + off, &rate, 4); off += 4;
    memcpy(payload + off, &bits, 2); off += 2;
    memcpy(payload + off, &channels, 2); off += 2;

    ESP_LOGI(TAG,
             "Sending CodecHeader: codec=opus rate=%lu bits=%u channels=%u "
             "header_size=%lu opus_id=0x%08lX",
             (unsigned long)rate,
             (unsigned)bits,
             (unsigned)channels,
             (unsigned long)header_size,
             (unsigned long)opus_id);

    return client_send_msg(client,
                           SNAP_TYPE_CODEC_HEADER,
                           2,
                           refers_to,
                           payload,
                           (uint32_t)off,
                           0,
                           0,
                           false);
}

/*
 * Sends a wire chunk as a single buffer whose first sizeof(snap_base_t)
 * bytes the caller left free for the header.
 *
 * Header and payload used to go out as two send() calls, and that was the
 * whole problem: the 26-byte header nearly always fits in the socket buffer
 * even when the ~262-byte payload does not, which commits us to finishing a
 * message we cannot finish. send_all() then retries with the mutex held
 * while the client's Time replies queue up behind it. As one call the
 * message is either accepted or refused outright; a refused wire chunk goes
 * back to sender_task, which retries it until it is too old to matter.
 */
static int client_send_frame(client_t *client, uint8_t *frame, uint32_t payload_size)
{
    if (client == NULL || client->send_mutex == NULL) {
        return -1;
    }

    if (xSemaphoreTake(client->send_mutex,
                       pdMS_TO_TICKS(SEND_MUTEX_WAIT_MS)) != pdTRUE) {
        return 1;
    }

    int fd = -1;
    portENTER_CRITICAL(&s_clients_lock);
    const bool allowed = client->active && client->fd >= 0 && client->ready;
    if (allowed) {
        fd = client->fd;
    }
    portEXIT_CRITICAL(&s_clients_lock);

    int result = -1;
    if (allowed) {
        snap_base_t base;
        memset(&base, 0, sizeof(base));
        now_ts(&base.sent_sec, &base.sent_usec);
        base.type = SNAP_TYPE_WIRE_CHUNK;
        base.size = payload_size;
        memcpy(frame, &base, sizeof(base));

        result = send_all(fd, frame, sizeof(base) + payload_size, true);
    }

    xSemaphoreGive(client->send_mutex);
    return result;
}

/* send_wire_chunk() results besides 0 (sent) and -1 (connection gone). */
#define CHUNK_BUSY 1   /* nothing written, the peer is behind: retry it   */
#define CHUNK_DROP 2   /* this chunk can never go out (slot reused, size) */

static int send_wire_chunk(client_t *client, const tx_item_t *item)
{
    const chunk_slot_t *slot = &s_chunk_pool[item->slot];
    uint8_t *payload = client->tx_payload + sizeof(snap_base_t);

    /*
     * The timestamp originates from esp_timer (uptime) and must be expressed
     * in the same wall clock domain that now_ts() reports.
     *
     * s_wall_offset_us is re-anchored when a plausible wall clock is learned.
     * Adding the same offset to the monotonic capture timestamp keeps message
     * headers and audio chunks in one consistent time domain.
     */
    portENTER_CRITICAL(&s_clients_lock);
    const int64_t wall_offset_us = s_wall_offset_us;
    portEXIT_CRITICAL(&s_clients_lock);
    const int64_t chunk_us = slot->timestamp_us + wall_offset_us;

    const int32_t sec = (int32_t)(chunk_us / 1000000LL);
    const int32_t usec = (int32_t)(chunk_us % 1000000LL);
    const uint32_t size = slot->size;

    if (size > AUDIO_MAX_OPUS_PACKET) {
        return CHUNK_DROP;
    }

    memcpy(payload + 0, &sec, 4);
    memcpy(payload + 4, &usec, 4);
    memcpy(payload + 8, &size, 4);
    memcpy(payload + 12, slot->data, size);

    /*
     * Re-read the sequence only after copying: audio_task may have started
     * refilling this slot while we were reading it, in which case the copy is
     * a mix of two chunks and must not go out.
     */
    if (slot->sequence != item->sequence) {
        return CHUNK_DROP;
    }

    /* 0, -1, or 1 == CHUNK_BUSY (socket full or send mutex taken). */
    const int rc = client_send_frame(client, client->tx_payload, 12U + size);

    portENTER_CRITICAL(&s_clients_lock);
    if (rc == 0) {
        client->chunks_sent++;
        client->chunk_bytes += (12U + size);
    } else if (rc < 0) {
        client->chunk_errors++;
    }
    portEXIT_CRITICAL(&s_clients_lock);

    return rc;
}

static int handle_time(client_t *client,
                       const snap_base_t *base,
                       const uint8_t *payload,
                       uint32_t size)
{
    if (client == NULL || base == NULL || payload == NULL || size != 8U) {
        ESP_LOGW(TAG,
                 "Time message rejected: size=%lu (expected 8)",
                 (unsigned long)size);
        return -1;
    }

    int32_t server_recv_sec = 0;
    int32_t server_recv_usec = 0;
    now_ts(&server_recv_sec, &server_recv_usec);

    int64_t client_send_us =
        (int64_t)base->sent_sec * 1000000LL + base->sent_usec;
    int64_t server_recv_us =
        (int64_t)server_recv_sec * 1000000LL + server_recv_usec;

    /*
     * Clock adoption with plausibility filter.
     *
     * Not every client owns a real clock: our own ESP snapclient has neither
     * RTC nor SNTP and reports plain uptime (a few 100000 s at most). Adopting
     * that would move the server clock back to 1970 and make things worse.
     * Only accept a timestamp that can actually be a wall clock, i.e. one that
     * lies after SNAP_CLOCK_PLAUSIBLE_MIN_SEC. PC and Android clients qualify,
     * uptime-based ones do not.
     */
    portENTER_CRITICAL(&s_clients_lock);
    const bool already_synced = s_clock_synced;
    if (!already_synced && base->sent_sec > SNAP_CLOCK_PLAUSIBLE_MIN_SEC) {
        s_clock_synced = true;
    }
    portEXIT_CRITICAL(&s_clients_lock);

    if (!already_synced && base->sent_sec > SNAP_CLOCK_PLAUSIBLE_MIN_SEC) {

        const int64_t skew_us = client_send_us - server_recv_us;

        if (skew_us > 60000000LL || skew_us < -60000000LL) {
            /*
             * Re-anchor the monotonic timebase; no POSIX clock involved.
             * s_clock_synced was already claimed above (still inside this
             * function's single-threaded-per-client path but guarded
             * against a second client racing the same adoption window).
             */
            portENTER_CRITICAL(&s_clients_lock);
            s_wall_offset_us = client_send_us - esp_timer_get_time();
            portEXIT_CRITICAL(&s_clients_lock);

            ESP_LOGW(TAG,
                     "Adopted wall clock from %s: %ld s (skew was %lld s)",
                     client->peer,
                     (long)base->sent_sec,
                     (long long)(skew_us / 1000000LL));

            now_ts(&server_recv_sec, &server_recv_usec);
            server_recv_us =
                (int64_t)server_recv_sec * 1000000LL + server_recv_usec;
        }
    }

    const int64_t delta = server_recv_us - client_send_us;

    /*
     * Normalise into a valid timeval: the microsecond field must always be
     * in [0, 999999], with the borrow carried into the seconds field.
     * Plain C division/modulo truncate towards zero, which produced a
     * negative usec for negative deltas. Snapcast clients then compute a
     * bogus server time offset and discard every wire chunk as being
     * outside the buffer window ("No chunks available").
     */
    int32_t delta_sec = (int32_t)(delta / 1000000LL);
    int32_t delta_usec = (int32_t)(delta % 1000000LL);

    if (delta_usec < 0) {
        delta_usec += 1000000;
        delta_sec -= 1;
    }

    uint8_t response[8];

    memcpy(response + 0, &delta_sec, 4);
    memcpy(response + 4, &delta_usec, 4);

    uint32_t seen = 0;
    portENTER_CRITICAL(&s_clients_lock);
    client->time_msgs++;
    seen = client->time_msgs;
    portEXIT_CRITICAL(&s_clients_lock);

    if (seen <= 3U) {
        ESP_LOGI(TAG,
                 "Time #%lu from %s: client_sent=%ld.%06ld "
                 "server_recv=%ld.%06ld delta=%ld.%06ld",
                 (unsigned long)seen,
                 client->peer,
                 (long)base->sent_sec,
                 (long)base->sent_usec,
                 (long)server_recv_sec,
                 (long)server_recv_usec,
                 (long)delta_sec,
                 (long)delta_usec);
    }

    return client_send_msg(client,
                           SNAP_TYPE_TIME,
                           0,
                           base->id,
                           response,
                           sizeof(response),
                           server_recv_sec,
                           server_recv_usec,
                           false);
}

/* ------------------------------------------------------------------ */
/* Hello parsing                                                      */
/* ------------------------------------------------------------------ */

static void copy_json_string(char *dst,
                             size_t dst_size,
                             const cJSON *root,
                             const char *key,
                             const char *fallback)
{
    const cJSON *item = cJSON_GetObjectItemCaseSensitive(root, key);

    if (cJSON_IsString(item) && item->valuestring != NULL &&
        item->valuestring[0] != '\0') {
        strlcpy(dst, item->valuestring, dst_size);
    } else {
        strlcpy(dst, fallback != NULL ? fallback : "", dst_size);
    }
}

static int32_t json_int_or(const cJSON *root,
                           const char *key,
                           int32_t fallback)
{
    const cJSON *item = cJSON_GetObjectItemCaseSensitive(root, key);
    return cJSON_IsNumber(item) ? (int32_t)item->valuedouble : fallback;
}

/*
 * Parses the Hello payload and stores the client identity. Returns false if
 * the payload is malformed or the client speaks a newer stream protocol.
 */
static bool handle_hello(client_t *client,
                         const uint8_t *payload,
                         uint32_t size)
{
    if (payload == NULL || size < sizeof(uint32_t)) {
        return false;
    }

    uint32_t json_size = 0;
    memcpy(&json_size, payload, sizeof(json_size));
    if (json_size == 0U ||
        json_size > size - sizeof(uint32_t) ||
        json_size >= RX_MAX) {
        return false;
    }

    char *json = malloc((size_t)json_size + 1U);
    if (json == NULL) {
        return false;
    }
    memcpy(json, payload + sizeof(uint32_t), json_size);
    json[json_size] = '\0';

    cJSON *root = cJSON_Parse(json);
    free(json);

    if (root == NULL) {
        ESP_LOGW(TAG, "Hello payload is not valid JSON");
        return false;
    }

    const int32_t proto =
        json_int_or(root, "SnapStreamProtocolVersion", SNAP_PROTOCOL_VER);

    if (proto > SNAP_PROTOCOL_VER) {
        ESP_LOGW(TAG,
                 "Rejecting client with stream protocol %ld (supported: %d)",
                 (long)proto,
                 SNAP_PROTOCOL_VER);
        cJSON_Delete(root);
        return false;
    }

    /*
     * Fill a scratch copy first, then publish it under the lock. cJSON
     * allocations must not happen inside a critical section.
     */
    char id[64];
    char name[64];
    char hostname[64];
    char mac[24];
    char arch[24];
    char os[32];
    char version[24];

    copy_json_string(mac, sizeof(mac), root, "MAC", client->peer);
    copy_json_string(id, sizeof(id), root, "ID", mac);
    copy_json_string(hostname, sizeof(hostname), root, "HostName", id);
    copy_json_string(name, sizeof(name), root, "ClientName", hostname);
    copy_json_string(arch, sizeof(arch), root, "Arch", "unknown");
    copy_json_string(os, sizeof(os), root, "OS", "unknown");
    copy_json_string(version, sizeof(version), root, "Version", "0.0.0");

    const int32_t instance = json_int_or(root, "Instance", 1);
    /* Our own clients say so here, see send_hello() in snapclient.c. */
    const bool is_snapmesh = json_int_or(root, "SnapMesh", 0) != 0;
    /*
     * Reported once, at connect. Enough, because a node's level cannot
     * change under a live connection: moving to another parent gives it a
     * new address, and an ancestor moving takes the NAPT table this
     * connection runs through with it -- either way the client reconnects
     * and says Hello again.
     */
    int32_t mesh_level = json_int_or(root, "MeshLevel", 0);
    if (mesh_level < 0 || mesh_level > 15) {
        mesh_level = 0;
    }

    cJSON_Delete(root);

    /* What this client was last set to, if it has been here before. RAM
     * only -- this task's stack is in PSRAM, see client_store.h. */
    client_store_entry_t stored;
    const bool have_stored = client_store_get(id, &stored);
    if (have_stored && stored.name[0] != '\0') {
        strlcpy(name, stored.name, sizeof(name));
    }

    int32_t seen_sec = 0;
    int32_t seen_usec = 0;
    now_ts(&seen_sec, &seen_usec);

    portENTER_CRITICAL(&s_clients_lock);
    strlcpy(client->id, id, sizeof(client->id));
    strlcpy(client->name, name, sizeof(client->name));
    strlcpy(client->hostname, hostname, sizeof(client->hostname));
    strlcpy(client->mac, mac, sizeof(client->mac));
    strlcpy(client->arch, arch, sizeof(client->arch));
    strlcpy(client->os, os, sizeof(client->os));
    strlcpy(client->version, version, sizeof(client->version));
    client->instance = instance;
    client->is_snapmesh = is_snapmesh;
    client->mesh_level = (uint8_t)mesh_level;
    if (have_stored) {
        client->volume_percent = stored.volume_percent;
        client->muted = stored.muted;
        client->latency_ms = stored.latency_ms;
    }
    client->protocol_ver = proto;
    client->last_seen_sec = seen_sec;
    client->last_seen_usec = seen_usec;

    /*
     * The same client on another slot is a connection it has already given
     * up -- it reconnected, e.g. after a parent change -- that the server
     * would otherwise keep for up to CLIENT_SILENCE_LIMIT_US, listing the
     * client twice and streaming into the void. End it now.
     */
    client_t *stale[MAX_CLIENTS];
    size_t stale_count = 0;
    for (int i = 0; i < MAX_CLIENTS; ++i) {
        if (&s_clients[i] != client && s_clients[i].active &&
            strcmp(s_clients[i].id, id) == 0) {
            stale[stale_count++] = &s_clients[i];
        }
    }
    portEXIT_CRITICAL(&s_clients_lock);

    for (size_t i = 0; i < stale_count; ++i) {
        ESP_LOGW(TAG, "%s reconnected, closing its old connection from %s",
                 id, stale[i]->peer);
        mark_client_failed(stale[i]);
    }

    ESP_LOGI(TAG,
             "Hello from %s: id=%s name=%s host=%s os=%s arch=%s version=%s "
             "instance=%ld protocol=%ld",
             client->peer,
             id,
             name,
             hostname,
             os,
             arch,
             version,
             (long)instance,
             (long)proto);

    return true;
}

static int recv_message(int fd, snap_base_t *base, uint8_t **payload)
{
    const int header_result = recv_all(fd, base, sizeof(*base));
    if (header_result == RECV_IDLE) {
        return RECV_IDLE;
    }
    if (header_result < 0) {
        return -1;
    }
    if (base->size > RX_MAX) {
        return -2;
    }

    *payload = NULL;
    if (base->size > 0U) {
        *payload = malloc(base->size);
        if (*payload == NULL) {
            return -3;
        }
        if (recv_all(fd, *payload, base->size) < 0) {
            free(*payload);
            *payload = NULL;
            return -1;
        }
    }
    return 0;
}

static void close_client(client_t *client)
{
    if (client == NULL || client->send_mutex == NULL) {
        return;
    }

    xSemaphoreTake(client->send_mutex, portMAX_DELAY);

    int fd = -1;
    uint32_t chunks = 0;
    uint32_t bytes = 0;
    uint32_t errors = 0;
    uint32_t skipped = 0;
    uint32_t times = 0;
    char peer[sizeof(client->peer)];

    portENTER_CRITICAL(&s_clients_lock);
    fd = client->fd;
    chunks = client->chunks_sent;
    bytes = client->chunk_bytes;
    errors = client->chunk_errors;
    skipped = client->chunks_skipped;
    times = client->time_msgs;
    strlcpy(peer, client->peer, sizeof(peer));
    client->ready = false;
    client->active = false;
    client->fd = -1;
    /* `task` is the slot's permanent connection task and outlives the
     * session -- clearing it here would strand the slot for good. */
    const bool wake_remote = s_remote.slot == (int)(client - s_clients) &&
                             s_remote.payload == NULL && !s_remote.failed;
    if (wake_remote) {
        s_remote.failed = true;
    }
    portEXIT_CRITICAL(&s_clients_lock);

    /* A config request waiting on this client need not sit out its timeout. */
    if (wake_remote && s_remote_done != NULL) {
        xSemaphoreGive(s_remote_done);
    }

    if (fd >= 0) {
        shutdown(fd, SHUT_RDWR);
        close(fd);
    }

    xSemaphoreGive(client->send_mutex);

    ESP_LOGI(TAG,
             "Session summary %s: chunks_sent=%lu bytes=%lu send_errors=%lu "
             "skipped=%lu time_msgs=%lu",
             peer,
             (unsigned long)chunks,
             (unsigned long)bytes,
             (unsigned long)errors,
             (unsigned long)skipped,
             (unsigned long)times);
}

static void client_session(client_t *client)
{
    int fd = -1;

    portENTER_CRITICAL(&s_clients_lock);
    fd = client->fd;
    portEXIT_CRITICAL(&s_clients_lock);

    snap_base_t base;
    uint8_t *payload = NULL;

    /* Anything other than a complete message is fatal here, including the
     * idle timeout: a peer that connects without saying Hello is of no use. */
    if (recv_message(fd, &base, &payload) != 0 ||
        base.type != SNAP_TYPE_HELLO ||
        !handle_hello(client, payload, base.size)) {
        free(payload);
        payload = NULL;
        ESP_LOGW(TAG, "Invalid Hello");
        goto done;
    }

    /*
     * Snapcast clients send Hello as a request and wait for a reply whose
     * refersTo field carries the Hello message id. Answering with 0 leaves
     * the pending request unresolved, the client times out after 2 s,
     * reconnects and never starts its time sync.
     */
    const uint16_t hello_id = base.id;

    free(payload);
    payload = NULL;

    /* Not "< 0": a mutex timeout reports 1, and a client marked ready
     * without ServerSettings and CodecHeader would never decode anything. */
    if (send_server_settings(client, hello_id) != 0 ||
        send_codec_header(client, hello_id) != 0) {
        goto done;
    }

    portENTER_CRITICAL(&s_clients_lock);
    client->ready = true;
    portEXIT_CRITICAL(&s_clients_lock);
    ESP_LOGI(TAG, "Client handshake complete (%s, fd=%d)", client->peer, fd);

    for (;;) {
        portENTER_CRITICAL(&s_clients_lock);
        const bool active = client->active;
        fd = client->fd;
        portEXIT_CRITICAL(&s_clients_lock);

        if (!active || fd < 0) {
            break;
        }

        const int rc = recv_message(fd, &base, &payload);
        if (rc == RECV_IDLE) {
            /* Nothing sent for a while, which is legal -- loop back and
             * wait again, re-checking client->active on the way. */
            continue;
        }
        if (rc < 0) {
            ESP_LOGW(TAG,
                     "Client receive ended: %s rc=%d errno=%d (%s)",
                     client->peer,
                     rc,
                     errno,
                     strerror(errno));
            break;
        }

        client->conn_stack_free = (uint16_t)uxTaskGetStackHighWaterMark(NULL);

        int32_t seen_sec = 0;
        int32_t seen_usec = 0;
        now_ts(&seen_sec, &seen_usec);

        portENTER_CRITICAL(&s_clients_lock);
        client->last_seen_sec = seen_sec;
        client->last_seen_usec = seen_usec;
        portEXIT_CRITICAL(&s_clients_lock);

        switch (base.type) {
        case SNAP_TYPE_TIME:
            if (handle_time(client, &base, payload, base.size) < 0) {
                ESP_LOGW(TAG, "Time reply failed (%s)", client->peer);
                free(payload);
                payload = NULL;
                goto done;
            }
            break;
        case SNAP_TYPE_CLIENT_INFO:
            break;
        case SNAP_TYPE_SNAPMESH_CONFIG: {
            /* An answer nobody waits for any more (timed out) is dropped. */
            bool taken = false;
            portENTER_CRITICAL(&s_clients_lock);
            if (s_remote.slot == (int)(client - s_clients) &&
                s_remote.id == base.refers_to &&
                s_remote.payload == NULL && !s_remote.failed) {
                s_remote.payload = payload;
                s_remote.size = base.size;
                taken = true;
            }
            portEXIT_CRITICAL(&s_clients_lock);
            if (taken) {
                payload = NULL;
                xSemaphoreGive(s_remote_done);
            }
            break;
        }
        default:
            ESP_LOGD(TAG, "Ignoring client message type=%u", base.type);
            break;
        }

        free(payload);
        payload = NULL;
    }

done:
    free(payload);
    close_client(client);
    ESP_LOGI(TAG, "Client disconnected");
}

/*
 * One per client slot, created once at startup and parked on a notification
 * for the lifetime of the server -- the same reasoning as sender_task, plus
 * the stack is in PSRAM and freeing it from the task running on it is
 * exactly what vTaskDeleteWithCaps() warns about.
 */
static void client_task(void *arg)
{
    client_t *client = (client_t *)arg;

    for (;;) {
        ulTaskNotifyTake(pdTRUE, portMAX_DELAY);
        client_session(client);
    }
}

static void mark_client_failed(client_t *client)
{
    if (client == NULL) {
        return;
    }

    int fd = -1;
    portENTER_CRITICAL(&s_clients_lock);
    if (client->active) {
        client->ready = false;
        fd = client->fd;
    }
    portEXIT_CRITICAL(&s_clients_lock);

    if (fd >= 0) {
        shutdown(fd, SHUT_RDWR);
    }
}

/*
 * One per client slot, created once at startup and parked on its queue for
 * the lifetime of the server. Created statically rather than per connection
 * on purpose: a queue that audio_task may post to while the owning task is
 * being torn down is exactly the kind of race this file has already been
 * bitten by, and MAX_CLIENTS idle tasks cost only their stacks.
 */
static void sender_task(void *arg)
{
    client_t *client = (client_t *)arg;
    uint32_t stack_check = 0;

    for (;;) {
        tx_item_t item;
        if (xQueueReceive(client->tx_queue, &item, portMAX_DELAY) != pdTRUE) {
            continue;
        }

        bool send_it = false;
        portENTER_CRITICAL(&s_clients_lock);
        send_it = client->active && client->ready && client->fd >= 0;
        portEXIT_CRITICAL(&s_clients_lock);

        if (!send_it) {
            continue;
        }

        if ((++stack_check & 0xFFU) == 0U) {
            client->tx_stack_free =
                (uint16_t)uxTaskGetStackHighWaterMark(NULL);
        }

        /*
         * A refused chunk is retried, not skipped: the peer being behind is
         * what the backlog exists for (see CHUNK_POOL_SIZE). It is given up
         * only once it is too old to be played in time -- the timestamp is
         * the capture time on this device's esp_timer, so the age is exact.
         */
        int rc;
        for (;;) {
            const int64_t age_us =
                esp_timer_get_time() - s_chunk_pool[item.slot].timestamp_us;
            if (age_us > (int64_t)s_max_chunk_age_us) {
                rc = CHUNK_DROP;
                break;
            }

            rc = send_wire_chunk(client, &item);
            if (rc != CHUNK_BUSY) {
                break;
            }

            portENTER_CRITICAL(&s_clients_lock);
            const bool still_wanted = client->active && client->ready && client->fd >= 0;
            portEXIT_CRITICAL(&s_clients_lock);
            if (!still_wanted) {
                rc = CHUNK_DROP;
                break;
            }
            vTaskDelay(pdMS_TO_TICKS(SEND_RETRY_DELAY_MS));
        }

        if (rc == CHUNK_DROP) {
            portENTER_CRITICAL(&s_clients_lock);
            client->chunks_skipped++;
            portEXIT_CRITICAL(&s_clients_lock);
        } else if (rc < 0) {
            ESP_LOGW(TAG,
                     "Wire chunk send failed (%s); closing client",
                     client->peer);
            mark_client_failed(client);
        }
    }
}

/*
 * Prints everything the audio path measures, at low priority and off the
 * real-time path. See STATS_TASK_STACK for why this matters.
 */
/*
 * Level-1 = direct child of this node's own AP: matches mac against
 * esp_wifi_ap_get_sta_list(). Returns the real RSSI on a match, or 127 ("no
 * station matched") for a level-2+ client relayed via NAPT, or a phone that
 * reported no MAC in its Hello -- the sentinel stats_task's log line always
 * used, factored out here so snapserver_get_level1_client_ips() can reuse
 * the exact same test instead of a second, possibly diverging one.
 */
static int level1_match_rssi(const char *mac, const wifi_sta_list_t *sta_list)
{
    for (int k = 0; k < sta_list->num; ++k) {
        const uint8_t *m = sta_list->sta[k].mac;
        char text[24];
        snprintf(text, sizeof(text), "%02X:%02X:%02X:%02X:%02X:%02X",
                 m[0], m[1], m[2], m[3], m[4], m[5]);
        if (strcasecmp(text, mac) == 0) {
            return (int)sta_list->sta[k].rssi;
        }
    }
    return 127;
}

static void stats_task(void *arg)
{
    (void)arg;
    uint32_t last_chunks[MAX_CLIENTS] = {0};
    uint32_t last_skipped[MAX_CLIENTS] = {0};
    uint8_t stall_seconds[MAX_CLIENTS] = {0};
    int64_t last_peak_us = 0;
    size_t last_min_free = SIZE_MAX;

    for (;;) {
        vTaskDelay(pdMS_TO_TICKS(1000));

        int64_t avg_us = 0;
        int64_t min_us = 0;
        int64_t max_us = 0;
        uint32_t samples = 0;
        bool fresh = false;

        portENTER_CRITICAL(&s_clients_lock);
        avg_us = s_frame_stats.avg_us;
        min_us = s_frame_stats.min_us;
        max_us = s_frame_stats.max_us;
        samples = s_frame_stats.samples;
        fresh = s_frame_stats.fresh;
        s_frame_stats.fresh = false;
        portEXIT_CRITICAL(&s_clients_lock);

        if (fresh) {
            ESP_LOGI(TAG,
                     "frame delta: avg=%lld us min=%lld us max=%lld us samples=%lu",
                     (long long)avg_us,
                     (long long)min_us,
                     (long long)max_us,
                     (unsigned long)samples);
        }

        /*
         * Fetched once per report so each client line can carry its own
         * RSSI. It used to be logged separately, keyed by MAC while the
         * client lines are keyed by IP, which left correlating the two as
         * manual work on a scrolling console.
         */
        wifi_sta_list_t sta_list;
        if (esp_wifi_ap_get_sta_list(&sta_list) != ESP_OK) {
            sta_list.num = 0;
        }

        for (int i = 0; i < MAX_CLIENTS; ++i) {
            bool active = false;
            bool ready = false;
            uint32_t chunks = 0;
            uint32_t bytes = 0;
            uint32_t errs = 0;
            uint32_t skipped = 0;
            uint32_t times = 0;
            char peer[16];
            char mac[24];
            int32_t seen_sec = 0;
            int32_t seen_usec = 0;

            portENTER_CRITICAL(&s_clients_lock);
            seen_sec = s_clients[i].last_seen_sec;
            seen_usec = s_clients[i].last_seen_usec;
            active = s_clients[i].active;
            ready = s_clients[i].ready;
            chunks = s_clients[i].chunks_sent;
            bytes = s_clients[i].chunk_bytes;
            errs = s_clients[i].chunk_errors;
            skipped = s_clients[i].chunks_skipped;
            times = s_clients[i].time_msgs;
            strlcpy(peer, s_clients[i].peer, sizeof(peer));
            strlcpy(mac, s_clients[i].mac, sizeof(mac));
            portEXIT_CRITICAL(&s_clients_lock);

            if (active && ready && seen_sec != 0) {
                const int64_t seen_us =
                    (int64_t)seen_sec * 1000000LL + (int64_t)seen_usec;
                const int64_t silent_us = now_us() - seen_us;
                if (silent_us > CLIENT_SILENCE_LIMIT_US) {
                    ESP_LOGW(TAG,
                             "%s silent for %lld s, dropping it",
                             peer, (long long)(silent_us / 1000000LL));
                    mark_client_failed(&s_clients[i]);
                }
            }

            /* 127 means "no station matched": the Snapcast client is not a
             * direct child of this AP -- a node one mesh level down, or a
             * phone that reported no MAC in its Hello. */
            const int rssi = level1_match_rssi(mac, &sta_list);

            /* A reconnect resets the counter; avoid an unsigned wrap. */
            const uint32_t chunk_rate =
                (chunks >= last_chunks[i]) ? (chunks - last_chunks[i]) : chunks;
            const uint32_t skip_rate =
                (skipped >= last_skipped[i]) ? (skipped - last_skipped[i]) : skipped;

            /* See CLIENT_STALL_SECONDS. */
            if (active && ready && skip_rate > chunk_rate) {
                if (++stall_seconds[i] >= CLIENT_STALL_SECONDS) {
                    ESP_LOGW(TAG,
                             "%s: more chunks dropped than delivered for %d s "
                             "(last second %lu/%lu), closing it so it reconnects",
                             peer, CLIENT_STALL_SECONDS,
                             (unsigned long)skip_rate, (unsigned long)chunk_rate);
                    mark_client_failed(&s_clients[i]);
                    stall_seconds[i] = 0;
                }
            } else {
                stall_seconds[i] = 0;
            }

            if (active) {
                ESP_LOGI(TAG,
                         "client[%d] %s rssi=%d ready=%d chunks/s=%lu total=%lu "
                         "bytes=%lu send_errors=%lu skipped=%lu time_msgs=%lu",
                         i, peer, rssi, (int)ready,
                         (unsigned long)chunk_rate,
                         (unsigned long)chunks,
                         (unsigned long)bytes,
                         (unsigned long)errs,
                         (unsigned long)skipped,
                         (unsigned long)times);
            }
            last_chunks[i] = chunks;
            last_skipped[i] = skipped;
        }

        /*
         * Internal DRAM, every 5 s. This is the resource the Wi-Fi driver
         * takes its TX buffers from, and running it down showed up on
         * device as every client -- including a phone running stock
         * Snapcast -- going to 0 chunks/s at the same instant while the
         * capture loop kept perfect time, followed by "Could not create
         * client task". largest is what an allocation actually has to fit
         * into; min_ever is the low-water mark since boot.
         */
        const int64_t now_us = esp_timer_get_time();
        if (now_us - last_peak_us >= 5000000LL) {
            ESP_LOGI(TAG,
                     "heap: internal free=%u B largest=%u B min_ever=%u B",
                     (unsigned)heap_caps_get_free_size(MALLOC_CAP_INTERNAL),
                     (unsigned)heap_caps_get_largest_free_block(MALLOC_CAP_INTERNAL),
                     (unsigned)heap_caps_get_minimum_free_size(MALLOC_CAP_INTERNAL));

            /*
             * min_ever is a low-water mark since boot, so once it has dipped
             * it stays put and says nothing about when. A 12-minute run ended
             * with min_ever=892 B -- a hair from the state where the Wi-Fi
             * driver cannot get a TX buffer and every client stalls at once --
             * with no way to tell which moment that was. Warn on the drop
             * itself, so it lands next to the client counters of the same
             * five-second window.
             */
            const size_t min_free =
                heap_caps_get_minimum_free_size(MALLOC_CAP_INTERNAL);
            if (min_free < last_min_free) {
                if (last_min_free != SIZE_MAX) {
                    ESP_LOGW(TAG,
                             "internal heap low-water mark fell to %u B (was %u B)",
                             (unsigned)min_free, (unsigned)last_min_free);
                }
                last_min_free = min_free;
            }

            uint16_t conn_min = UINT16_MAX;
            uint16_t send_min = UINT16_MAX;
            portENTER_CRITICAL(&s_clients_lock);
            for (int i = 0; i < MAX_CLIENTS; ++i) {
                if (s_clients[i].conn_stack_free != 0U &&
                    s_clients[i].conn_stack_free < conn_min) {
                    conn_min = s_clients[i].conn_stack_free;
                }
                if (s_clients[i].tx_stack_free != 0U &&
                    s_clients[i].tx_stack_free < send_min) {
                    send_min = s_clients[i].tx_stack_free;
                }
            }
            portEXIT_CRITICAL(&s_clients_lock);

            if (conn_min != UINT16_MAX || send_min != UINT16_MAX) {
                ESP_LOGI(TAG,
                         "stack headroom: conn=%d B sender=%d B (of %d / %d)",
                         (conn_min == UINT16_MAX) ? -1 : (int)(conn_min * sizeof(StackType_t)),
                         (send_min == UINT16_MAX) ? -1 : (int)(send_min * sizeof(StackType_t)),
                         CLIENT_TASK_STACK, SENDER_TASK_STACK);
            }

            int16_t peak_left = 0;
            int16_t peak_right = 0;
            audio_i2s_take_output_peak(&peak_left, &peak_right);
            ESP_LOGI(TAG, "DSP output peak: left=%d right=%d (of 32767), I2S clock %+ld ppm",
                     (int)peak_left, (int)peak_right, (long)audio_i2s_clock_ppm());
            uint32_t tx_dry = 0;
            uint32_t rx_lost = 0;
            audio_i2s_take_dma_stats(&tx_dry, &rx_lost);
            if (tx_dry != 0U || rx_lost != 0U) {
                ESP_LOGW(TAG, "I2S DMA: TX ran dry %lu x, RX overflowed %lu x (%u ms each)",
                         (unsigned long)tx_dry, (unsigned long)rx_lost,
                         (unsigned)(AUDIO_I2S_DMA_FRAME_NUM * 1000U / AUDIO_I2S_SAMPLE_RATE));
            }
            uint32_t limited = 0;
            float limit_db = 0.0f;
            audio_i2s_take_limiter_stats(&limited, &limit_db);
            if (limited != 0U) {
                ESP_LOGW(TAG, "Output limiter: %lu samples, max -%.1f dB", (unsigned long)limited, (double)limit_db);
            }
            const float comp_db = audio_i2s_take_comp_stats();
            if (comp_db >= 0.1f) {
                ESP_LOGI(TAG, "Compressor: max -%.1f dB", (double)comp_db);
            }

            uint32_t voice_underrun = 0;
            uint32_t voice_dropped = 0;
            uint32_t voice_wait_avg = 0;
            uint32_t voice_wait_max = 0;
            audio_i2s_take_voice_stats(&voice_underrun, &voice_dropped,
                                       &voice_wait_avg, &voice_wait_max);
            if (voice_underrun != 0U || voice_dropped != 0U || voice_wait_max != 0U) {
                ESP_LOGI(TAG,
                         "voice mailbox: underrun=%lu dropped=%lu samples, "
                         "wait avg=%lu ms max=%lu ms (+%lld ms I2S)",
                         (unsigned long)voice_underrun, (unsigned long)voice_dropped,
                         (unsigned long)voice_wait_avg, (unsigned long)voice_wait_max,
                         (long long)(AUDIO_I2S_TX_LATENCY_US / 1000));
            }
            cpu_stats_log(TAG, 2);
            last_peak_us = now_us;
        }
    }
}

static void audio_task(void *arg)
{
    (void)arg;

    int64_t last_frame_start_us = 0;
    int64_t stats_start_us = esp_timer_get_time();
    int64_t delta_sum_us = 0;
    int64_t delta_min_us = INT64_MAX;
    int64_t delta_max_us = 0;
    uint32_t delta_count = 0;

    for (;;) {
        const int64_t frame_start_us = esp_timer_get_time();
        if (last_frame_start_us != 0) {
            const int64_t delta_us = frame_start_us - last_frame_start_us;
            delta_sum_us += delta_us;
            if (delta_us < delta_min_us) delta_min_us = delta_us;
            if (delta_us > delta_max_us) delta_max_us = delta_us;
            ++delta_count;
        }
        last_frame_start_us = frame_start_us;

        audio_opus_packet_t packet;
        const esp_err_t audio_result = audio_opus_get_packet(&packet);
        if (audio_result == ESP_OK) {
            client_t *clients[MAX_CLIENTS];
            int count = 0;

            portENTER_CRITICAL(&s_clients_lock);
            for (int i = 0; i < MAX_CLIENTS; ++i) {
                if (s_clients[i].active && s_clients[i].ready) {
                    clients[count++] = &s_clients[i];
                }
            }
            portEXIT_CRITICAL(&s_clients_lock);

            /*
             * Fill one pool slot and hand out references. Everything here is
             * bounded work -- a memcpy plus one queue post per client -- so
             * the capture cadence no longer depends on how many clients are
             * connected, nor on how fast any of them drains its socket.
             */
            if (packet.size <= AUDIO_MAX_OPUS_PACKET) {
                const uint16_t slot_index = (uint16_t)s_chunk_write;
                chunk_slot_t *slot = &s_chunk_pool[slot_index];

                slot->size = (uint32_t)packet.size;
                slot->timestamp_us = packet.timestamp_us;
                memcpy(slot->data, packet.data, packet.size);
                /* Published last: a sender comparing sequences must never
                 * see the new number in front of the new payload. */
                slot->sequence = ++s_chunk_sequence;
                s_chunk_write = (s_chunk_write + 1U) % CHUNK_POOL_SIZE;

                const tx_item_t item = {
                    .slot = slot_index,
                    .sequence = slot->sequence,
                };

                for (int i = 0; i < count; ++i) {
                    if (clients[i]->tx_queue == NULL) {
                        continue;
                    }
                    if (xQueueSend(clients[i]->tx_queue, &item, 0) != pdTRUE) {
                        /* Queue full: this client is behind. Drop its oldest
                         * pending chunk rather than the newest -- stale audio
                         * is the least useful thing to keep. */
                        tx_item_t dropped;
                        if (xQueueReceive(clients[i]->tx_queue, &dropped, 0) == pdTRUE) {
                            portENTER_CRITICAL(&s_clients_lock);
                            clients[i]->chunks_skipped++;
                            portEXIT_CRITICAL(&s_clients_lock);
                        }
                        (void)xQueueSend(clients[i]->tx_queue, &item, 0);
                    }
                }
            }
        } else if (audio_result != ESP_ERR_TIMEOUT) {
            /* A timeout means no I2S clock; audio_i2s.c reports that. */
            ESP_LOGE(TAG, "Audio frame failed: %s", esp_err_to_name(audio_result));
        }

        const int64_t stats_now_us = esp_timer_get_time();
        if (delta_count > 0U && stats_now_us - stats_start_us >= 1000000LL) {
            /* Publish only -- printing happens in stats_task. */
            portENTER_CRITICAL(&s_clients_lock);
            s_frame_stats.avg_us = delta_sum_us / (int64_t)delta_count;
            s_frame_stats.min_us = delta_min_us;
            s_frame_stats.max_us = delta_max_us;
            s_frame_stats.samples = delta_count;
            s_frame_stats.fresh = true;
            portEXIT_CRITICAL(&s_clients_lock);

            stats_start_us = stats_now_us;
            delta_sum_us = 0;
            delta_min_us = INT64_MAX;
            delta_max_us = 0;
            delta_count = 0;
        }
    }
}

static void server_task(void *arg)
{
    (void)arg;

    const int listen_fd = socket(AF_INET, SOCK_STREAM, IPPROTO_IP);
    if (listen_fd < 0) {
        ESP_LOGE(TAG, "socket failed errno=%d", errno);
        s_server_task = NULL;
        vTaskDelete(NULL);
        return;
    }

    int reuse = 1;
    if (setsockopt(listen_fd,
                   SOL_SOCKET,
                   SO_REUSEADDR,
                   &reuse,
                   sizeof(reuse)) < 0) {
        ESP_LOGW(TAG, "setsockopt failed errno=%d", errno);
    }

    const struct sockaddr_in addr = {
        .sin_family = AF_INET,
        .sin_port = htons(SNAPSERVER_PORT),
        .sin_addr.s_addr = htonl(INADDR_ANY),
    };

    if (bind(listen_fd, (const struct sockaddr *)&addr, sizeof(addr)) < 0) {
        ESP_LOGE(TAG, "bind failed errno=%d", errno);
        close(listen_fd);
        s_server_task = NULL;
        vTaskDelete(NULL);
        return;
    }

    if (listen(listen_fd, MAX_CLIENTS) < 0) {
        ESP_LOGE(TAG, "listen failed errno=%d", errno);
        close(listen_fd);
        s_server_task = NULL;
        vTaskDelete(NULL);
        return;
    }

    ESP_LOGI(TAG, "Listening on TCP port %d", SNAPSERVER_PORT);

    for (;;) {
        struct sockaddr_in peer;
        socklen_t peer_len = sizeof(peer);
        const int fd = accept(listen_fd,
                              (struct sockaddr *)&peer,
                              &peer_len);
        if (fd < 0) {
            if (errno != EINTR) {
                ESP_LOGW(TAG, "accept failed errno=%d", errno);
            }
            continue;
        }

        char peer_ip[16] = {0};
        inet_ntoa_r(peer.sin_addr, peer_ip, sizeof(peer_ip) - 1);

        const struct timeval send_timeout = {
            .tv_sec = (time_t)(CLIENT_SEND_TIMEOUT_US / 1000000),
            .tv_usec = (suseconds_t)(CLIENT_SEND_TIMEOUT_US % 1000000),
        };
        if (setsockopt(fd,
                       SOL_SOCKET,
                       SO_SNDTIMEO,
                       &send_timeout,
                       sizeof(send_timeout)) < 0) {
            ESP_LOGW(TAG,
                     "Could not set client send timeout, errno=%d",
                     errno);
        }

        const struct timeval recv_timeout = {
            .tv_sec = (time_t)(CLIENT_RECV_TIMEOUT_US / 1000000),
            .tv_usec = (suseconds_t)(CLIENT_RECV_TIMEOUT_US % 1000000),
        };
        if (setsockopt(fd,
                       SOL_SOCKET,
                       SO_RCVTIMEO,
                       &recv_timeout,
                       sizeof(recv_timeout)) < 0) {
            ESP_LOGW(TAG,
                     "Could not set client receive timeout, errno=%d",
                     errno);
        }

        int keepalive = 1;
        if (setsockopt(fd,
                       SOL_SOCKET,
                       SO_KEEPALIVE,
                       &keepalive,
                       sizeof(keepalive)) < 0) {
            ESP_LOGW(TAG, "Could not enable TCP keepalive, errno=%d", errno);
        }
        int keepalive_idle = CLIENT_KEEPALIVE_IDLE_SEC;
        setsockopt(fd, IPPROTO_TCP, TCP_KEEPIDLE,
                  &keepalive_idle, sizeof(keepalive_idle));
        int keepalive_intvl = CLIENT_KEEPALIVE_INTVL_SEC;
        setsockopt(fd, IPPROTO_TCP, TCP_KEEPINTVL,
                  &keepalive_intvl, sizeof(keepalive_intvl));
        int keepalive_cnt = CLIENT_KEEPALIVE_COUNT;
        setsockopt(fd, IPPROTO_TCP, TCP_KEEPCNT,
                  &keepalive_cnt, sizeof(keepalive_cnt));

        int nodelay = 1;
        if (setsockopt(fd,
                       IPPROTO_TCP,
                       TCP_NODELAY,
                       &nodelay,
                       sizeof(nodelay)) < 0) {
            ESP_LOGW(TAG, "Could not set TCP_NODELAY, errno=%d", errno);
        }

        int slot = -1;
        portENTER_CRITICAL(&s_clients_lock);
        for (int i = 0; i < MAX_CLIENTS; ++i) {
            if (!s_clients[i].active) {
                s_clients[i].fd = fd;
                s_clients[i].active = true;
                s_clients[i].ready = false;
                s_clients[i].next_id = 1;
                s_clients[i].chunks_sent = 0;
                s_clients[i].chunk_bytes = 0;
                s_clients[i].chunk_errors = 0;
                s_clients[i].chunks_skipped = 0;
                s_clients[i].time_msgs = 0;
                s_clients[i].instance = 1;
                s_clients[i].protocol_ver = SNAP_PROTOCOL_VER;
                s_clients[i].volume_percent = 100;
                s_clients[i].muted = false;
                s_clients[i].voice_muted_sent = false;
                s_clients[i].announcement_sent = false;
                s_clients[i].is_snapmesh = false;
                s_clients[i].mesh_level = 0;
                s_clients[i].latency_ms = 0;
                s_clients[i].id[0] = '\0';
                s_clients[i].name[0] = '\0';
                s_clients[i].hostname[0] = '\0';
                s_clients[i].mac[0] = '\0';
                s_clients[i].arch[0] = '\0';
                s_clients[i].os[0] = '\0';
                s_clients[i].version[0] = '\0';
                strlcpy(s_clients[i].peer,
                       peer_ip,
                       sizeof(s_clients[i].peer));
                slot = i;
                break;
            }
        }
        portEXIT_CRITICAL(&s_clients_lock);

        if (slot >= 0) {
            /*
             * Drop references left over from whoever held this slot before,
             * so they cannot be sent to the new occupant. Deliberately
             * outside the critical section: FreeRTOS queue calls take their
             * own locks and must never run with interrupts disabled. Safe
             * here because the sender only transmits once `ready` is set,
             * which happens after the handshake well below.
             */
            xQueueReset(s_clients[slot].tx_queue);
        }

        if (slot < 0) {
            ESP_LOGW(TAG, "Rejecting client: all slots occupied");
            shutdown(fd, SHUT_RDWR);
            close(fd);
            continue;
        }

        ESP_LOGI(TAG,
                 "Client connected slot=%d ip=%s fd=%d",
                 slot,
                 s_clients[slot].peer,
                 fd);

        /* The slot's task already exists and is parked; wake it. */
        xTaskNotifyGive(s_clients[slot].task);
    }
}

/* ------------------------------------------------------------------ */
/* Public API for the control server                                  */
/* ------------------------------------------------------------------ */

/*
 * Change detection for the control server, which polls it about once a
 * second per connection. It used to build a full snapshot -- every string of
 * every client -- and throw all of it away except the ids. Hashing in place
 * under a per-client lock costs a fraction of that and touches no memory
 * outside this file.
 */
uint32_t snapserver_client_set_hash(void)
{
    uint32_t hash = 2166136261U;

    for (int i = 0; i < MAX_CLIENTS; ++i) {
        portENTER_CRITICAL(&s_clients_lock);
        const bool counts = s_clients[i].active && s_clients[i].ready;
        if (counts) {
            for (const unsigned char *p = (const unsigned char *)s_clients[i].id;
                 *p != '\0'; ++p) {
                hash ^= *p;
                hash *= 16777619U;
            }
            /*
             * Settings too, so a change made on one controller -- the web
             * device list, another app -- reaches the others as
             * Server.OnUpdate instead of only on their next GetStatus.
             */
            for (const unsigned char *p = (const unsigned char *)s_clients[i].name;
                 *p != '\0'; ++p) {
                hash ^= *p;
                hash *= 16777619U;
            }
            const uint32_t settings[] = {
                (uint32_t)s_clients[i].volume_percent,
                s_clients[i].muted ? 1U : 0U,
                (uint32_t)s_clients[i].latency_ms,
                s_clients[i].mesh_level,
            };
            for (size_t k = 0; k < sizeof(settings) / sizeof(settings[0]); ++k) {
                hash ^= settings[k];
                hash *= 16777619U;
            }
        }
        portEXIT_CRITICAL(&s_clients_lock);

        hash ^= counts ? 1U : 0U;
        hash *= 16777619U;
    }

    return hash;
}

size_t snapserver_get_clients(snapserver_client_info_t *out,
                              size_t max_clients)
{
    if (out == NULL || max_clients == 0U) {
        return 0;
    }

    size_t count = 0;

    /* For the hop count of clients that do not report their level. */
    wifi_sta_list_t sta_list;
    if (esp_wifi_ap_get_sta_list(&sta_list) != ESP_OK) {
        sta_list.num = 0;
    }

    /*
     * Locked per client, not once around the loop.
     *
     * s_clients_lock is a cross-core spinlock, so holding it runs with
     * interrupts off and spins the other core -- and audio_task takes the
     * same lock every 20 ms frame. Copying ten clients at ~330 B each in one
     * stretch was enough to show up in the capture cadence: a client joining
     * pushed frame delta from 20000 to 21089 us for a whole second while
     * every client dropped from 53 to 50 chunks/s. A snapshot that is not
     * atomic across clients costs a status display nothing.
     */
    for (int i = 0; i < MAX_CLIENTS && count < max_clients; ++i) {
        portENTER_CRITICAL(&s_clients_lock);
        if (!s_clients[i].active || !s_clients[i].ready) {
            portEXIT_CRITICAL(&s_clients_lock);
            continue;
        }

        snapserver_client_info_t *dst = &out[count];
        memset(dst, 0, sizeof(*dst));

        strlcpy(dst->id, s_clients[i].id, sizeof(dst->id));
        strlcpy(dst->name, s_clients[i].name, sizeof(dst->name));
        strlcpy(dst->hostname, s_clients[i].hostname, sizeof(dst->hostname));
        strlcpy(dst->mac, s_clients[i].mac, sizeof(dst->mac));
        strlcpy(dst->arch, s_clients[i].arch, sizeof(dst->arch));
        strlcpy(dst->os, s_clients[i].os, sizeof(dst->os));
        strlcpy(dst->version, s_clients[i].version, sizeof(dst->version));
        strlcpy(dst->ip, s_clients[i].peer, sizeof(dst->ip));

        dst->instance = s_clients[i].instance;
        dst->protocol_ver = s_clients[i].protocol_ver;
        dst->connected = true;
        dst->volume_percent = s_clients[i].volume_percent;
        dst->muted = s_clients[i].muted;
        dst->latency_ms = s_clients[i].latency_ms;
        dst->is_snapmesh = s_clients[i].is_snapmesh;
        dst->hops = (s_clients[i].mesh_level >= 2U) ? (int32_t)s_clients[i].mesh_level - 1 : -1;
        dst->last_seen_sec = s_clients[i].last_seen_sec;
        dst->last_seen_usec = s_clients[i].last_seen_usec;
        portEXIT_CRITICAL(&s_clients_lock);

        ++count;
    }

    /* An id is mandatory for the controller; fall back to the peer address. */
    for (size_t i = 0; i < count; ++i) {
        /* A foreign client (a phone, a PC) says nothing about its level,
         * but one on this node's own AP is one hop away all the same. */
        if (out[i].hops < 0 && level1_match_rssi(out[i].mac, &sta_list) != 127) {
            out[i].hops = 1;
        }
        if (out[i].id[0] == '\0') {
            strlcpy(out[i].id, out[i].ip, sizeof(out[i].id));
        }
        if (out[i].name[0] == '\0') {
            strlcpy(out[i].name, out[i].id, sizeof(out[i].name));
        }
        if (out[i].hostname[0] == '\0') {
            strlcpy(out[i].hostname, out[i].ip, sizeof(out[i].hostname));
        }
    }

    return count;
}

size_t snapserver_get_level1_client_ips(char ips[][16], size_t max_ips)
{
    if (ips == NULL || max_ips == 0U) {
        return 0;
    }

    wifi_sta_list_t sta_list;
    if (esp_wifi_ap_get_sta_list(&sta_list) != ESP_OK) {
        sta_list.num = 0;
    }

    size_t count = 0;
    for (int i = 0; i < MAX_CLIENTS && count < max_ips; ++i) {
        portENTER_CRITICAL(&s_clients_lock);
        const bool active = s_clients[i].active && s_clients[i].ready;
        char peer[16];
        char mac[24];
        strlcpy(peer, s_clients[i].peer, sizeof(peer));
        strlcpy(mac, s_clients[i].mac, sizeof(mac));
        portEXIT_CRITICAL(&s_clients_lock);

        if (!active || level1_match_rssi(mac, &sta_list) == 127) {
            continue;
        }

        strlcpy(ips[count], peer, sizeof(ips[count]));
        ++count;
    }

    return count;
}

void snapserver_set_announcement(bool active)
{
    s_announcement_active = active;
}

void snapserver_refresh_announcement(void)
{
    const bool active = s_announcement_active;

    for (int i = 0; i < MAX_CLIENTS; ++i) {
        portENTER_CRITICAL(&s_clients_lock);
        const bool live = s_clients[i].active && s_clients[i].ready;
        const bool is_snapmesh = s_clients[i].is_snapmesh;
        const bool muted_sent = s_clients[i].voice_muted_sent;
        const bool announcement_sent = s_clients[i].announcement_sent;
        portEXIT_CRITICAL(&s_clients_lock);

        if (!live) {
            continue;
        }

        /* Our clients act on the flag, the others on the mute; push to
         * whichever of the two has gone stale. */
        const bool want_muted = active && !is_snapmesh;
        if (want_muted != muted_sent || active != announcement_sent) {
            (void)send_server_settings(&s_clients[i], 0);
        }
    }
}

/*
 * Finds a client by id and applies a mutation. Volume and latency changes
 * only update the bookkeeping; they take effect for the client on its next
 * ServerSettings message.
 */
static client_t *find_client_by_id_unsafe(const char *id)
{
    for (int i = 0; i < MAX_CLIENTS; ++i) {
        if (s_clients[i].active &&
            strncmp(s_clients[i].id, id, sizeof(s_clients[i].id)) == 0) {
            return &s_clients[i];
        }
    }
    return NULL;
}

/*
 * Writes a client's current volume, mute and latency to client_store, so a
 * reconnect picks them up again. name is the new name when this follows a
 * rename, NULL to keep whatever name is stored -- the name the client
 * reports itself is not worth storing, only one somebody chose. Called
 * from the JSON-RPC and HTTP tasks, which have the internal-RAM stack a
 * flash write needs.
 */
static void remember_settings(const char *id, const char *name)
{
    client_store_entry_t entry;
    if (!client_store_get(id, &entry)) {
        entry.name[0] = '\0';
    }

    bool found = false;
    portENTER_CRITICAL(&s_clients_lock);
    const client_t *client = find_client_by_id_unsafe(id);
    if (client != NULL) {
        entry.volume_percent = client->volume_percent;
        entry.muted = client->muted;
        entry.latency_ms = client->latency_ms;
        found = true;
    }
    portEXIT_CRITICAL(&s_clients_lock);

    if (!found) {
        return;
    }
    if (name != NULL) {
        strlcpy(entry.name, name, sizeof(entry.name));
    }
    client_store_put(id, &entry);
}

bool snapserver_set_client_volume(const char *id,
                                  int32_t percent,
                                  bool muted)
{
    if (id == NULL || id[0] == '\0') {
        return false;
    }

    if (percent < 0) {
        percent = 0;
    } else if (percent > 100) {
        percent = 100;
    }

    bool found = false;
    client_t *client = NULL;

    portENTER_CRITICAL(&s_clients_lock);
    client = find_client_by_id_unsafe(id);
    if (client != NULL) {
        client->volume_percent = percent;
        client->muted = muted;
        found = true;
    }
    portEXIT_CRITICAL(&s_clients_lock);

    if (found) {
        remember_settings(id, NULL);
        ESP_LOGI(TAG,
                 "Volume for %s set to %ld%% (muted=%s)",
                 id,
                 (long)percent,
                 muted ? "true" : "false");
        /* Push the new setting immediately. */
        (void)send_server_settings(client, 0);
    }

    return found;
}

bool snapserver_set_client_latency(const char *id, int32_t latency_ms)
{
    if (id == NULL || id[0] == '\0') {
        return false;
    }

    bool found = false;
    client_t *client = NULL;

    portENTER_CRITICAL(&s_clients_lock);
    client = find_client_by_id_unsafe(id);
    if (client != NULL) {
        client->latency_ms = latency_ms;
        found = true;
    }
    portEXIT_CRITICAL(&s_clients_lock);

    if (found) {
        remember_settings(id, NULL);
        ESP_LOGI(TAG, "Latency for %s set to %ld ms", id, (long)latency_ms);
        (void)send_server_settings(client, 0);
    }

    return found;
}

bool snapserver_set_client_name(const char *id, const char *name)
{
    if (id == NULL || id[0] == '\0' || name == NULL) {
        return false;
    }

    bool found = false;

    portENTER_CRITICAL(&s_clients_lock);
    client_t *client = find_client_by_id_unsafe(id);
    if (client != NULL) {
        strlcpy(client->name, name, sizeof(client->name));
        found = true;
    }
    portEXIT_CRITICAL(&s_clients_lock);

    if (found) {
        remember_settings(id, name);
        ESP_LOGI(TAG, "Name for %s set to '%s'", id, name);
    }

    return found;
}

/*
 * A static queue split across two memories: the StaticQueue_t (which holds
 * the queue's spinlock) from internal RAM, the item storage from PSRAM.
 * xQueueCreateWithCaps() would put both in the same place, and a spinlock
 * in external memory is not something to rely on. The storage is where the
 * size is -- CLIENT_TX_QUEUE_DEPTH items per client -- so that is the part
 * worth keeping out of internal DRAM.
 */
static QueueHandle_t create_tx_queue(client_t *client)
{
    client->tx_queue_ctrl = heap_caps_malloc(sizeof(StaticQueue_t),
                                             MALLOC_CAP_INTERNAL | MALLOC_CAP_8BIT);
    client->tx_queue_storage = heap_caps_malloc(CLIENT_TX_QUEUE_DEPTH * sizeof(tx_item_t),
                                                MALLOC_CAP_SPIRAM | MALLOC_CAP_8BIT);
    if (client->tx_queue_storage == NULL) {
        client->tx_queue_storage = heap_caps_malloc(CLIENT_TX_QUEUE_DEPTH * sizeof(tx_item_t),
                                                    MALLOC_CAP_8BIT);
    }
    if (client->tx_queue_ctrl == NULL || client->tx_queue_storage == NULL) {
        return NULL;
    }
    return xQueueCreateStatic(CLIENT_TX_QUEUE_DEPTH,
                              sizeof(tx_item_t),
                              client->tx_queue_storage,
                              client->tx_queue_ctrl);
}

esp_err_t snapserver_start(void)
{
    if (s_started) {
        return ESP_OK;
    }

    /* Before the first Hello can arrive; see client_store.h for why the
     * entries have to be in RAM by then. */
    (void)client_store_init();

    {
        device_config_t cfg;
        device_config_get(&cfg);
        s_max_chunk_age_us = max_chunk_age_us(cfg.buffer_ms);
        ESP_LOGI(TAG, "Per-client backlog: up to %ld ms before chunks are dropped",
                 (long)(s_max_chunk_age_us / 1000));
    }

    {
        int32_t sec = 0;
        int32_t usec = 0;
        now_ts(&sec, &usec);
        ESP_LOGI(TAG,
                 "Server time base: %ld.%06ld (wall clock)",
                 (long)sec,
                 (long)usec);
    }

    s_chunk_pool = heap_caps_malloc(sizeof(chunk_slot_t) * CHUNK_POOL_SIZE,
                                    MALLOC_CAP_SPIRAM | MALLOC_CAP_8BIT);
    if (s_chunk_pool == NULL) {
        s_chunk_pool = heap_caps_malloc(sizeof(chunk_slot_t) * CHUNK_POOL_SIZE,
                                        MALLOC_CAP_8BIT);
    }
    if (s_chunk_pool == NULL) {
        ESP_LOGE(TAG, "No memory for the %d-slot chunk pool", CHUNK_POOL_SIZE);
        return ESP_ERR_NO_MEM;
    }
    memset(s_chunk_pool, 0, sizeof(chunk_slot_t) * CHUNK_POOL_SIZE);
    s_chunk_write = 0;
    s_chunk_sequence = 0;

    s_remote_mutex = xSemaphoreCreateMutex();
    s_remote_done = xSemaphoreCreateBinary();
    if (s_remote_mutex == NULL || s_remote_done == NULL) {
        ESP_LOGE(TAG, "No memory for the config request semaphores");
        return ESP_ERR_NO_MEM;
    }

    memset(s_clients, 0, sizeof(s_clients));
    for (int i = 0; i < MAX_CLIENTS; ++i) {
        s_clients[i].fd = -1;
        s_clients[i].volume_percent = 100;
        s_clients[i].instance = 1;
        s_clients[i].protocol_ver = SNAP_PROTOCOL_VER;
        s_clients[i].send_mutex = xSemaphoreCreateMutex();
        s_clients[i].tx_queue = create_tx_queue(&s_clients[i]);
        s_clients[i].tx_payload = heap_caps_malloc(sizeof(snap_base_t) + 12U + AUDIO_MAX_OPUS_PACKET,
                                                   MALLOC_CAP_SPIRAM | MALLOC_CAP_8BIT);
        if (s_clients[i].tx_payload == NULL) {
            s_clients[i].tx_payload = heap_caps_malloc(sizeof(snap_base_t) + 12U + AUDIO_MAX_OPUS_PACKET,
                                                       MALLOC_CAP_8BIT);
        }

        char task_name[16];
        snprintf(task_name, sizeof(task_name), "snapsend%d", i);
        bool sender_ok =
            s_clients[i].send_mutex != NULL && s_clients[i].tx_queue != NULL &&
            s_clients[i].tx_payload != NULL &&
            xTaskCreatePinnedToCoreWithCaps(sender_task,
                                            task_name,
                                            SENDER_TASK_STACK,
                                            &s_clients[i],
                                            SENDER_TASK_PRIORITY,
                                            &s_clients[i].tx_task,
                                            0,
                                            TASK_STACK_CAPS) == pdPASS;

        if (sender_ok) {
            snprintf(task_name, sizeof(task_name), "snapconn%d", i);
            sender_ok = xTaskCreatePinnedToCoreWithCaps(client_task,
                                                        task_name,
                                                        CLIENT_TASK_STACK,
                                                        &s_clients[i],
                                                        5,
                                                        &s_clients[i].task,
                                                        0,
                                                        TASK_STACK_CAPS) == pdPASS;
        }

        if (!sender_ok) {
            ESP_LOGE(TAG, "Could not set up sender for client slot %d", i);
            for (int j = 0; j <= i; ++j) {
                if (s_clients[j].task != NULL) {
                    vTaskDeleteWithCaps(s_clients[j].task);
                    s_clients[j].task = NULL;
                }
                if (s_clients[j].tx_task != NULL) {
                    vTaskDeleteWithCaps(s_clients[j].tx_task);
                    s_clients[j].tx_task = NULL;
                }
                if (s_clients[j].tx_queue != NULL) {
                    vQueueDelete(s_clients[j].tx_queue);
                    s_clients[j].tx_queue = NULL;
                }
                heap_caps_free(s_clients[j].tx_queue_ctrl);
                s_clients[j].tx_queue_ctrl = NULL;
                heap_caps_free(s_clients[j].tx_queue_storage);
                s_clients[j].tx_queue_storage = NULL;
                free(s_clients[j].tx_payload);
                s_clients[j].tx_payload = NULL;
                if (s_clients[j].send_mutex != NULL) {
                    vSemaphoreDelete(s_clients[j].send_mutex);
                    s_clients[j].send_mutex = NULL;
                }
            }
            return ESP_ERR_NO_MEM;
        }
    }

    if (xTaskCreatePinnedToCore(server_task,
                                "snapserver",
                                SERVER_TASK_STACK,
                                NULL,
                                5,
                                &s_server_task,
                                0) != pdPASS) {
        goto fail;
    }

    if (xTaskCreatePinnedToCore(stats_task,
                                "snapstats",
                                STATS_TASK_STACK,
                                NULL,
                                STATS_TASK_PRIORITY,
                                NULL,
                                0) != pdPASS) {
        vTaskDelete(s_server_task);
        s_server_task = NULL;
        goto fail;
    }

    if (xTaskCreatePinnedToCore(audio_task,
                                "opus_audio",
                                AUDIO_TASK_STACK,
                                NULL,
                                6,
                                &s_audio_task,
                                1) != pdPASS) {
        vTaskDelete(s_server_task);
        s_server_task = NULL;
        goto fail;
    }

    s_started = true;

    /*
     * The fan-out added MAX_CLIENTS sender tasks; if internal RAM ran short
     * here, the next task creation to fail would be the JSON-RPC control
     * connection, which looks like "clients no longer listed" rather than
     * like an out-of-memory error. Worth seeing in the log.
     */
    ESP_LOGI(TAG,
             "Free heap after start: %u B internal, %u B largest block",
             (unsigned)heap_caps_get_free_size(MALLOC_CAP_INTERNAL | MALLOC_CAP_8BIT),
             (unsigned)heap_caps_get_largest_free_block(MALLOC_CAP_INTERNAL | MALLOC_CAP_8BIT));

    return ESP_OK;

fail:
    for (int i = 0; i < MAX_CLIENTS; ++i) {
        if (s_clients[i].send_mutex != NULL) {
            vSemaphoreDelete(s_clients[i].send_mutex);
            s_clients[i].send_mutex = NULL;
        }
    }
    return ESP_ERR_NO_MEM;
}

esp_err_t snapserver_remote_request(const char *id,
                                    const char *json,
                                    char **reply,
                                    uint32_t timeout_ms)
{
    *reply = NULL;
    if (!s_started || id == NULL || json == NULL) {
        return ESP_ERR_INVALID_STATE;
    }
    const size_t json_len = strlen(json);
    if (json_len == 0U || json_len > RX_MAX - sizeof(uint32_t)) {
        return ESP_ERR_INVALID_SIZE;
    }

    if (xSemaphoreTake(s_remote_mutex, pdMS_TO_TICKS(timeout_ms)) != pdTRUE) {
        return ESP_ERR_TIMEOUT;
    }

    /* Same framing as ServerSettings: length, then the JSON. */
    const uint32_t len = (uint32_t)json_len;
    uint8_t *payload = malloc(sizeof(len) + json_len);
    if (payload == NULL) {
        xSemaphoreGive(s_remote_mutex);
        return ESP_ERR_NO_MEM;
    }
    memcpy(payload, &len, sizeof(len));
    memcpy(payload + sizeof(len), json, json_len);

    /* A give from an answer that came just after the previous request had
     * already given up would otherwise end this wait at once. */
    (void)xSemaphoreTake(s_remote_done, 0);

    client_t *client = NULL;
    uint16_t request_id = 0;
    portENTER_CRITICAL(&s_clients_lock);
    for (int i = 0; i < MAX_CLIENTS; ++i) {
        if (s_clients[i].active && s_clients[i].ready && s_clients[i].is_snapmesh &&
            strcmp(s_clients[i].id, id) == 0) {
            client = &s_clients[i];
            if (++s_remote_next_id == 0U) {
                s_remote_next_id = 1U;
            }
            request_id = s_remote_next_id;
            s_remote.slot = i;
            s_remote.id = request_id;
            s_remote.payload = NULL;
            s_remote.size = 0;
            s_remote.failed = false;
            break;
        }
    }
    portEXIT_CRITICAL(&s_clients_lock);

    if (client == NULL) {
        free(payload);
        xSemaphoreGive(s_remote_mutex);
        return ESP_ERR_NOT_FOUND;
    }

    esp_err_t result = ESP_OK;
    if (client_send_msg(client, SNAP_TYPE_SNAPMESH_CONFIG, request_id, 0,
                        payload, (uint32_t)(sizeof(len) + json_len), 0, 0, true) != 0) {
        result = ESP_FAIL;
    } else if (xSemaphoreTake(s_remote_done, pdMS_TO_TICKS(timeout_ms)) != pdTRUE) {
        result = ESP_ERR_TIMEOUT;
    }
    free(payload);

    portENTER_CRITICAL(&s_clients_lock);
    uint8_t *answer = s_remote.payload;
    const uint32_t answer_size = s_remote.size;
    const bool failed = s_remote.failed;
    s_remote.slot = -1;
    s_remote.payload = NULL;
    s_remote.size = 0;
    s_remote.failed = false;
    portEXIT_CRITICAL(&s_clients_lock);

    if (result == ESP_OK && (failed || answer == NULL)) {
        result = ESP_ERR_INVALID_STATE;
    }
    if (result == ESP_OK) {
        uint32_t answer_len = 0;
        if (answer_size < sizeof(answer_len)) {
            result = ESP_ERR_INVALID_RESPONSE;
        } else {
            memcpy(&answer_len, answer, sizeof(answer_len));
            if (answer_len > answer_size - sizeof(answer_len)) {
                result = ESP_ERR_INVALID_RESPONSE;
            }
        }
        if (result == ESP_OK) {
            *reply = malloc((size_t)answer_len + 1U);
            if (*reply == NULL) {
                result = ESP_ERR_NO_MEM;
            } else {
                memcpy(*reply, answer + sizeof(answer_len), answer_len);
                (*reply)[answer_len] = '\0';
            }
        }
    }
    free(answer);

    xSemaphoreGive(s_remote_mutex);
    return result;
}

size_t snapserver_client_count(size_t *own)
{
    size_t total = 0;
    size_t ours = 0;
    portENTER_CRITICAL(&s_clients_lock);
    for (int i = 0; i < MAX_CLIENTS; ++i) {
        if (s_clients[i].active && s_clients[i].ready) {
            ++total;
            if (s_clients[i].is_snapmesh) {
                ++ours;
            }
        }
    }
    portEXIT_CRITICAL(&s_clients_lock);
    if (own != NULL) {
        *own = ours;
    }
    return total;
}
