pillepalle127/ESP32S3_Mesh_Snapserver/android/SnapAnnounce/app/src/main/java/com/pillepalle/snapannounce/VoiceAnnounceService.kt

package com.pillepalle.snapannounce

import android.annotation.SuppressLint
import android.app.Notification
import android.app.NotificationChannel
import android.app.NotificationManager
import android.app.PendingIntent
import android.app.Service
import android.content.Intent
import android.content.pm.ServiceInfo
import android.media.AudioFormat
import android.media.AudioRecord
import android.media.AudioTimestamp
import android.media.MediaRecorder
import android.net.ConnectivityManager
import android.net.Network
import android.net.NetworkCapabilities
import android.net.NetworkRequest
import android.net.wifi.WifiManager
import android.os.Build
import android.os.Binder
import android.os.IBinder
import android.os.Process
import android.util.Log
import androidx.core.app.NotificationCompat
import androidx.core.app.ServiceCompat
import kotlinx.coroutines.CoroutineScope
import kotlinx.coroutines.Dispatchers
import kotlinx.coroutines.Job
import kotlinx.coroutines.NonCancellable
import kotlinx.coroutines.SupervisorJob
import kotlinx.coroutines.cancel
import kotlinx.coroutines.delay
import kotlinx.coroutines.flow.MutableStateFlow
import kotlinx.coroutines.flow.StateFlow
import kotlinx.coroutines.flow.asStateFlow
import kotlinx.coroutines.flow.update
import kotlinx.coroutines.isActive
import kotlinx.coroutines.launch
import kotlinx.coroutines.withContext
import java.io.IOException
import java.net.DatagramPacket
import java.net.DatagramSocket
import kotlin.math.log10

enum class AnnounceState { IDLE, CONNECTING, ON_AIR, ERROR }

data class UiState(
    val state: AnnounceState = AnnounceState.IDLE,
    val elapsedSeconds: Int = 0,
    val message: String? = null,
    /** The announcement failed because the server could not be reached. */
    val serverNotFound: Boolean = false,
)

/**
 * Captures the microphone and streams it to the ESP32 server as long as an
 * announcement is armed.
 *
 * A foreground service rather than work inside the Activity: the button is
 * latching, not push-to-talk, so an announcement is expected to outlive a
 * locked screen or a quick switch to another app.
 *
 * One coroutine runs a whole announcement top to bottom -- connect, arm,
 * capture until asked to stop, disarm, clean up. Everything that wants an
 * announcement to end (the button, the notification action, a lost Wi-Fi
 * network) only flips [capturing] and records why; that coroutine notices
 * within one 10 ms read and does the disarm and cleanup itself. That keeps
 * Voice.Stop on the one code path that also owns the control connection,
 * instead of racing a second coroutine for it.
 *
 * Wire format towards the firmware (voice_announce.c): one UDP datagram per
 * Opus packet (normally 20 ms), a 4-byte little-endian sequence number
 * followed by the raw Opus packet, 16 kHz mono speech.
 */
class VoiceAnnounceService : Service() {

    inner class LocalBinder : Binder() {
        fun service(): VoiceAnnounceService = this@VoiceAnnounceService
    }

    private val binder = LocalBinder()
    private val scope = CoroutineScope(SupervisorJob() + Dispatchers.Default)

    private val _uiState = MutableStateFlow(UiState())
    val uiState: StateFlow<UiState> = _uiState.asStateFlow()

    private lateinit var settings: SettingsStore
    private lateinit var connectivity: ConnectivityManager

    private var announceJob: Job? = null
    private var networkCallback: ConnectivityManager.NetworkCallback? = null
    private lateinit var wifi: WifiManager
    private var wifiLock: WifiManager.WifiLock? = null

    @Volatile private var capturing = false
    @Volatile private var stopReason: String? = null

    override fun onCreate() {
        super.onCreate()
        settings = SettingsStore(this)
        connectivity = getSystemService(ConnectivityManager::class.java)
        wifi = getSystemService(WifiManager::class.java)
        createNotificationChannel()
    }

    /**
     * Keeps the Wi-Fi radio awake and on the low-latency path while an
     * announcement runs.
     *
     * Without this, Android is free to put the radio into power save, which
     * parks outgoing packets until the next beacon and delivers them in
     * bursts -- exactly the kind of delay this path cannot buffer away.
     * WIFI_MODE_FULL_LOW_LATENCY (Android 10+) additionally asks the driver
     * to favour latency over throughput; it costs battery and is therefore
     * held only for the duration of an announcement.
     */
    private fun acquireWifiLock() {
        if (wifiLock != null) {
            return
        }
        val mode = if (Build.VERSION.SDK_INT >= Build.VERSION_CODES.Q) {
            WifiManager.WIFI_MODE_FULL_LOW_LATENCY
        } else {
            @Suppress("DEPRECATION")
            WifiManager.WIFI_MODE_FULL_HIGH_PERF
        }
        wifiLock = wifi.createWifiLock(mode, "SnapAnnounce:voice").apply {
            setReferenceCounted(false)
            acquire()
        }
    }

    private fun releaseWifiLock() {
        wifiLock?.let {
            if (it.isHeld) {
                it.release()
            }
        }
        wifiLock = null
    }

    override fun onBind(intent: Intent?): IBinder = binder

    override fun onStartCommand(intent: Intent?, flags: Int, startId: Int): Int {
        when (intent?.action) {
            ACTION_START -> startAnnouncement()
            ACTION_STOP -> requestStop(getString(R.string.announce_ended))
        }
        return START_NOT_STICKY
    }

    override fun onDestroy() {
        capturing = false
        unregisterNetworkCallback()
        scope.cancel()
        super.onDestroy()
    }

    private fun startAnnouncement() {
        val running = announceJob?.isActive == true

        // Must happen on every ACTION_START, running or not:
        // startForegroundService() gives us only a few seconds to get here.
        // Text matches the current state so a repeated START doesn't reset
        // an "on air" notification back to "connecting".
        val text = if (running && _uiState.value.state == AnnounceState.ON_AIR) {
            getString(R.string.announce_running)
        } else {
            getString(R.string.connecting)
        }
        ServiceCompat.startForeground(
            this,
            NOTIFICATION_ID,
            buildNotification(text, showStop = true),
            ServiceInfo.FOREGROUND_SERVICE_TYPE_MICROPHONE,
        )

        if (running) return

        stopReason = null
        capturing = false
        _uiState.value = UiState(state = AnnounceState.CONNECTING)
        announceJob = scope.launch { runAnnouncement() }
    }

    /** Asks the running announcement to end; see the class comment. */
    private fun requestStop(reason: String?) {
        stopReason = reason
        capturing = false
        if (announceJob?.isActive != true) {
            // Nothing running (e.g. STOP arrived for a service that was only
            // bound): just make sure we don't linger as a started service.
            finish(UiState(state = AnnounceState.IDLE))
        }
    }

    private suspend fun runAnnouncement() {
        val host = settings.serverHost

        val network = wifiNetworkOrNull(connectivity)
        if (network == null) {
            finish(UiState(state = AnnounceState.ERROR, message = getString(R.string.no_wifi), serverNotFound = true))
            return
        }

        val rpc = try {
            withContext(Dispatchers.IO) {
                RpcClient.connect(
                    host,
                    SettingsStore.CONTROL_PORT,
                    CONNECT_TIMEOUT_MS,
                    READ_TIMEOUT_MS,
                    network,
                )
            }
        } catch (e: IOException) {
            finish(UiState(state = AnnounceState.ERROR, message = getString(R.string.server_unreachable, host), serverNotFound = true))
            return
        }

        // Arm first, then open the microphone: capturing before the server
        // is armed would only produce a backlog that the firmware's small
        // mailbox then carries as permanent extra latency.
        // null = armed, otherwise why not. The firmware answers a refusal
        // with result.busy; an error means it doesn't know Voice.Start at all.
        val armed = try {
            val response = withContext(Dispatchers.IO) { rpc.call("Voice.Start") }
            Log.i(TAG, "Voice.Start -> $response")
            val result = response.optJSONObject("result")
            when {
                result?.optBoolean("active") == true -> null
                result?.optBoolean("busy") == true -> getString(R.string.announce_busy)
                response.has("error") -> getString(R.string.no_voice_support)
                else -> getString(R.string.unexpected_answer)
            }
        } catch (e: IOException) {
            getString(R.string.server_no_answer)
        } catch (e: org.json.JSONException) {
            getString(R.string.unexpected_answer)
        }

        if (armed != null || stopReason != null) {
            // Either arming failed, or the user pressed stop while we were
            // still connecting -- disarm (harmless if never armed) and leave.
            withContext(Dispatchers.IO + NonCancellable) {
                if (armed == null) {
                    try {
                        rpc.call("Voice.Stop")
                    } catch (_: IOException) {
                    }
                }
                rpc.close()
            }
            finish(
                if (armed != null) UiState(state = AnnounceState.ERROR, message = armed)
                else UiState(state = AnnounceState.IDLE, message = stopReason)
            )
            return
        }

        watchNetworkLoss(network)
        capturing = true
        _uiState.value = UiState(state = AnnounceState.ON_AIR)
        updateNotification(getString(R.string.announce_running), showStop = true)

        val ticker = scope.launch {
            var seconds = 0
            while (isActive) {
                delay(1000)
                seconds++
                _uiState.update { it.copy(elapsedSeconds = seconds) }
            }
        }

        val captureError = withContext(Dispatchers.IO) {
            captureAndSend(host, network, settings.micSource, settings.maxGainDb,
                           settings.targetRmsDbfs)
        }
        ticker.cancel()
        capturing = false

        // Best effort: if this is lost, the firmware's silence watchdog and
        // the connection close right after end the announcement anyway.
        withContext(Dispatchers.IO + NonCancellable) {
            try {
                rpc.call("Voice.Stop")
            } catch (_: IOException) {
            }
            rpc.close()
        }

        unregisterNetworkCallback()
        finish(
            if (captureError != null) UiState(state = AnnounceState.ERROR, message = captureError)
            else UiState(state = AnnounceState.IDLE, message = stopReason)
        )
    }

    /**
     * Blocking capture-and-send loop. Returns null when it ended because
     * [capturing] was cleared, or an error message if it could not run.
     */
    @SuppressLint("MissingPermission") // checked by MainActivity before starting
    private fun captureAndSend(host: String, network: Network, micSource: Int, maxGainDb: Int,
                               targetRmsDbfs: Int): String? {
        val minBuffer = AudioRecord.getMinBufferSize(SAMPLE_RATE, CHANNEL, ENCODING)
        if (minBuffer <= 0) return getString(R.string.mic_no_16k)

        val recorder = try {
            AudioRecord(
                // Chosen in the app, see SettingsStore.micSource.
                micSource,
                SAMPLE_RATE,
                CHANNEL,
                ENCODING,
                maxOf(minBuffer, FRAME_BYTES * 4),
            )
        } catch (e: SecurityException) {
            return getString(R.string.mic_permission)
        }

        if (recorder.state != AudioRecord.STATE_INITIALIZED) {
            recorder.release()
            return getString(R.string.mic_open_failed)
        }

        val socket = try {
            DatagramSocket().also { network.bindSocket(it) }
        } catch (e: IOException) {
            recorder.release()
            return getString(R.string.udp_failed)
        }

        val address = try {
            network.getByName(host)
        } catch (e: IOException) {
            socket.close()
            recorder.release()
            return getString(R.string.bad_address, host)
        }

        val encoder = try {
            OpusEncoder(SAMPLE_RATE, OPUS_BITRATE)
        } catch (e: Exception) {
            socket.close()
            recorder.release()
            Log.w(TAG, "No Opus encoder", e)
            return getString(R.string.no_opus)
        }

        val samples = ShortArray(FRAME_SAMPLES)
        val packet = ByteArray(HEADER_BYTES + MAX_OPUS_PACKET)
        val datagram = DatagramPacket(packet, packet.size, address, SettingsStore.VOICE_PORT)
        var sequence = 0
        var frames = 0

        // Diagnostics, logged every STATS_FRAMES: without them "the speakers
        // stay silent" can't be told apart from "nothing left the phone".
        var sent = 0
        var failed = 0
        var sentBytes = 0L
        var micPeak = 0
        var outPeak = 0
        var outSumSquares = 0.0
        var outSamples = 0
        var lastError: String? = null
        val agc = VoiceAgc(targetRmsDbfs = targetRmsDbfs.toDouble(),
                           maxGainDb = maxGainDb.toDouble(),
                           startGainDb = minOf(20, maxGainDb).toDouble())
        Log.i(TAG, "Streaming Opus to $address:${SettingsStore.VOICE_PORT} " +
            "source=$micSource max_gain=$maxGainDb dB target=$targetRmsDbfs dBFS")

        /*
         * Round-trip measurement. The firmware echoes back every 50th
         * packet as its bare 4-byte sequence number (voice_announce.c), and
         * this thread matches it against when that packet left. Half the
         * round trip is the Wi-Fi leg of the announcement -- the one part
         * of its delay that could not be measured on either end.
         */
        val sendTimesNs = LongArray(SEND_TIME_SLOTS)
        val rttSumMs = java.util.concurrent.atomic.AtomicLong(0)
        val rttMaxMs = java.util.concurrent.atomic.AtomicLong(0)
        val rttCount = java.util.concurrent.atomic.AtomicLong(0)
        val echoThread = Thread {
            val buf = ByteArray(16)
            val reply = DatagramPacket(buf, buf.size)
            socket.soTimeout = 500
            while (capturing) {
                try {
                    socket.receive(reply)
                } catch (_: IOException) {
                    continue // timeout, or the socket was closed on the way out
                }
                if (reply.length != HEADER_BYTES) continue
                val seq = (buf[0].toInt() and 0xFF) or ((buf[1].toInt() and 0xFF) shl 8) or
                    ((buf[2].toInt() and 0xFF) shl 16) or ((buf[3].toInt() and 0xFF) shl 24)
                val sentNs = sendTimesNs[seq and (SEND_TIME_SLOTS - 1)]
                if (sentNs == 0L) continue
                val rtt = (System.nanoTime() - sentNs) / 1_000_000L
                rttSumMs.addAndGet(rtt)
                rttCount.incrementAndGet()
                if (rtt > rttMaxMs.get()) rttMaxMs.set(rtt)
            }
        }
        echoThread.isDaemon = true
        echoThread.start()

        val oldPriority = Process.getThreadPriority(Process.myTid())
        Process.setThreadPriority(Process.THREAD_PRIORITY_URGENT_AUDIO)
        acquireWifiLock()

        try {
            recorder.startRecording()
            if (recorder.recordingState != AudioRecord.RECORDSTATE_RECORDING) {
                return getString(R.string.record_failed)
            }

            while (capturing) {
                // 10 ms per read; the encoder collects them into its own
                // frames and hands back a packet as soon as one is complete.
                var filled = 0
                while (filled < FRAME_SAMPLES && capturing) {
                    val n = recorder.read(samples, filled, FRAME_SAMPLES - filled, AudioRecord.READ_BLOCKING)
                    if (n < 0) return getString(R.string.mic_read_error, n)
                    filled += n
                }
                if (!capturing) break
                frames++

                micPeak = maxOf(micPeak, peakOf(samples))
                agc.process(samples)
                outPeak = maxOf(outPeak, peakOf(samples))
                for (s in samples) {
                    val v = s.toDouble()
                    outSumSquares += v * v
                }
                outSamples += samples.size

                encoder.encode(samples) { payload, length ->
                    // Wire format, see voice_announce.c: 4-byte little-endian
                    // sequence number, then the Opus packet.
                    val seq = sequence++
                    packet[0] = seq.toByte()
                    packet[1] = (seq ushr 8).toByte()
                    packet[2] = (seq ushr 16).toByte()
                    packet[3] = (seq ushr 24).toByte()
                    System.arraycopy(payload, 0, packet, HEADER_BYTES, length)
                    datagram.length = HEADER_BYTES + length
                    sendTimesNs[seq and (SEND_TIME_SLOTS - 1)] = System.nanoTime()
                    try {
                        socket.send(datagram)
                        sent++
                        sentBytes += HEADER_BYTES + length
                    } catch (e: IOException) {
                        // A lost datagram is a gap of one frame; never wait or
                        // retry, same contract as the firmware side.
                        failed++
                        lastError = e.toString()
                    }
                }

                if (frames % STATS_FRAMES == 0) {
                    val seconds = STATS_FRAMES * FRAME_SAMPLES.toDouble() / SAMPLE_RATE
                    Log.i(
                        TAG,
                        ("sent=$sent failed=$failed rate=%.0f kbit/s mic_peak=%.1f dBFS " +
                            "out_peak=%.1f dBFS out_rms=%.1f dBFS gain=%.1f dB floor=%.1f dBFS " +
                            "mic_lag=%.0f ms enc_lag=%.0f ms rtt=%d/%d ms%s").format(
                            sentBytes * 8 / seconds / 1000.0,
                            dbfs(micPeak),
                            dbfs(outPeak),
                            if (outSamples > 0) {
                                val rms = kotlin.math.sqrt(outSumSquares / outSamples)
                                if (rms > 0.0) 20.0 * log10(rms / 32767.0) else -120.0
                            } else {
                                -120.0
                            },
                            agc.gainDb,
                            agc.floorDbfs ?: -120.0,
                            micLagMs(recorder, frames.toLong() * FRAME_SAMPLES),
                            encoder.backlogMs,
                            if (rttCount.get() > 0) rttSumMs.get() / rttCount.get() else 0L,
                            rttMaxMs.get(),
                            lastError?.let { " last_error=$it" } ?: "",
                        ),
                    )
                    sentBytes = 0
                    micPeak = 0
                    outPeak = 0
                    outSumSquares = 0.0
                    outSamples = 0
                    lastError = null
                }
            }
            return null
        } finally {
            try {
                recorder.stop()
            } catch (_: IllegalStateException) {
            }
            recorder.release()
            encoder.release()
            socket.close()
            releaseWifiLock()
            Process.setThreadPriority(oldPriority)
        }
    }

    /**
     * How old the audio just read from [recorder] already was, in
     * milliseconds: the delay of the phone's own capture chain, from the
     * microphone through the audio HAL to this thread.
     *
     * AudioRecord.getTimestamp() gives a frame position together with the
     * monotonic time at which that frame was captured. The difference
     * between the frames read since then and that anchor, plus the time
     * since, is the lag. Returns 0 when the device does not supply a
     * timestamp, which some do not.
     */
    private fun micLagMs(recorder: AudioRecord, framesRead: Long): Double {
        val ts = AudioTimestamp()
        if (recorder.getTimestamp(ts, AudioTimestamp.TIMEBASE_MONOTONIC) != AudioRecord.SUCCESS) {
            return 0.0
        }
        val pending = framesRead - ts.framePosition
        val sinceAnchorMs = (System.nanoTime() - ts.nanoTime) / 1_000_000.0
        return pending * 1000.0 / SAMPLE_RATE + sinceAnchorMs
    }

    private fun peakOf(samples: ShortArray): Int {
        var peak = 0
        for (s in samples) {
            val a = if (s < 0) -s.toInt() else s.toInt()
            if (a > peak) peak = a
        }
        return peak
    }

    private fun dbfs(peak: Int): Double =
        if (peak > 0) 20.0 * log10(peak / 32767.0) else -120.0

    /**
     * If the Wi-Fi the announcement runs on goes away, stop -- rather than
     * let the UI keep claiming "on air" while datagrams go nowhere. The
     * sockets are bound to this network, so Android cannot silently move
     * them to mobile data either.
     */
    private fun watchNetworkLoss(network: Network) {
        val request = NetworkRequest.Builder()
            .addTransportType(NetworkCapabilities.TRANSPORT_WIFI)
            .build()
        val callback = object : ConnectivityManager.NetworkCallback() {
            override fun onLost(lost: Network) {
                if (lost == network) requestStop(getString(R.string.wifi_lost))
            }
        }
        networkCallback = callback
        connectivity.registerNetworkCallback(request, callback)
    }

    private fun unregisterNetworkCallback() {
        networkCallback?.let {
            try {
                connectivity.unregisterNetworkCallback(it)
            } catch (_: IllegalArgumentException) {
            }
        }
        networkCallback = null
    }

    private fun finish(state: UiState) {
        _uiState.value = state
        ServiceCompat.stopForeground(this, ServiceCompat.STOP_FOREGROUND_REMOVE)
        stopSelf()
    }

    private fun createNotificationChannel() {
        val channel = NotificationChannel(
            CHANNEL_ID,
            getString(R.string.tab_announce),
            NotificationManager.IMPORTANCE_LOW,
        )
        getSystemService(NotificationManager::class.java).createNotificationChannel(channel)
    }

    private fun buildNotification(text: String, showStop: Boolean): Notification {
        val open = PendingIntent.getActivity(
            this,
            0,
            Intent(this, MainActivity::class.java),
            PendingIntent.FLAG_UPDATE_CURRENT or PendingIntent.FLAG_IMMUTABLE,
        )
        val builder = NotificationCompat.Builder(this, CHANNEL_ID)
            .setContentTitle(getString(R.string.app_name))
            .setContentText(text)
            .setSmallIcon(R.drawable.ic_notification)
            .setContentIntent(open)
            .setOngoing(true)
            .setPriority(NotificationCompat.PRIORITY_LOW)

        if (showStop) {
            val stop = PendingIntent.getService(
                this,
                1,
                Intent(this, VoiceAnnounceService::class.java).setAction(ACTION_STOP),
                PendingIntent.FLAG_UPDATE_CURRENT or PendingIntent.FLAG_IMMUTABLE,
            )
            builder.addAction(0, getString(R.string.action_stop), stop)
        }
        return builder.build()
    }

    private fun updateNotification(text: String, showStop: Boolean) {
        getSystemService(NotificationManager::class.java)
            .notify(NOTIFICATION_ID, buildNotification(text, showStop))
    }

    companion object {
        private const val TAG = "SnapAnnounce"

        /** Log line every 2 s of audio (10 ms frames). */
        private const val STATS_FRAMES = 200

        const val ACTION_START = "com.pillepalle.snapannounce.action.START"
        const val ACTION_STOP = "com.pillepalle.snapannounce.action.STOP"

        private const val CHANNEL_ID = "voice_announce"
        private const val NOTIFICATION_ID = 1

        /** How long reaching the server may take before "not reachable". */
        private const val CONNECT_TIMEOUT_MS = 1500

        /** Waiting for an RPC answer. Longer than the connect: the server's
         *  control task can be slow to answer while the mesh is busy. */
        private const val READ_TIMEOUT_MS = 5000

        /*
         * 16 kHz, not 48: at 48 kHz and 32 kbit/s Opus picks its hybrid mode
         * (SILK and CELT at once), the most expensive one to decode. On the
         * server that took ~6 ms of CPU per 20 ms packet next to the music
         * encoder -- core 1 ran at 97 % and the announcement stuttered
         * (2026-09-19). Wideband speech is pure SILK, several times cheaper,
         * and 8 kHz of audio bandwidth is plenty for announcements. The
         * ESP32s still decode to 48 kHz; Opus resamples internally.
         */
        private const val SAMPLE_RATE = 16000
        private const val CHANNEL = AudioFormat.CHANNEL_IN_MONO
        private const val ENCODING = AudioFormat.ENCODING_PCM_16BIT

        /** Microphone reads of 10 ms; the encoder makes its own frames. */
        private const val FRAME_SAMPLES = SAMPLE_RATE / 100
        private const val FRAME_BYTES = FRAME_SAMPLES * 2

        /** Wire format, see voice_announce.c. */
        private const val HEADER_BYTES = 4

        /** Send times kept for the round-trip measurement; power of two. */
        private const val SEND_TIME_SLOTS = 256
        private const val MAX_OPUS_PACKET = 1275

        /** Wideband speech is clear at this rate; raw PCM was 768 kbit/s. */
        private const val OPUS_BITRATE = 24000
    }
}
